Arcadesys/tak-box/docs/V22_SEAMLESS_CHECKPOINT.md

Superseded name: this seamless design is now **V23**. See [V23 checkpoint](V23_CHECKPOINT.md). The historical ZIP is preserved at `v22/release/archive/tak-v22-seamless-before-v23.zip`; V22 source and guide now refer to the original corner-hook baseline. The following records the earlier delivery.

# V22 seamless exterior revision

Outcome: rounded flush closed exterior, recessed centered outer-side hook including pivot/collar/catch, recessed offset board grips, and integrated rounded hinge-end shoulders. Preserve 32.6 mm thickness, full 180 mm field, exact original 42 flats and solid 8 mm Cat/Witch capstones, captive main hinges. User authorized this local revision; no printer job or merge.

Route: short design plan for centered closure/board motion and embedded hinge-end clearance, then bounded workhorse/medium implementation and focused checks in this context. Maintained role mapping read; no model switch or delegation claimed. Actual model/effort and usage counters unavailable.

Plan: recess closure into spare side margin ahead of the first stone column; remove projecting board tab, add broad rounded grips offset along the side. Move opposed hinges into end margins outside the field, retaining their 3 mm pins and 0.4 mm gaps, and replace rectangular roots with rounded shoulders. Verify cropped actual closure and hinge-end geometry before full exports/slicing. Then check exact loaded geometry and motion, meshes/readback, slices/layers, provenance and freshly extracted revised ZIP.

Baseline preserved: existing v22/release/tak-v22-print-kit.zip and its 02f8a09 source revision; new archive will be named tak-v22-seamless-print-kit.zip. V18–V21 and user-extracted folders remain untouched.

Current: implementation and digital checks complete. Closed envelope 101×200×32.6 mm (baseline 111.8×220.2×32.6); hook parks at 90° below the boards. Eight full parts across three plates: 41,899 s / 272.16 g. Optional hinge trial 1,556 s / 5.31 g; closure trial 3,175 s / 13.39 g. All required replacement parts are explicit in the guide; capstone CAD unchanged.

Evidence: 59 geometry, 37 field, eight hardware, 29 exterior/access/wall, 254 preliminary mechanism, 20 plate, three filament toolpath, 32 captive-hinge, 20 capstone, eight hinge-trial and 129 closure-trial checks pass. Three full slices and two trial slices match named exported meshes and placement. Selected layers, captive-gap plots and exported CAD previews reviewed. Baseline ZIP hash matches docs/V22_BASELINE_ARCHIVE.json. Fresh revised-ZIP audit passes: 122 payload hashes, Python syntax, 14 local links, all eight independently reconstructed parts with zero Boolean symmetric difference, and unchanged baseline ZIP hash. Receipt: docs/V22_SEAMLESS_PACKAGE_CHECK.json. Archive SHA-256: d48410b2b090c39770dcf3f2bf56b243482c84fbbc51b89927d7b21dd7d633a4. Defining source: 4859c9cdd515cd7f12324a99423b8795fa7984ac. V18 freeze and V19–V21 package verifiers pass; no prior-version tracked files changed.

Delivery: v22/release/tak-v22-seamless-print-kit.zip; guide v22/START-HERE.md; actual-geometry views v22/previews/02-closed.png, 04-hook-closed.png, 05-hook-open.png and 12-rounded-hinge-end.png. Committed and pushed on codex/v22-print-in-place. Draft PR #27 is updated as “V22: recessed center hook, rounded hinge ends and flush board grips” (https://github.com/Arcadesys/tak-box/pull/27); not merged. Geometry/source commit 4859c9c and packaged artifact commit 19b8773. No physical acceptance observed. Next small physical trial is the supplied 53-minute recessed closure coupon, followed by the 26-minute hinge coupon; the full build is also supplied. No printer job, merge, paid generation or new agent.
