Arcadesys/tak-box/docs/V23_BOARD_INLAYS_CHECKPOINT.md

# V23 board inlays checkpoint

Outcome: a separate replacement for V23 sliding-board plate 02 with flush black/white grid and retained celestial artwork, assigned to two separate silk accent slots. User selected V23 on October 6, 2026 after resolving the older checkout's V18 instructions.

Scope: `v23/board-inlays/`, its links in the V23 guide and project brief, this checkpoint and generated-file review attributes. Retain full 180 mm 5×5 field, 36 mm pitch, existing slide/catch/grip interfaces, all base/hook/capstone geometry and original kits. Exact piece package: V23 original Cat/Witch 20×20×8 mm flats and supplied solid flat Cat/Witch capstones. Weighted and curled sets remain unqualified.

Route: one bounded workhorse/medium pass in the existing execution context. Role mapping read; no model switch or delegation claimed. Actual model/effort and usage counters were not exposed. Source baseline 071469c on `codex/v23-seamless`; focused branch `codex/v23-board-inlays` in a managed isolated worktree. Original primary-checkout modification to a V16 3MF is untouched.

Current: separate black/white and four-colour board projects and small trial projects built. V17's 0.8 mm recessed grid is filled to the V23 face. V16 celestial CAD is reused in its original cell positions, translated to Z15.3. Inlays are 0.6 mm deep. The trial measures 90.2×36.8×1.8 mm and includes two full cells plus the seam half-cell. Gold and purple are example preview colours. Slots 3 and 4 follow the original V16 orange/purple motif groups. Silk uses two clearly labelled generic PLA placeholders; select both actual spool profiles and reslice before printing.

Evidence: 275 fresh CAD/mesh/STEP/field/piece/motion/3MF checks pass in `v23/board-inlays/reports/geometry.json`. All four CC2 local dry slices pass named mesh, colour-slot and placement readback in `reports/slicing.json`. Eight actual Gcode colour-layer checks pass in `reports/colour-layers.json`, with white/accent deposition at board locations on the six expected 0.10 mm inlay layers. Actual exported STEP previews and the last sliced inlay layer were inspected. `reports/package-audit.json` records the release ZIP's payload count, SHA-256, CRC, syntax and four-project audit; its root contains dependency sources and the option guide.

Commands: `python v23/board-inlays/source/build.py`, `render.py`, `slice.py`, `inspect_layers.py`, `package.py`, all via `/Users/arcades/Documents/GitHub/tak-box/.venv/bin/python`. Dependency versions, platform, source hashes, profile hashes and exact slicer commands are recorded in the option reports and `source/requirements.txt`. Renderer uses VTK. Installed ElegooSlicer CLI uses the retained CC2 0.4 mm printer profile, 0.10 mm layers after a 0.20 mm first layer, supports and a prime tower.

Corrections during verification: the first full-board readback detected a 0.001012 mm Z shift from using OCC's tolerance-expanded bounding box. Plate placement now uses actual tessellation minima; the repeated readback passes with float32-level error. The initial toolpath parser missed extrusion values written with a leading decimal point (for example `E.04`); numeric parsing was corrected and all expected coloured deposition layers now pass. No geometry or slicer assignment defect was inferred from that parser failure. Generated logs retain the final successful run; these earlier checker failures are recorded here.

Limitations: motion is sampled, not a continuous swept-volume proof. The extracted ZIP passed isolated dependency import and CAD smoke checks. Physical colour purity, adhesion, silk bonding, surface feel, rail friction and loaded retention remain unchecked. The trial does not test rails or catches; dry-fit one full replacement board before printing its mate. No printer job, paid generation, merge or physical acceptance is claimed.

Next: review the replacement option, print the small colour/finish trial with selected material profiles, then test one full board. The existing full-case plates 01 and 03 remain the source for bases and hardware.

Delivery: the option is reviewed in [PR #29](https://github.com/Arcadesys/tak-box/pull/29), stacked on the retained V23 branch. The initial one-accent delivery was committed at 2e4a839; the user explicitly requested two accent colours on October 6, 2026. The follow-up restores the separate original orange/purple artwork groups, uses four filament slots, and removes the combined-art exports and single accent placeholder. Geometry, colour-layer, slicing and archive receipts have been regenerated. Current ZIP checksum and payload count are in `v23/board-inlays/reports/package-audit.json`.
