Arcadesys/tak-box/docs/V26_CHECKPOINT.md

# V26 mechanism review checkpoint

## Contract and route

Outcome: a reviewable wider sliding-board clip and captive side-hook candidate, with print-ready small trials and current CAD/mesh/3MF/motion/slicer evidence. Scope: new v26 package, controlling guides and focused branch/PR; preserve V25/V24 kits and user-extracted folders. Completion evidence is digital geometry, readbacks, actual CAD previews and dry slices. Physical strength is not inferred.

Route: bounded workhorse / medium in the existing execution context; maintained role mapping read. No model switch claimed; no agents. Named design uncertainty: captive-hook print support and collision-free motion. Resolved with targeted geometry checks before the integrated verification pass.

## Current state

Parent: c101d7d6585c363e23cf140f9059f38a96a8d6c8 on codex/v25-fixed-piece-guides (draft PR #35). V26 branch: codex/v26-captive-hook-catch. Thin-clip report confirmed by user as the small sliding-board clip. User explicitly asks for a PIP hook. Original 1.2 mm arm becomes 2.4 mm, gradual 3.2 mm root and 1.2 mm blend; same 54 mm plan span and assumed 2.8 mm flex travel. No stress, force or fatigue rating claimed.

The hook keeps its closure lever/tooth, enlarges its bearing to 11.6 mm outside diameter and prints parked on an integral foot. Fixed 4 mm axle, 2 mm outer cheek, 0.4 mm radial/face clearances. Existing filament passage is filled, avoiding an isolated internal void. A 7 mm rotating relief clears the foot; the 3.4 mm fixed lower frame bridge sits outside that sweep. Hook moves 0.4 mm inward; board notch extends from X5.7 to X6.2 outside the full field. Original keeper remains.

Rejected first hook fit had 0.454 mm3 overlap at 30 degrees and 0.908 mm3 at 90 degrees. The original export failed the single-component mesh check because the unfilled old pivot bore became an enclosed void (negative 14.763 mm3 inner shell). Neither rejected export is delivered as a print project. Failure records are retained. Final solid topology is checked before slicing.

Fixed guides, main PIP geometry, full field, exact original flat/capstone package and outside dimensions are retained. Both integrated bodies/boards require replacement; hook prints with the left body, no inserted axle or collar. Small trials isolate the hook bearing and complete clip; hook trial has a thickened fixture floor outside the moving envelope. Whole-case loaded strength and rounded-cover underside integration remain pending.

## Evidence and next step

Build: source/build.py; trials: source/trial.py; dry slice/readback: source/slice.py; actual CAD views: source/render.py. Python 3.12 / CadQuery 2.7 / ElegooSlicer 2.4.2 on the recorded host. Reports retain exact commands, profiles, hashes and failures. No printer dispatch or physical acceptance.

Next physical gate: cool and gently free the captive hook, pull along its axle both ways, inspect axle/cheeks after 20/100 cycles; insert/release the full-length clip by hand and inspect its root/effort after 20/100 cycles. Reject fused motion, cracks or excessive release effort. Complete-case print and loaded transport follow only after mechanism trial observations.

The parked lever has underside clearance outside the piece wells. A final audit rejected the original 0.173 mm lever-to-well-corner gap; the revised underside opening clears that region. The 3.4 mm stone floors and fixed guides remain intact.

Final digital evidence: 908 integrated solid, loaded-piece, slide/fold, capture, mesh and 3MF checks; 96 mechanism-trial checks; 51 exported material/clearance/keeper audits. The locked hook obstructs early opening at 179/178/177 degrees; that is nominal geometric retention, not a force rating. Own-body clearance is 0.4 mm through checked 0–90 degree hook travel. Eleven actual dry-sliced hook radial/face-gap and support-centerline checks pass, minimum sampled conservative 0.50 mm bead-edge gap 0.32 mm. Both trial projects preserve named watertight meshes within 0.002 mm surface / 0.05 mm3 volume tolerance. Four walls, 0.20 mm layers, build-plate-only supports, no brim, CC2 PLA; inherited bed metadata warning retained. Hook trial: 1,493 s / 4.93 g; clip trial: 2,537 s / 9.51 g. Seven actual CAD/path images reviewed with large captions and a clear longitudinal bearing section. Review still awaits physical prints; full sliced V26 kit and rounded-cover underside remain open.

Package evidence: all six preceding V25 ZIPs remain byte-identical. An isolated extraction of the V26 review rebuilt both small trials without the checkout; all four rebuilt STL surfaces and volumes match within the recorded tolerances. This does not claim an isolated full-CAD or slicer rebuild. Captions are composed in a separate PIL-only process to avoid dropped leading glyphs after repeated VTK renders. The V26 review is stacked on open draft PR #35; no merge or printer dispatch.

## Combined trial plate

User asks for both trials on one plate. Route: bounded workhorse / medium in the existing context, no model switch or agents. Scope: placement and grouping only; unchanged hook/clip geometry and individual projects. New source/combine.py imports the four actual exported STEP parts, moves both clip parts 32 mm in X, leaves the captive hook/mount unchanged and exports one assembly of four named meshes. Hook-to-clip spacing is 17 mm; all parts fit the CC2 bed. Nineteen placement, topology and 3MF checks pass. New combined slice receives the existing mesh/profile readback and eleven radial/face/support checks; physical acceptance remains unchecked. No complete-case geometry recheck is needed for unchanged parts.

Combined slice passed: 3,925 s / 13.92 g PLA; four named watertight mesh readbacks, preserved one-assembly placement and eleven hook bearing/support checks. Individual projects remain byte-identical to a1a9b2709323d74d3e68bea22fd73d9dbbc3133d. Combined CAD placement preview reviewed; package repacked. Physical strength and release remain pending.

## Board-release ergonomics assessment

User reports that pressing the sliding-board tab while pulling the board was very awkward. A thicker clip does not resolve that simultaneous action. Proposed next direction: remove the individual flex catches and restore solid board margins; let the opened case hook release both boards for withdrawal. User choice between this approach and a separate latch that stays released is pending. No geometry changed in this assessment, and the combined plate still contains the stronger flexible-clip candidate.

Route: bounded workhorse inspection in the existing context; no model switch or delegation. Source revision: eb1a114f773069a6a662d7f2cea9456f901bac51. Environment: existing CadQuery 2.7 / Python 3.12 CAD runtime. Command: import v26/source/build.py; for each side use board(side, c.BOARD_RELEASE), apply c.slide at 0, 1, 2, 3, 4, 5, 6, 8 mm, fold the right board 180 degrees, and measure ov against hook(0) and hook(90). The assumed released clip isolates the hook obstruction from the individual clip.

Results: both seated boards have zero hook overlap; at 1 mm withdrawal the closed hook overlaps left board by 6.416685 mm3 and folded right board by 5.085218 mm3. Closed-hook overlap remains positive at all checked 2–8 mm positions. The parked 90-degree hook has zero overlap with both boards at each checked position. This supports a candidate shared retention mechanism; it does not establish retention force, comfort, or unlatched board security. Full removal, loaded motion, restored-margin clearance, mesh/readback and physical handling must be checked after any geometry change. Existing sliced trials and ZIP remain unchanged.

## Full plate build authorized

User approves shared hook retention and explicitly asks to build the plates without waiting for the small trials. Scope: remove board flex tabs, restore bevelled solid margins, retain PIP hinges/fixed guides/captive side hook/full field/original inlays and build the complete sliced CC2 kit. No printer dispatch. Preserve the previous mechanism-review ZIP and all V25 assets. Route: workhorse / medium in the existing execution context; no model switch or agents. Completion evidence: integrated solids and loaded motion, shared hook obstruction, vertical rails and inward stops, exported meshes and native 3MF placement/material readbacks, actual dry-sliced hinge/hook gaps, exported-CAD previews and package readback. Strength and handling remain physical observations, now deferred at the user's instruction.

The first full build passed the slide/loaded-fold checks but failed the added 1 mm inward-stop check: removing the flexible catch also removes its inward seating stop. Preserved failure log: v26/reports/build-full-initial-failure.log. The old case-only stop catches later (positive at 12 mm); it is insufficient for independently seated closed covers. Narrow repair: a rigid 4 x 6.1 x 4.7 mm shoulder outside the field, X52.6..56.6/Y2.7..8.8/Z11.8..16.5 (mirrored right), meets the front rail's X57 start. It has 0.3 mm clearance to the front wall and shares the original flat underside. Focused left trial: zero seated/outward overlap at 0, 0.5, 1, 2, 4, 8, 16, 32, 54, 80, 106 mm; positive inward overlap 0.072 mm3 at 0.5 mm and 0.432 mm3 at 1 mm. This is a fixed seating shoulder, not a pressable catch; the case bodies and inlays remain unchanged. Full affected checks rerun after this repair.

Final full-plate digital evidence: 916 integrated CAD checks, 62 full board/capstone export and raw plate checks, 51 exported material/closure audits, all 15 named sliced meshes read back within 0.002 mm surface / 0.05 mm3 volume tolerance (maximum observed surface error 0.00001714 mm), and 25 main-hinge/hook bearing checks. Minimum sampled conservative 0.50 mm bead-edge gap is 0.3191 mm; no sampled support centerlines enter the bearing cavities. All three slices are inside the CC2 build volume. Three actual colour-deposition checks verify white and both accents on six 4.2..4.7 mm layers, excluding the prime tower. Current estimates: body/hook 34,079 s / 164.56 g, board pair 28,854 s / 121.19 g, optional capstones 990 s / 3.78 g; total 63,923 s / 289.53 g. Four walls throughout; 0.20 mm case/capstone and 0.10 mm boards; actual silk profiles remain placeholders. The inherited bed metadata warning is retained.

Rendered exported CAD and sampled actual paths were inspected. Initial case-plate render failed on the new captive-hook label; the colour mapping was repaired (full-render-initial-failure.log). Reusing a PIL font also dropped the leading Plate glyphs from the second plate caption; fresh font instances per image repaired this, and the legible board caption was reviewed. Capstone shading was darkened against the white background and labelled by position for accessible review. Current kit is V26-PRINT-KIT.zip / FULL-PRINT, with START-HERE instructions and reproducible bundled sources. Physical strength, comfort, wear, loaded dumping/transport and the V17-style underside remain unobserved. No printer dispatch.

Package completion: 141 ZIP entries audited by CRC, byte counts and SHA256. All six preceding V25 archives and the prior V26 mechanism-review ZIP remain byte-identical (seven preserved archives). In an isolated extraction, all ten named raw board meshes and both capstone meshes rebuilt with identical vertex arrays and triangle records. This rebuild uses bundled exported STEP geometry for boards and procedural capstone source; it does not independently repeat the full case CAD or slicer run. Reports/full-reproduction.json names the exact final ZIP hash. The authoritative worktree remains the V25-managed checkout on codex/v26-captive-hook-catch, stacked draft PR #36; the user's untracked v25/PIP-FIXED-STORAGE/v25 extraction is preserved.

## Main hinge mismatch reported by user

The user supplied a main-hinge close-up and states that it is not the captive hinge discussed. Current sources confirm the main joints are inherited opposing single-ended peg/socket stations (case.py pip_pin/pip_socket and PIP_STATIONS), while only the side hook has an axle fixed between cheeks. The earlier B filament study instead places a central moving bearing between two fixed supports (STRENGTH-TRIAL and REINFORCED-B-TRIAL FIXED/MOVING; production FIXED-STORAGE has two such stations). The switch to PIP restored the older V16 mechanism instead of carrying that support arrangement forward. Digital checks covered the delivered geometry, not fidelity to that intended hinge design. Prior full ZIP is preserved and the local guide is marked under correction.

Outcome/scope: identify and correct only the main hinge mechanism while preserving fixed guides, tab-free covers, hook retention, original pieces and field. Route: mechanism judgment in the existing context, then bounded workhorse CAD/slicing; no model switch or agents. Pending user clarification: printed axle permanently fixed between two supports on one half, with the other half's central bearing around it. No main-hinge geometry changed yet. Next: confirmed hinge arrangement, actual exported hinge detail before regenerating full case/cover motion, mesh and 3MF/slicer evidence. Current case plate and ZIP must not be described as the corrected captive design.

## Double-supported main hinge confirmed

User confirms the intended main hinge: two fixed supports holding a printed axle, with the opposite half's moving barrel trapped between them. Outcome: replace only main hinge stations and regenerate current V26 case plate/kit, retaining tab-free covers/fixed guides/side hook/full field. Scope: two 9 mm outer barrels, each 3.2 mm moving bearing between 2.5 mm fixed cheeks; integral 4 mm axle, 0.4 mm radial and face gaps, full-height 8 mm roots, original common axis X98/Z17.5 and 102.5 x 200 x 35 mm envelope. Role: bounded workhorse execution in this context after clarified mechanism judgment; no model switch or agents. Evidence required: both supports/axle as one fixed solid, closed moving bore and bidirectional capture at each station, integrated loaded slide/fold, exported mesh/3MF and actual revised bearing paths, then revised full kit. Superseded opposed-pivot ZIP and case plate are preserved under v26/archive/previous-main-hinge (ZIP db35b5db3caee5e3d9949e3dc533835be2de00983649a9685ad243a3e22b97fa). Physical strength remains untested.

### Corrected captive main hinge evidence

`build.py` with the retained CAD Python 3.12.13 / CadQuery 2.7.0 environment passes 943 checks (`reports/build-double-supported.log`, `geometry.json`). Both axles and four supports belong to one fixed body; each central moving barrel has a closed bore, axial capture in both directions, radial capture and full-height roots. Loaded fold 0–180 degrees every 2 degrees and board slide 0–106 mm every 2 mm pass. Exported review audit passes 51 checks. Full CAD renders include enlarged main-hinge and section views; final captions use the system Arial font to avoid missing initial glyphs observed with the Matplotlib font.

ElegooSlicer 2.4.2 dry-sliced the revised raw case assembly. The first support-face verifier incorrectly selected tiny infill/perimeter gaps inside the barrel; the corrected verifier probes the two nominal CAD face interfaces directly, rejects extrusion covering either gap midpoint, and measures nearest bead edges. Final `slice_full.py --case-only --verify-only` validates the existing new slice without repeating it: 37 main/hook path checks pass, minimum main support-face gap 0.3202565 mm with assumed 0.50 mm bead width, and no support centerlines in bearing/face cavities. Three case meshes and the 12 unchanged board/capstone meshes pass readback. Both other raw/sliced plates and profiles match the earlier SHA256 receipts. Revised case 34200 s / 163.81 g; kit total 64044 s / 288.78 g. No printer dispatch or physical acceptance.

Packaging passes: 145 ZIP entries, 144 audited payloads, 8 preserved archives. Isolated board/capstone rebuilding reproduces all 12 named meshes with identical vertices and triangles; full case CAD and slicing are covered by the current local build/readback, not independently rerun in extraction. Corrected ZIP SHA256: 57fdf9cab1ff7c38fd1a899682711cd065d6e87db9d090b236bdf5537b6bec55. Source compilation and git diff whitespace checks pass. Next: push the focused PR and review the actual print for freedom, cracking, looseness, loaded retention and handling. Old printed components/ZIPs remain preserved.

### Modest outside corner rounds — October 8

User asks for a little rounding while this work continues. Scope: increase the two outside case corners per half from 3 mm to 4 mm radius and add 2 mm rounds to the boards’ two outside corners, away from the common hinge axis. Preserve the 180 mm field, inlays, guide geometry, latch and full-height hinge supports. Proposed 4 mm case cuts remove about 24 mm3 per corner and retain one valid solid; rerun integrated clearances, exports, board plates and slices because board geometry now changes. The earlier unchanged-board slice receipts apply only to the pre-rounding snapshot. Role remains bounded workhorse in the same context.

Rounded build passes 947 integrated CAD checks, 51 exported audits and 62 regenerated board/capstone plate checks. All three full projects are sliced again and pass 15 named mesh readbacks plus 37 main-hinge/hook path checks. Estimates: case 34152 s / 163.71 g; boards 28819 s / 121.17 g; capstones 990 s / 3.78 g; total 63961 s / 288.66 g (17h 46m). Actual exported corner preview shows the case and seated board together. No geometry changes to guide layout, original inlays or the confirmed captive axle/support arrangement. Current geometry build log: build-double-supported-rounded.log. Physical tests remain open.

Final rounded kit audit: 148 ZIP entries / 147 checked payloads, 8 preserved archives, and all 12 isolated board/capstone meshes reproduce identical vertices/triangles. ZIP SHA256: fdd45edecb9544de774ffb7beedfaa130afc947a700d40090deb65c717c5aaad. Current source compilation and whitespace checks pass. Ready for focused PR update; actual hinge strength, wear, handling and loaded retention remain unchecked.
