Arcadesys/tak-box/v18-case/ACCEPTANCE.md

# V18 full-build physical acceptance

User reports the clasp trial has been printed. The user also confirms their earlier hinge test used 1.75 mm PLA filament and reports it held in place. Its component revision, loads and cycle count are unknown. The revised side-hook / 2.0 mm-bore complete case has no observed physical acceptance yet.

Record component revision/project hashes, filament, spool preset, temperatures, support settings, photos and measured failures. Keep every unobserved item unchecked.

- [ ] Both housings and all spring sections print cleanly; supports remove without damage.
- [ ] All four leaves rotate freely on the shared axis; filament pins stay retained and caps clear the field.
- [ ] Filament passes through every 2.0 mm printed bore without forcing; bonded end caps hold while leaves rotate freely.
- [ ] Both board snaps engage comfortably, locate a flat 5×5 field and release without tools.
- [ ] Both drawer buttons latch positively and release comfortably.
- [ ] Drawer stops retain the drawers at full access and deliberately release for maintenance.
- [ ] All 42 original flats fit, stay enclosed while folding and can be grasped individually.
- [ ] Both original capstones can be retrieved comfortably, including using the floor finger ports.
- [ ] Hatch is captured, latches closed and does not release during carrying.
- [ ] Hook seats over the headed pin and completes ten gentle release cycles without damage.
- [ ] Hook pivot friction holds its position in every carrying orientation and remains comfortable to operate.
- [ ] Hook does not rotate open during shake, inversion or ordinary contact; repeat after wear cycles.
- [ ] Pins stay fixed at their designated stationary mounts; all intended moving joints remain free of adhesive.
- [ ] Loaded opening and repacking never expose an unsupported piece.
- [ ] Loaded shake/invert/carry tests retain all flats and capstones without objectionable rattle.
- [ ] Loaded field stays aligned without excessive rocking or permanent pin bending.
- [ ] Longer repeated-operation test shows no cracks, whitening, permanent set or sticking.
- [ ] Record actual full hardware envelope, finger effort and play.

Stop for binding, forced assembly, cracks, whitening, stuck buttons, unexpected release or lost hardware. Report the component and direction of motion. Digital clearance is not physical success.
