Arcadesys/tak-box/full-size-pagoda-v1/CHECKPOINT.md

# Home-board cassette comfort checkpoint

Outcome: easier flat access and recessed grips for a loaded two-handed lift.
Route: one bounded workhorse pass; medium effort requested by maintained role
mapping. Desktop model/effort was not switched or independently verified.
Scope: cassette geometry, exported tray files, previews, checks and documentation.
Baseline: 88bc668 (merged PR #19); branch codex/cassette-comfort.

Current state: dividers lowered to 20 mm (8 mm exposed flat edge); 20 mm row
notches; 0.5 mm contact chamfers. Two 50 x 10 mm side recesses have 45-degree
roofs, retaining a nominal 6 mm rim before chamfer and 4 mm seat at the
deepest roof. Layout 5+5+6+5,
capstone seats, outside size and stack registration remain compatible digitally.

Evidence: full geometry/mesh/3MF build passes (13 meshes, 9 plates), including
all 21 exact Cat/Fox pieces, grip void/ledge witnesses and old/new stack orders.
Tray slice passes without supports (181.97 g, 12325 s); eight unchanged plates
reuse exact input-hash-matched slice evidence. Eight actual-mesh previews;
partial cassette, side grip and full Cat/Fox access views inspected.

Resolved build failure: a combined contact chamfer produced invalid geometry.
Cleaned geometry and separately validated edge groups produce a valid solid.
No model geometry was repaired after export. Unchanged meshes are byte-identical.

Blockers/limits: physical grasp, grip-rail flex, printed release and transport
retention untested. Next: one cassette loaded handling trial before printing
its mate; compare stacking to the previous cassette if available. No printer
job or paid generation initiated. Review: https://github.com/Arcadesys/tak-box/pull/20 (draft).
