Arcadesys/tak-box/home-board-compact-v1/CHECKPOINT.md

# Compact home-board checkpoint

Outcome: smaller footprint and height, preserving the current playing space.
Scope: additive home-board-compact-v1 package, project brief and README links.
Route: one bounded workhorse pass; medium effort requested by maintained mapping.
Desktop model/effort was not switched or independently verified. No delegation.
Baseline: 77ba393, cassette-comfort PR #20. Branch: codex/compact-home-board.

State: 240 x 232 x 43 mm including felt allowance. Two 112.2 x 174 x 30 mm
cassettes share one level; front/rear tabs extend total length to 186 mm.
Field 210 x 210 mm, 42 mm pitch; existing full-size stones/capstones/backing.
Capstone chamber and 5+5+6+5 layout retained. Four board-support pads and deeper
board grip openings keep the removal paths and end finger corridors clear.

Evidence: 8 valid watertight mesh parts, 5 named millimetre 3MF readbacks; all
exact 21-flat Cat/Fox sets and actual capstone bounds fit. Support contact,
lateral allowance, independent vertical removal and geometric finger-proxy
insertion/lifting pass. Three changed plates freshly sliced without supports;
two shared board plates reuse exact input hashes. Six actual-mesh previews.

Resolved failures: 0.5 mm divider chamfer invalid in the narrower cassette;
0.4 mm independently valid, with original 0.5 mm capstone/tab bevels retained.
Support-view render initially reused the exploded list; grouping corrected.

Limits: geometric finger proxies do not prove human comfort, and connectivity
does not establish tab strength. Physical fit, board deflection and transport
retention remain untested. No latch, printer job or paid generation added.
Next: two 19 g total grip coupons, then one loaded cassette before its mate,
followed by printed platform/board support and repacking trials.
Review: [draft PR #21](https://github.com/Arcadesys/tak-box/pull/21), stacked on
PR #20 while that base is open. Final source/profile/input hashes and 3MF
bounds/volume readbacks pass; shared board files are byte-identical.
