Arcadesys/tak-box/full-size-pagoda-v1/MESHY_REFERENCE.md

# Ornament reference for the next treatment pass

Use `previews/04-packed.png` as the primary shape reference. Use
`previews/01-play.png` to understand full-size pieces and unobstructed play.
`previews/02-storage.png` explains the mechanism; it is not the silhouette to
generate. Keep the precise source CAD as the dimensional master: a generated
mesh is decorative concept material and cannot replace the board seat/trays.

Suggested prompt:

> Ornate rectangular board-game storage plinth matching the reference. Preserve
> its broad flat square playing surface, low stepped base and front finger
> opening. Sculpt exceptional deep relief ONLY into the outer side apron and
> base: large curled cat guardians, witch-hat and crescent medallions, thick
> flowing energy vines, stars and galactic orbital arcs. Pagoda-inspired eave
> edges below the playing surface. No building, tower or roof on the board.
> Keep the top clear and level. Broad sturdy relief, monochrome concept mesh.

The 248 × 240 × 72 mm shell, board seat, internal cassette frame/supports and
removal volume are reserved geometry. Two open cassettes must fit inside;
preserve their straight-up removal paths and stacked pin/socket registration.
Review each proposed treatment against those constraints before CAD integration.
No generation, paid refinement or remeshing was run for this foundation pass.
