Arcadesys/tak-box/v16-field-book/ACCEPTANCE.md

# v16 field book — physical acceptance

**NOT TESTED.**

## Print record
- Date / printer / nozzle / filament:
- Files and settings:

## Hinge
- [ ] The print-in-place hinge frees without cracked pins.
- [ ] Folds closed with the lips meeting; opens flat and stops just past flat.

## Far-edge buckle
- [ ] The tab clicks into the slot when the book is closed.
- [ ] The closed book can't be pulled open without squeezing the side panel.
- [ ] Squeezing the panel near the far corner releases it one-handed, with no tool.
- [ ] Bag contents pressed against the panel don't open the book.
- [ ] The closed book survives shaking and a drop onto a padded floor without opening.
- [ ] 50 open/close cycles: the panel doesn't crack or whiten; the tab doesn't shear.

## Trays
- [ ] Each tray snaps in when pushed home.
- [ ] A locked tray can't be pulled out by its finger notch.
- [ ] A fingertip on the button releases it.
- [ ] Bag contents pressed against the side don't release it.
- [ ] 11 two-high stacks and the capstone fit and can be picked out.
- [ ] 50 tray cycles: no cracking or whitening of the tray arm.

## Tray inserts
- [ ] Each insert drops into its printed tray without forcing and sits flat.
- [ ] All 20 flats drop into the four lanes, slide together, and lift out with a pinch; the 21st goes in its pocket.
- [ ] The pawn sits in its saddle and can't slide out past the stop; the pressed latch arm still clears the left wall.
- [ ] Shake the closed book: nothing rattles loose or tips over.
- [ ] The tray latch still snaps and releases with the insert in.

## Lift-out play tray
- [ ] With the tray slid out, two fingers in the back-wall slot lift the whole insert, flats included, without spilling.
- [ ] Set down beside the board, the flats can be picked from the lanes with the insert flat on the table.
- [ ] The insert drops back into the tray and the tray still snaps home.
- [ ] The finger slot printed cleanly, and the pan is rigid when lifted by it (no flexing at the pocket or saddle).

## Board glue-up
- [ ] Each plate sits flat on its base dry, with no rocking.
- [ ] Each plate drops onto its two pegs without forcing and can't slide or twist.
- [ ] After gluing, the closed lips meet flush along all three edges, and the tab still clicks.
- [ ] No glue in the tray channel: both trays slide in and click.

## Board and case
- [ ] The inlaid white grid reads clearly on black; stones slide over the lines and inlays without catching.
- [ ] Stars, galaxies, planets, moons, sparkles and comets print crisp with no colour bleed.
- [ ] The open board is flat across the seam (straightedge).
- [ ] The case has no sharp edges or snag points; carry it in a bag for a week.
