Arcadesys/tak-box/pieces/fox-cat-capstones-v4/CHECKPOINT.md

# Cat collar correction v4 checkpoint
Outcome: continuous Cat neck/shoulder replacing the broad outlined strip; Fox v3 unchanged.
Scope: Cat neck/shoulder and narrow jaw junction cleanup, v4 exports/previews/reports, combined 3MF. No paid generation, box edits, regular-stone changes, publishing or printer job.
Route: one bounded coordinator context; no agents. Prior mild fairing failed visual acceptance. Broader local reshape fills enclosing shoulder grooves, with protected facial regions and an exact planar subdivision before deformation.
Current: finalized local digital review package. Broad strip removed on both sides; final bounded cleanup reduces under-chin facets. Upper head/ears, far cheek, muzzle, base/tail protected and checked after STL serialization. Current before/after and all views inspected against the original reference.
Evidence: final Cat mesh/base/stability/v16 tray/insert/latch/closed-box/withdrawal/lift/all-roll checks pass; final Cat dry slice passes; combined 3MF readback matches both STLs; Fox hash matches v3 and passed evidence reused.
Limits: creator acceptance and physical fit/tactile/grasp/release/retention/durability untested. No new credits; 80 historical approved Meshy credits consumed.
PR packaging outcome: focused reviewable package with full offline rebuild, final models and provenance; no historical rejected package or redundant ZIP is tracked.
PR route: one bounded coordinator pass; preserve unrelated untracked revisions. Branch codex/reference-fox-cat-capstones starts from current origin/main (86cc444).
PR evidence: self-contained source rebuild reproduced both final STLs byte-for-byte; rebuilt labeled 3MF readback passed; rebuilt Cat front/three-quarter and Fox three-quarter renders inspected. Existing geometry/v16/slicing checks remain applicable because model bytes are unchanged. Protected-feature check passes without an external v3 directory dependency.
Next: commit/push and open the authorized PR; physical pair test remains pending.
