Arcadesys/tak-box/pieces/fox-knurled-v1/CHECKPOINT.md

# Fox textured flats checkpoint

- Outcome: 21 printable fox flats that fit the current v16 tray insert in CAD.
- Scope: new flats package with source, STL/STEP, sample and set plates, preview and geometry/slicer evidence. Capstones are separate work.
- Route: one bounded coordinator execution pass; localized additive CAD work using the existing CadQuery runtime and export/slicer conventions. No delegation.
- PR route: one bounded coordinator packaging pass from current `origin/main`; preserve the board-plate edit, verify existing artifact hashes and ZIP readback, commit only the fox package and supporting documentation. User intent: a collection of custom gift sets, each with its own source and fit evidence.
- Dimensions: 19.5 × 19.5 × 8 mm, matching the insert's printed-flat envelope. Subtractive diamond knurl on four sides; recessed upper-face fox; smooth underside and contact rims.
- Existing unrelated change: `v16-field-book/plates/plate01-hinged-bases-black.3mf` is modified and must be preserved.
- Evidence passed: exact 19.5 × 19.5 × 8 mm envelope; closed, consistently oriented single mesh; zero stack overlap; four standing-wall orientations; all 21 actual solids placed in tray lanes/pocket with zero insert, tray or board-plate overlap; 1/21-object plate readback.
- Slicer passed: sample/set 1/21 objects, all on bed, no supports; sample 720 s / 3.93 g, set 9424 s / 71.9 g. Reports retain current geometry/source/G-code/project hashes.
- Preview passed: inspected the exported print mesh rendering; large labelled views show the fox, four-side texture, stack and standing wall. Source renderer now uses the verified STL to avoid expensive repeated CAD tessellation.
- Current state: source, STL/STEP, geometry and sliced 3MFs, preview and reports complete. Next step for the user is the sample print; physical gates remain open.
- Physical gates: sample grip, fox readability, edge comfort, stacking, standing-wall stability and actual tray fit.
