Arcadesys/tak-box/v25/PIP-FIXED-STORAGE/README.md

# V25 PIP fixed storage

Start with [the print and test guide](START-HERE.md). Captive PIP hinges, fixed open wells and no removable trays. Digital geometry is a prototype; physical durability remains unverified.
