Arcadesys/tak-box/v25/PIP-SQUARE-POCKETS/README.md

# V25 square holders and captive hinge

Start with [the print and test guide](START-HERE.md). Fixed individual square holders and a stationary / moving / stationary hinge with an integral central post. Physical release and strength remain unverified.
