Arcadesys/tak-box/v18-case/release/archive/README.md

# Earlier v18 build — 3 mm axles

Preserved before the user-selected 1.75 mm PLA hinge adaptation. This kit requires 3 mm rods and has 3.4 mm main/hatch bores; it is not the current filament-pin build. Source revision: `08c663b`.

SHA-256: `74a81b8cd7991f81686161288503cac2b44d07e4f63806169a2b790c4d45320e`.
