Arcadesys/tak-box/v22/release/archive/README.md

# Historical seamless delivery

`tak-v22-seamless-before-v23.zip` preserves the accepted seamless-exterior delivery originally labelled V22. The user subsequently named it **V23**. Its unchanged geometry is now supplied in [the V23 kit](../../../v23/START-HERE.md).

The original V22 corner-hook design remains at [V22 START-HERE](../../START-HERE.md) and `../tak-v22-print-kit.zip`. Do not use the archived seamless label as the current version name.
