Arcadesys/tak-box/v24/REFERENCE/models/README.md

# Mechanical reference exports

These retained monolithic board and assembly files document V24 mechanics before the four-colour surface split. Use [the actual material components](../board-inlays/README.md) and [default four-colour board project](../../FULL-PRINT/02-FULL-SIZE-FOUR-COLOUR-inlaid-boards-CC2-PLA.3mf) for the current board print. The housing, tray, hook, collar, capstone and loaded-tray exports remain current.
