Arcadesys/tak-box/v26/archive/previous-main-hinge/README.md

# Superseded main hinge

This snapshot uses two opposed single-ended peg/socket main hinges. The user confirmed that the intended main hinge has a printed axle fixed between two supports, trapping a central moving barrel. Preserve this archive as history; use the corrected current V26 kit.

ZIP SHA256: db35b5db3caee5e3d9949e3dc533835be2de00983649a9685ad243a3e22b97fa
