Arcadesys/tak-box/docs/V22_CHECKPOINT.md

# V22 checkpoint — October 5, 2026

Outcome: complete first-print kit with sliding boards, print-in-place main folding hinges and one-piece flat Cat/Witch capstones beneath the boards. The user explicitly selected V22 and accepted flat capstones. Keep the 32.6 mm thin box; remove the rear compartment and hatch. Preserve V18–V21, printed parts and the separate premium pagoda.

Route: short design pass for captive hinges and storage; bounded implementation and verification at workhorse/medium scope in one context. Role mapping read; no model switch or delegation claimed. Usage counters unavailable.

Current: eight printed parts on three CC2 PLA projects, 11 h 17 min / 268 g estimated. Closed envelope 111.8 × 220.2 × 32.6 mm. Two bases print together open flat as one assembly with opposed captive pivots. Only the side hook uses a filament pin (9.6 mm of 1.75 mm PLA). Boards, hook and collar match V21 in CAD; new bases and flat capstones required. Original 42 flat stones retained; weighted flats and old sculpted capstones are incompatible or unqualified as explained in START-HERE.

Evidence: 59 geometry checks, 37 field checks, six hardware checks, 20 plate checks, three filament toolpath checks, 32 captive-hinge checks, 20 flat-capstone checks and eight optional trial checks pass. Three actual slices match exported named meshes and placements. Selected toolpath layers and actual CAD previews reviewed. Source, profile, input/project/Gcode hashes verified. Source definition commit is recorded in v22/reports/provenance.json. Fresh archive extraction, hash/syntax/link checks and standalone CAD reconstruction are recorded in docs/V22_PACKAGE_CHECK.json; reproducible audit script is scripts/audit_v22_release.py. V18 freeze and V19–V21 package checks pass unchanged.

Delivery: v22/release/tak-v22-print-kit.zip, one v22 folder with three PRINT projects; guide v22/START-HERE.md. Draft PR #27 is stacked on codex/v21-sliding-boards. No preference remains pending. Physical hinge release, grip, slider effort, hook retention and loaded transport remain unchecked in ACCEPTANCE.md. No printer job started.

Next: print the full kit; the included 22-minute hinge trial is optional. Record actual observations before claiming physical acceptance.
