Arcadesys/tak-box/docs/V23_CHECKPOINT.md

# V23 identity correction

Outcome: consistently identify the accepted centered recessed-hook, recessed-grip and rounded-hinge-end design as V23. No geometry, dimensions, material settings, machine instructions or physical acceptance change.

Route: bounded workhorse/medium pass for path/provenance integration and deterministic relabel checks in one context. Mapping read; no model switch or delegation claimed. Model/effort runtime counters unavailable.

Baseline: seamless geometry source 4859c9c, packaged artifacts 19b8773, archived ZIP SHA-256 d48410b2b090c39770dcf3f2bf56b243482c84fbbc51b89927d7b21dd7d633a4. Preserved as v22/release/archive/tak-v22-seamless-before-v23.zip. Original V22 source/package restored from 02f8a09; its corner-hook envelope is 111.8×220.2×32.6 mm. V23 remains 101×200×32.6 mm. Earlier archives and user extractions remain intact.

Current: V23 files copied from the accepted archive; labels, generated preview titles, current profile identity and package paths now identify V23. Geometry and operational behavior are unchanged. 38 CAD exports are byte-identical; geometry/check source ASTs match after version-string normalization; all 10 3MFs retain exact named meshes/transforms and executable Gcode. Machine/filament profiles match exactly; process values match except name/setting ID. Original V22 ZIP and all 94 payload hashes match. External-state correction: PR #27 had already been merged elsewhere at 4a0e714 and its remote branch deleted. After discovering this during push verification, its historical V22 title/body were restored. The V23 identity work now uses focused branch codex/v23-seamless and a new draft review against codex/v21-sliding-boards, which contains the accepted seamless baseline.

Evidence complete: current provenance records identity source ab99d397d1dd4f19f4bc35a7f24de395630c2cf3 and accepted geometry source 4859c9c. Fresh ZIP audit verifies one v23 root, three PRINT projects, all 124 payload hashes and Python syntax, 16 local Markdown links, 38 byte-identical CAD exports and equivalent 10 3MFs. Original V22 package verifier passes, and V18–V21 have no tracked changes. No full geometry/motion/slicing run was repeated; prior results are explicitly reused through reports/identity.json and reports/validation-origin.json.

Delivery: v23/release/tak-v23-print-kit.zip (SHA-256 33510a63581b1a8b5f3c5afde34ed99acf6ecd5ccfb6bc49956e6d6e2b9e1221); guide v23/START-HERE.md; closed preview v23/previews/02-closed.png; trials v23/FIT-CHECK/captive-hinge-fit-check-CC2-PLA.3mf and v23/CLOSURE-FIT/recessed-closure-fit-check-CC2-PLA.3mf. Fresh audit: docs/V23_PACKAGE_CHECK.json. Current review is draft PR #28, “V23: name and package the accepted seamless case” (https://github.com/Arcadesys/tak-box/pull/28), on codex/v23-seamless. Identity source ab99d39 and packaged delivery d78ef56 are committed and pushed. Historical PR #27 records the previous merged seamless build.

Next boundary: physical first-print evaluation using the existing included trials/full kit. Physical acceptance remains unobserved. No printer job, merge, paid generation or subagent.
