Arcadesys/tak-box/docs/V24_CHECKPOINT.md

# V24 delivery organization

Outcome: one shallow FULL-PRINT directory with exactly four clearly named sliced projects, including the full-size FOUR-COLOUR board pair; one SMALL-TRIALS directory with three trials; the extracted kit presents the same layout. Scope is organization, filenames, guides and generator paths only. Print geometry/materials/settings/toolpaths stay unchanged.

Route: one bounded workhorse/medium pass in the existing execution context. Role mapping retained; actual chat model/effort not switched or claimed enforced. No subagents. Communication audience reference read; guide targets someone opening the kit in ElegooSlicer, with explicit filenames and numbered actions.

Baseline: accepted colour-inlay delivery 4008388; retained ZIP SHA-256 077830c82ea61dda62ebe23796b720b6e71a0959e7ece998eb7015794ad209b9 now under v24/REFERENCE/HISTORY/tak-v24-print-kit.zip. Earlier pre-inlay V24 ZIP remains under HISTORY/archive. Current PR #31 is open draft, originally “V24: integrate four-colour playing-surface inlays”; PR #30 is already merged. V23/V23 R2 and earlier packages remain unchanged.

Folder findings: primary /Users/arcades/Documents/GitHub/tak-box is still on codex/recover-tak-v18-recessed-clasp at 2589129 and has no V24 folder; its unrelated modified V16 plate is untouched. Authoritative V24 is /Users/arcades/.codex/worktrees/tak-v18-print-final/tak-box/v24. Old release/v24 extraction was monochrome; release/v24 2 had the accepted four-colour board. Both extractions are preserved byte-for-byte under REFERENCE/HISTORY. Geometry-only exports stay in REFERENCE/plates, clearly separated from recommended sliced projects.

Current: root START-HERE.md, FULL-PRINT, SMALL-TRIALS, PREVIEW.png, REFERENCE and V24-PRINT-KIT.zip. All seven recommended projects are byte-identical to their accepted counterparts, including embedded G-code. Both four-colour projects read back slots 1/2/3/4 and two full-board groups versus one trial group. 31 algorithm-source ASTs remain equivalent after repository-root path normalization; 169 accepted artifact/data files remain byte-identical. Generator imports/paths and all Python syntax checked. An initial AST comparison failed because the discovery interpreter lacked Python 3.12's empty type_params field; normalization corrected this version-only difference without changing CAD or rerunning it.

Preserved design: 102.5×200×35 mm, full 180 mm/36 mm field, 8 mm supports/4 mm pivots/9 mm barrels, two loaded lift-out trays, original flats and 8 mm flat Cat/Witch capstones. Slots 1 black, 2 white grid/stars, 3/4 independent silk accents. Gold/purple are examples; actual silk profiles and reslicing remain required. Board pair ~8 h 8 min; colour trial ~1 h 12 min with placeholders. Existing V24 builds only replace board plate 02. Physical fit, bonding and durability remain unobserved.

Reproducible publishing passed from a fresh extracted kit outside Git with HISTORY absent. Seven output projects remain byte-identical; syntax, imports, paths, links and the rebuilt ZIP tree pass. All 339 user-extraction files are preserved. Source organization revision 3073c9e. Final kit has 221 payloads plus manifest, four full projects, three trials, 50 valid links, no nested ZIPs, and one v24 root. SHA-256 af9186164853e676bd1dd4c6d695a5d8ab52a0ed877bb17e952a0b166e8619eb.

Delivery: v24/START-HERE.md; v24/FULL-PRINT/02-FULL-SIZE-FOUR-COLOUR-inlaid-boards-CC2-PLA.3mf; v24/SMALL-TRIALS/03-SMALL-FOUR-COLOUR-inlay-trial-CC2-PLA.3mf; v24/V24-PRINT-KIT.zip. Review: updated and attached open draft PR #31, “V24: four-colour boards and a clear full-print kit” (https://github.com/Arcadesys/tak-box/pull/31). Organization source 3073c9e and audited artifacts 7dd3085 committed and pushed. No remaining implementation blocker. Actual silk profiles/reslicing and physical acceptance remain user-side print steps. No printer job, merge, paid generation or primary-checkout reset.
