Arcadesys/tak-box/docs/V25_CHECKPOINT.md

# V25 filament-hinge checkpoint

Outcome: printable local coupons using ordinary 1.75 mm filament axles, curved underside board-edge clearance and preserved broad lip trials. Scope: separate V25 experiment and current guides; no V24 production geometry changes, full-case integration or printer job.

Route: bounded workhorse / medium pass in one execution context. Current role mapping read; chat model/effort switching unavailable and not claimed enforced. No delegation. The run-reviewable-edits skill bounds the source/export batch. Communication audience reference read for the print/test guide.

User decisions on October 7: filament worked well; printed pins broke or did not hold the assembly. Use filament in V25, and the rounded underside board treatment remembered as V17. Preserve the flat 180 mm / 36 mm playing field, accessible removable trays, broad lip direction and side-hook backup. V24 was printed and liked but felt loose; the thin retaining clip snapped in cleanup. Exact failure mechanism and component revision remain unknown.

Sources: V24 at 8085e9d79ffff3c69f07a1cca67595994237869e, retained case CAD under v24/REFERENCE/source; earlier circular relief in v17-four-leaf/source/folio.py and later 1.75 mm filament/bond-only-fixed-barrel interface in v21/source/case.py. The user's V17 physical reference is not asserted to equal the archived steel-axle study. Initial V25 printed-pin kit remains unchanged at /Users/arcades/Documents/Codex/2026-10-07/task/v25.

Current: isolated branch codex/v25-filament-hinge in managed v25-filament-hinge checkout. Six hinge halves with 1.95/2.10/2.25 mm bores; 5.4 mm filament coupon lengths; 0.5 mm blind stop and 2.2 mm fixed bonding length; two shared curved board-edge samples; six preserved lip/seat parts. 14 printed parts total. No printed pin or collar. Unbonded outward withdrawal is explicitly allowed by the geometry and requires a cured fixed-barrel bond. Curved board samples are seated references, not retained boards or drop-in replacements.

Geometry run: retained .slicer-work/cad-venv/bin/python v25/source/build.py; PASS 646 checks, including CAD/STEP/STL, folding samples, reference-board and curved-board clearance, local field equivalence, blind stop, unbonded withdrawal, lip/tray tests and plate placement. Logs v25/reports/build.log; source/dependency/platform in geometry.json.

Verified: fresh slice/readback passes for all 14 meshes, printer/process settings and embedded G-code; estimate 10470 seconds / 36.47 g. Seven exported-CAD views regenerated; rounded board, dimensioned hinge section and plate inspected. Fresh extraction rebuild passes 646 checks and all 14 mesh surface/size/volume comparisons at 0.002 mm tolerance. Lip/seat function ASTs match the initial coupon. V24/V23/V23 R2/V17/V21 tracked paths have no changes. Final ZIP audit passes: 97 entries, one v25 root, 14 printed parts, all payload hashes and Python syntax checked. ZIP SHA-256 7075ba1bbb3f7cbd5c867683f46d221b398a2e9b99c92eaa9ec10cae26318cd7. Kit v25/V25-COUPON-KIT.zip; guide v25/START-HERE.md; sliced plate v25/PRINT/01-V25-hinge-lip-coupons-CC2-PLA.3mf. Source/artifacts committed as 824da8c. An unrestricted whitespace check flagged CadQuery STEP exporter whitespace; generated-CAD attributes now follow the existing V24 convention. Focused Python/Markdown/JSON/CSV whitespace checks pass without changing any CAD bytes. Delivery: source/artifacts 824da8c and validation record a04492b pushed. Open draft review “V25: filament hinge coupons and continuous-axle motion study” at https://github.com/Arcadesys/tak-box/pull/33, based on codex/v24-board-inlays, attached to this chat. Updated CAD relief preview opened. No remaining coupon implementation blocker; physical tests and complete-case integration remain open. Physical assembly, adhesive retention, rocking, flex life and full loaded transport remain open. Fully concealed underside linkage is unresolved; curved relief retains the above-face axis.

## Continuous-axle assessment — October 7

The user asked about filament running all the way through the board for stability, then accepted a bounded motion study before changing the kit. Scope is geometric feasibility; physical stiffness and a complete redesigned case are excluded. Architecture route requested big_thinky / medium for the named conflict; no model-switch capability was available, actual model/effort not asserted. Deterministic probing and figures stayed in the existing context; no agents.

Source current V25 at 33862f3 plus retained actual V24 boards/housings. Command: retained CAD Python v25/motion-study/study.py. Result: 1,330 assessment checks validate the recorded conclusions. Current full-length single axle rises 1.875 mm over the face; flush/buried alternatives create actual folded-board overlap. A two-axis 9.5 mm spine spacing at Z13 has a collision-free sampled board-envelope path with 2.5 mm closed face gap, but unchanged V24 housings collide at 2° outward rotation (2.0367 mm³) and increasingly thereafter. Case/link/knuckle geometry, pieces, full loaded motion and physical stability are unverified. The alternate two-axis architecture is exploratory and unselected.

Delivered study files: v25/motion-study/README.md, study.py, REPORT.json, run.log and two inspected diagrams. Existing V25 PRINT/3MF and V25-COUPON-KIT.zip stay byte-identical; no new print release or printer job. Current study outcome: a continuous hidden axle requires housing/hinge redesign; retain the working end-hinge coupon kit pending that architecture decision. Assessment source/report/diagrams committed and pushed as b60177c. The attached open draft review is updated to “V25: filament hinge coupons and continuous-axle motion study”. Study implementation is complete; adopting a new two-axis case arrangement remains a future architecture decision.

## Controlling outcome: hinge strength and retention

The user clarified: “the outcome I want is a strong hinge that won't fall apart.” This makes rooted barrel strength, no axle escape and a snug freely rotating joint the primary acceptance criteria. A long axle or concealed spine is not itself acceptance. The current printed trial is the next evidence gate; no further architecture has been selected.

Acceptance sequence: (1) dry-fit and fully cure the fixed-barrel bond; reject fused/binding joints, cracks or filament damage; (2) compare H1/H2/H3 at initial assembly, 20 and 100 cycles, checking rocking/twisting, axial pull, filament migration and new root/barrel damage under the same recorded conditions; (3) recheck after resting overnight; (4) integrate only a successful variant, then check the full loaded case for opening/repacking and normal transport. Reject growing play, axle escape, cracks or fractures. Coupon success does not qualify a complete case. Loads/forces remain recorded observations rather than invented ratings. The current bond-dependent retention still needs physical proof.

Current print kit and geometry remain unchanged. No new test or physical acceptance is claimed. This decision record is committed to the existing V25 review; the next input is physical trial results.

## Supported hinge and heated-tool retention trial

User steering: “Keep trying” and “I have a heated tool for the filament ends. Let's use that.” Outcome: a reviewable small trial with two-sided bearing support and captive filament retention in both axial directions. Scope: separate `v25/STRENGTH-TRIAL`; existing print kits and V24 production files remain unchanged. Route: bounded workhorse / medium in the current context, no delegation or model switch claimed.

Selected geometry: two fixed 2.5 mm bearings surround a 3.2 mm moving bearing; 0.4 mm gaps, 9 mm outer barrels, 8 mm roots and local gussets. Ø1.75 filament reference has two Ø3.2 × 0.6 mm formed heads inside Ø3.5 recesses, with 0.1 mm axial allowance per head. Fixed bores Ø1.95; S1/S2/S3 moving bores Ø1.95/2.10/2.25. No glue or printed axle/cap is required for the geometric retention model. Physical head quality and strength remain unverified.

Failures resolved during development: raised identification text initially occupied actual tray space, so it moved to the front margin. The earlier case's opposite-bearing clearance left the new front fixed knuckle disconnected; restoring fixture floor stock before the new running cuts joins it to the coupon. Initial broad gussets were narrowed to begin X88.2 outside the reference tray floor X87.8. Solid/mesh and actual board/tray checks are required for the resulting geometry.

Current evidence: retained CAD Python `v25/STRENGTH-TRIAL/source/build.py` passes 1,167 checks and eight single-body mesh exports, including actual V24 board/tray clearance and sampled 0–180° motion. `slice.py` passes all eight mesh/profile/G-code readbacks; estimate 5,655 seconds / 17.75 g. Slicer retains the inherited `bed_temperature_too_high_than_filament` warning: the PLA profile uses 60°C textured-bed temperature and 45°C vitrification metadata; spool/profile qualification remains physical work. Five actual exported-CAD previews were inspected for geometry and readable labels. `package.py` passes 75-entry one-root CRC/hash/syntax/link/profile audit; ZIP SHA-256 86ece451aa864eb21081b00a71c4a63c0f50f366332ef8c02a6d3b3a40ef0207. Earlier V25 ZIP still hashes 7075ba1bbb3f7cbd5c867683f46d221b398a2e9b99c92eaa9ec10cae26318cd7. Fresh extraction `reproduce.py` passes the same 1,167 geometry checks and eight equivalent mesh comparisons at 0.002 mm surface/size tolerance; tested ZIP hash matches the delivered ZIP exactly. Source hashes are unchanged. All digital gates are complete. Next physical gate: S2 forming, 100 cycles, both-direction pull and overnight checks before whole-case integration. No physical acceptance or printer job.

## Thin-body failure and reinforced B trial

User report October 7: fit coupons fell apart at the thin sample body; B means the middle fit and is assumed best. Exact printed kit, material settings, fracture geometry and loads remain unknown. Preserve the observation as fixture failure; hinge/head strength remains unproven. Outcome: a sturdier four-part B fixture without changing its working bearing fit. Route: bounded workhorse / medium in one context; mapping read, chat model switch not available or claimed, no delegation. Scope: new `v25/REINFORCED-B-TRIAL` and decision/guide updates, preserving earlier kits and V24.

Change: 2.2 mm fixture floors become 6 mm by adding 3.8 mm below the case plane. Larger local running relief clears the deeper backing; continuous 4 mm wide fixture spines connect each half. B labels are engraved away from the checked spine. The first spine probe caught an engraved letter entering its test volume; the label moved clear. B is Ø2.10 moving bore around Ø1.75 filament; fixed bores Ø1.95, support arrangement and two formed-head geometry remain unchanged. Actual bearing material parity against preceding S2 source is checked. Nominal production case thickness is unchanged.

Verified B trial: 395 geometry/export/readback checks; six actual-CAD views inspected; all four sliced meshes, profiles and embedded G-code pass, estimate 3,097 seconds / 10.29 g. Fresh extraction passes 395 checks and all four equivalent meshes at 0.002 mm tolerance. Exact delivered ZIP SHA-256 8ced9ddb737f98ca3d1ae8244da7c5f2a6d9f21eb6f82ad7a1cdc5bcf0065918; 67-entry CRC/hash/syntax/link audit passes. Earlier two V25 ZIP hashes remain unchanged. Next physical gate: reinforced B body, hinge and heads checked separately at initial/20/100 cycles, both-direction pulls and overnight rest. No printer job or physical acceptance.

## User-selected fixed wells; removable trays removed

New user decision during B verification: “let's lose the removable piece tray. I can just dump them out at the table.” This supersedes removable-tray and organised-pocket priorities for V25. Keep original piece capacity, field, colours and external dimensions. Outcome: two full replacement body prototypes with plain integral wells, B front/rear joints and no removable tray or dividers. Scope: separate `v25/FIXED-STORAGE`, actual source/exports/previews/profiles and current decision guides; no V24 or earlier artifact changes. Same bounded workhorse / medium context, no agents.

Design: replace the 2.2 mm case plus 1.2 mm removable floor with 3.4 mm fixed floors, retaining the 102.5×200×35 mm envelope and Z3.4 piece seats. Two opposed-head Ø1.75 filament axles in B Ø2.10 moving bores; left supported fixed bearings Ø1.95. Exact current V24 four-colour covers copied as hashed STEP inputs; existing cover catch and side hook remain references/reuse candidates. Broad lip and selected rounded-cover changes still require whole-case integration. Packed capacity uses 42 original Cat/Witch 20×20×8 mm flats and two supplied 8 mm V23 flat capstones. Loose pieces may shift/rattle; random packing, dumping and closed transport remain physical gates.

Verified so far: `v25/FIXED-STORAGE/source/build.py` passes 385 checks: connected bodies, open wells/floor, 44 piece seating/roof/lift probes, released-cover sliding every 2 mm, body/cover folding every 2°, packed-reference folding every 10°, axle retention, dimensions and two-body STEP/STL/mesh/3MF placement/readback. Source revision, command/environment and input hashes in geometry report. Delivery evidence: all two-body mesh/profile/G-code readbacks pass, estimate 30,162 seconds / 153.30 g (about 8 h 23 m). Four actual-CAD full-game, fixed-well and closed views inspected; ten original V24 inlay STEP inputs are byte-identical. Fresh extraction passes 385 checks and two equivalent body meshes at 0.002 mm surface/size tolerance; tested ZIP matches the delivered archive exactly. One-root CRC/hash/syntax/link/profile audit passes for 110 entries, including the four-part B trial. Fixed-storage archive SHA-256 2e20be6253a648bc97d1ff586b569e7a9526fc28d59383c1fe6030f8e40c1dd0. Earlier archives remain byte-identical. Digital implementation is complete; update existing draft PR #33. No printer job, full physical fit or strength acceptance.

## Selected PIP main hinge with fixed wells — October 7

User selected PIP, recalling an earlier strong version and expecting fixed bodies to help. The exact physically successful version is unidentified. Removable trays were internal storage, not the hinge attachment; fixed floors may improve stiffness but strength remains unverified. B is a historical filament fit, not PIP validation. Outcome/scope: separate `v25/PIP-FIXED-STORAGE` prototype, full-length hinge trial, guides and existing PR #33; preserve all preceding kits. Route: bounded workhorse / medium in the existing context, mapping read, no model switch claimed, no agents.

Parent `671606d96ef515fa9543db7ec0616fe2c357fd86`, V24 reference `8085e9d79ffff3c69f07a1cca67595994237869e`. Restore V16-style opposed 4 mm captive pivots, 0.4 mm radial/face clearance and full-height V24 8 mm roots. Added 3.4 mm fixed-floor stock is relieved before union, preserving pivot geometry and swept clearance. Both bodies print together as one assembly. Same 44 original flats/capstones, full field, accent colours and 102.5×200×35 mm envelope. Current V24 cover/hook references remain; hook still uses its filament pivot. Broad lip, catch and rounded-cover complete integration remain open.

Commands: retained CAD Python `/Users/arcades/.codex/worktrees/tak-v18-print-final/tak-box/.slicer-work/cad-venv/bin/python`, then `v25/PIP-FIXED-STORAGE/source/{build,trial,render,slice,package,reproduce}.py`; also `slice.py --trial`. Runtime Python 3.12 / CadQuery 2.7 plus VTK/trimesh/numpy/scipy/matplotlib/PIL; installed ElegooSlicer 2.4.2. Reports retain exact commands, source/board/profile hashes and limitations. Used G-code helpers were narrowed and reverified against the same projects with `slice.py --verify-only` and `slice.py --trial --verify-only`.

Verified: 402 body and 105 trial geometry/export checks, four sliced mesh/profile readbacks, 14 sampled bearing checks per plate, seven inspected actual-CAD/toolpath views. Single connected meshes, assembly grouping, original-piece seating, sampled folding, root material, surface clearance and opposed axial capture pass. Trial keeps both pivots, 200 mm length, continuous 13.2 mm-wide probed spine and exact production 3.4 mm floor. Minimum sampled conservative bead gap 0.3194 mm; no support centerline enters either checked cavity. Full-body estimate 29,609 s / 153.39 g; trial 10,727 s / 46.79 g. Build-plate-only supports / 0.8 mm XY separation / no brim. Inherited bed-temperature warning remains (60°C textured bed / 45°C vitrification metadata); spool/profile changes require reslicing.

97-entry archive audit and fresh extraction/reconstruction of both assemblies and four equivalent meshes pass at 0.002 mm surface/size tolerance. Exact tested/delivered ZIP SHA-256 `6ab929a3ac146cfcc17d7eb8d5181fefd56c9f3c6590bc994f5ac5acf1bcc86d`. All four earlier ZIP hashes checked byte-identical. Digital gates complete. Delivery target: existing draft PR #33 on `codex/v25-filament-hinge`. Physical gate: release, play, both-direction axial pull, twisting, 20/100 cycles and overnight recheck on the strip, then whole-body cover/hook fitting and loaded repacking/transport. Continuous extrusion clearance, strength and durability are unproved. No printer job or physical acceptance.

## Fixed piece guides clarified — October 7

User clarified that removing the tray did not mean removing piece guides; fixed guides are required. Outcome/scope: separate `v25/PIP-FIXED-GUIDES`, latest guides/plates/previews and controlling docs, preserving every preceding package and the user's untracked extraction under `v25/PIP-FIXED-STORAGE/v25`. Route: bounded workhorse / medium in one context, mapping read, no model switch or agents. V26 was recommended but not selected; retain V25 names. PR #33 was observed merged, so delivery uses `codex/v25-fixed-piece-guides` and a new focused PR against its merged base `codex/v24-board-inlays` (`c9c7f30791bb904b47794f19848485a95659aef3`, tree equivalent to CAD parent `9eeef7bcd351c5c23f4851a763b39f779db867ea`).

Guides reproduce the earlier tray layout, with 21 flats and a capstone per half: flat rims translated (1,0,1.2), capstone rim (1,-0.5,1.2), then mirrored right. Each is fused into the 3.4 mm floor; guide tops Z6.9 mm leave 4.5 mm of each 8 mm piece exposed. Grasp openings remain. No tray floor or handle is added. Initial compound fusion left 22 valid but disconnected solids and was rejected; individual guide fusion produces one solid per body. Failure retained in build-initial-failure.log. Hashed original empty-well bodies in reference/plain-bodies prove that all new body material is limited to guides. PIP pivots/roots, cover interfaces, field, colours and outside dimensions are unchanged.

Commands: retained CAD Python under `/Users/arcades/.codex/worktrees/tak-v18-print-final/tak-box/.slicer-work/cad-venv/bin/python`, then `v25/PIP-FIXED-GUIDES/source/{build,trial,render,slice,package,reproduce}.py`, plus `slice.py --trial`. Runtime/commands/source/input/profile hashes are in reports. Passed 542 body checks, including all 44 nominal pieces seating, 1/4/8/12 mm straight removal, 3 mm covered XY restraint at 0.4 mm lift, rear fingertip access, baseline-material parity, sampled folding, connected solids and STEP/STL/3MF readback; 105 hinge-strip checks. Four sliced mesh/profile readbacks and 14 bearing G-code checks per plate pass. Minimum sampled conservative bead-edge gap 0.3194 mm; no support centerline in the checked cavities. Eight actual-CAD/toolpath previews inspected, including enlarged guide detail. Full plate 33,656 s / 163.69 g; strip 11,219 s / 47.87 g. Inherited bed-temperature warning remains; actual spool/profile changes require reslicing.

101-entry CRC/hash/syntax/link/source/profile archive audit passes. Exact delivered ZIP SHA-256 `a17e0f3c72a07d5eec62562ba31813165b0ae1383047639712febd2cc6c682e5` rebuilt from fresh extraction: 542 body checks, successful trial rebuilding, four equivalent meshes at 0.002 mm surface/size and 0.05 mm³ volume tolerance. Five preceding ZIPs checked byte-identical. Digital implementation complete. Next physical gates: nominal piece/capstone fit, grasping and dumping, PIP release/play/retention and 20/100-cycle/overnight checks, then loaded transport. Current V24 covers/hook remain physical reuse candidates; cover catch, broad lip and rounded-cover complete integration remain open. No physical acceptance or printer job.

## Square holders and three-knuckle captive post — October 7

User asked to restore the little square Tak piece holders, then selected fixed outer knuckle / moving centre knuckle / fixed outer knuckle joined by a central post. Outcome: fixed individual pockets and an integral captive post at both hinge ends. Scope: separate v25/PIP-SQUARE-POCKETS package and current guides; preserve all previous kits, field, pieces, colours and outside size. Route: bounded workhorse / medium in one context; mapping read, runtime model switching unavailable and not claimed enforced; no delegation. Parent 9eeef7b, branch codex/v25-square-pockets. Completion evidence: connected solids, actual-piece containment/removal, cover slides, folding/axial capture, exported mesh and 3MF readbacks, sampled sliced bearing gaps, actual-CAD previews and native slicer view. Physical strength and release remain open. Current: sources prepared; next: run geometry and slice checks.

Completed digital evidence: retained CAD Python ran `v25/PIP-SQUARE-POCKETS/source/{build,trial,render,slice,package,reproduce}.py`, plus `slice.py --trial`. Main assembly passes 461 checks, full-length hinge strip 106. Source/STEP/STL/3MF readbacks, actual pieces, square rims and full-height roots, cover slides, sampled folding and integral-post capture pass. Six actual-CAD views inspected, including central-post cutaway; native ElegooSlicer opens the replacement assembly and visibly shows the square holders (docs/V25_SQUARE_POCKETS_SLICER.png). Both sliced projects pass mesh/profile/G-code readbacks and 22 bearing checks each, including radial and axial gaps and cavity-support exclusion. Minimum sampled estimated bead gap 0.3180 mm. Slice body: 33,732 s / 162.91 g; strip: 11,351 s / 47.12 g.

Initial sliced-report serialization failed on a NumPy boolean in the added axial checks. Converted it to a native boolean and reverified the same actual sliced projects; both pass. A redundant exact floating-point dimension comparison was corrected to the existing 0.002 mm CAD tolerance; dimensions pass. No geometry change was needed. The 99-entry ZIP audit and fresh extraction rebuild pass, including all four equivalent meshes at 0.002 mm tolerance. Exact tested ZIP SHA-256 ff331497d53a71533d8aa040141b1a5a25319e1f89462f029e69aedf399bc476. All five earlier V25 archives are byte-identical to parent 9eeef7b.

Source/outputs are isolated in codex/v25-square-pockets. Current state: implementation, local digital checks and native slicer review complete. Source/artifacts committed as 4265a35 and pushed; draft review https://github.com/Arcadesys/tak-box/pull/34. Next: physical hinge-strip test. Physical acceptance remains false, no printer job. V24 cover/hook fitting, broad lip/catch/rounded-cover integration, loaded transport and durability remain open.
