Arcadesys/tak-box/v17-compact-folio/ACCEPTANCE.md

# v17 physical acceptance — unchecked

Record printer, nozzle, filament, exact source hashes, profile and hardware.
Digital verification is not physical acceptance.

- [ ] Nut coupon: insert by hand, nut cannot spin, screw passes freely.
- [ ] M3×10 coupon clamps without splitting or visibly bowing the plates.
- [ ] Channel coupon accepts two actual flats; leading flat is easy to pinch.
- [ ] Clamp the coupon roof and block its cut end: inversion and shaking
      cannot move a flat through the scallop or over the side walls.
- [ ] New board hinge frees cleanly and folds flat without force or binding.
- [ ] Roof seats with all 42 flats and both original pawns, without pressure.
- [ ] Four M3×16 screws engage and clamp the roof and both folded leaves.
- [ ] Full case inverted/shaken over a soft tray: no spill or screw loosening.
- [ ] Opening board, removing roof, playing and repacking is comfortable.
- [ ] Grip from scallops works without a friction jam; note remaining rattle.
- [ ] Repeated opening/closing causes no cracks, nut spinning or loose hinge.
- [ ] Board stiffness feels better than v16; loaded stacks remain easy to grasp.

Do not carry the case loaded until full-case closure and shake checks pass.
