Arcadesys/tak-box/pieces/weighted-flat-capstones-v1/CHECKPOINT.md

# Weighted V26 piece sample checkpoint

Outcome: complete digital sample plate, with eight parts for two regular flats and two flat capstones. Cat uses slot 3, Witch slot 4, with Elegoo silk PLA profiles. Both capstones retain 8 mm height and match 0.988819 mL usable fill / 1.094064 mL closed void. The broadened Witch hat has a 1.538 mm roof. Two snap hooks capture each floor behind lips; epoxy seals the perimeter and flex slots.

Scope: new piece package and sample plate plus project brief. Regulars remain 20 × 20 × 8 mm; capstones remain within 26 × 20 × 8 mm. The user reports their V26 case already printed. Existing case geometry, plates, archives and unrelated primary-checkout changes are preserved.

Evidence: reports/verification.json points to valid solid/STEP/mesh checks, 115 V26 storage/slide/fold checks, eight-object saved 3MF readback, profile and source hashes, commands/dependency versions, rendered exports and native visible-load evidence. Slice estimate 2h 7m 34s / 26.87 g. The inherited bed/vitrification metadata warning remains. A native Slice request timed out; the CLI slice and saved G-code are verified. No printer dispatch.

Route: one workhorse context, medium effort requested for localized CAD and verification. Role mapping inspected; model switching is unavailable in this existing desktop chat, so route enforcement is not claimed. No agents delegated.

Source base: V26 7444f978933505b6808003d226c90ff9d503ebc9. The original snap generator is vendored verbatim from 863055fd146396925e2d05461b3e4696bf0c9ac4. The build's revision field identifies its ancestor; file hashes identify the actual new working sources.

Saved copy: /Users/arcades/Documents/GitHub/tak-box/sample-plates/2026-10-08-flat-cat-witch/Tak-SAMPLE-WEIGHTED-Cat-Witch-slots-3-4.3mf. Native app observation confirmed the eight-part project, CC2 0.4 mm nozzle, slots 3/4 and 0.2 mm layers before its later slice request timed out. The package rebuild used identical geometry and material/process values.

Next physical gate: print this sample, check the actual case pockets, fill without grains on the seats, snap both hooks, cure the epoxy, then check handling and leakage. Physical fit, snap retention, assembly force, wear and sand sealing are unverified. No full piece-set release is claimed.

Review: draft PR https://github.com/Arcadesys/tak-box/pull/37 targets codex/v25-fixed-piece-guides, which now contains merged V26 PR #36. GitHub reports mergeable. Geometry/source delivery commit: 896fb7178f9a7f50d823cef2815803874b2a0fdb. The diff contains only this new package and the project brief.
