Arcadesys/tak-box/archive/v13-book/ACCEPTANCE.md

# v13 book — physical acceptance

**NOT TESTED.**

## Print record
- Date / printer / nozzle / filament:
- Files and settings:

## Hinge
- [ ] Print-in-place hinge frees without cracked pins.
- [ ] Book folds closed with faces flush; opens flat and stops just past flat.
- [ ] Hinge barrels do not catch stones in the border.

## Trays
- [ ] Each tray snaps in when pushed home; the button clicks into its window.
- [ ] A locked tray cannot be pulled out by the finger notch.
- [ ] Pressing the button with a fingertip releases it; no tool needed.
- [ ] A bag's contents pressed against the side do not release it.
- [ ] 11 two-high stacks and the capstone fit; stacks can be picked out.
- [ ] Closed book held upside down and shaken: neither tray slides out.
- [ ] 50 tray cycles: arm does not crack, whiten or lose its snap.

## Clasp
- [ ] M3 screw bites the pilot; clasp pivots without wobble.
- [ ] Clasp hooks the stud and holds the book closed when carried.
- [ ] Clasp rests flat when open.

## Board
- [ ] Plates glue flat; the open board is flat across the seam (straightedge).
- [ ] Stones sit stably on the seam cells.
- [ ] Raised grid reads clearly in black on white; stones slide across lines without catching.
- [ ] Closed, the two raised grids meet without marking each other.
