Arcadesys/tak-box/center-closure-coupon/closed-fit-comparison.png

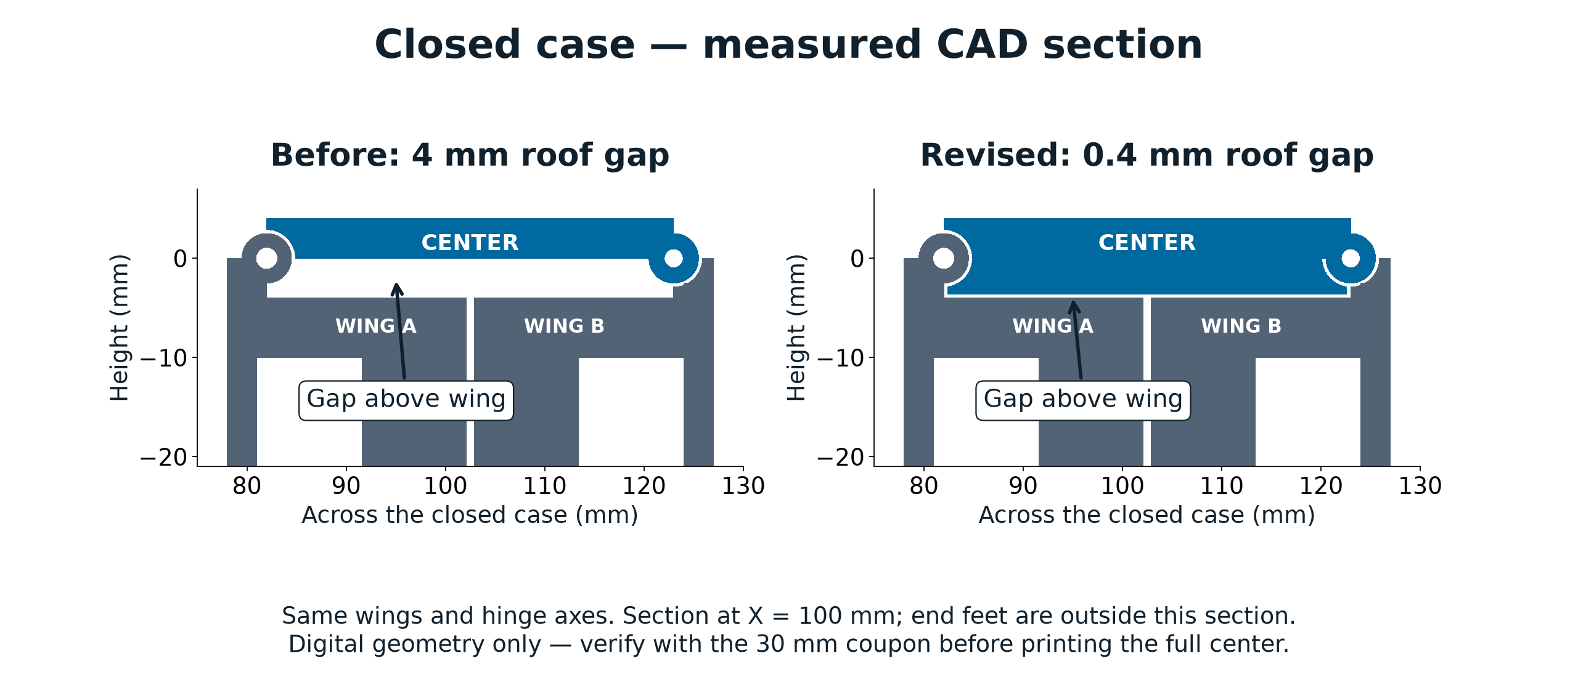
center-closure-coupon/closed-fit-comparison.png
