Arcadesys/tak-box/docs/V25_SQUARE_POCKETS_SLICER.png

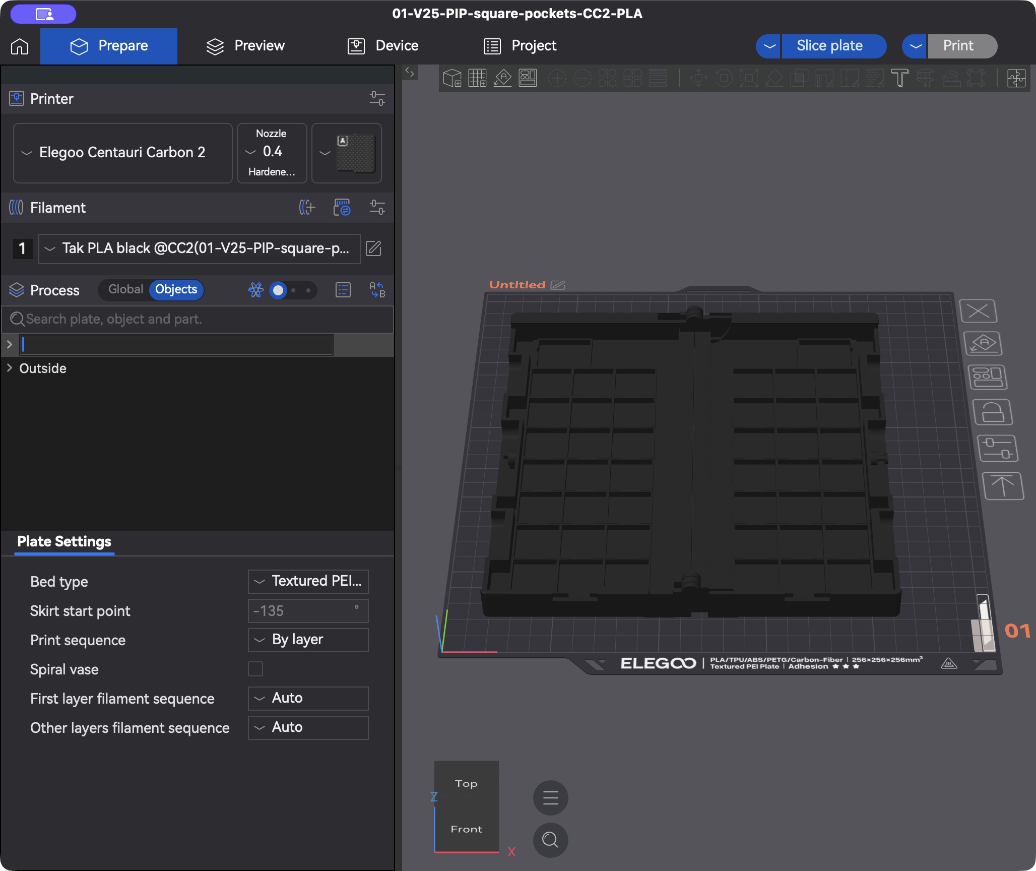
docs/V25_SQUARE_POCKETS_SLICER.png
