Arcadesys/tak-box/full-size-pagoda-v1/previews/04-packed.png

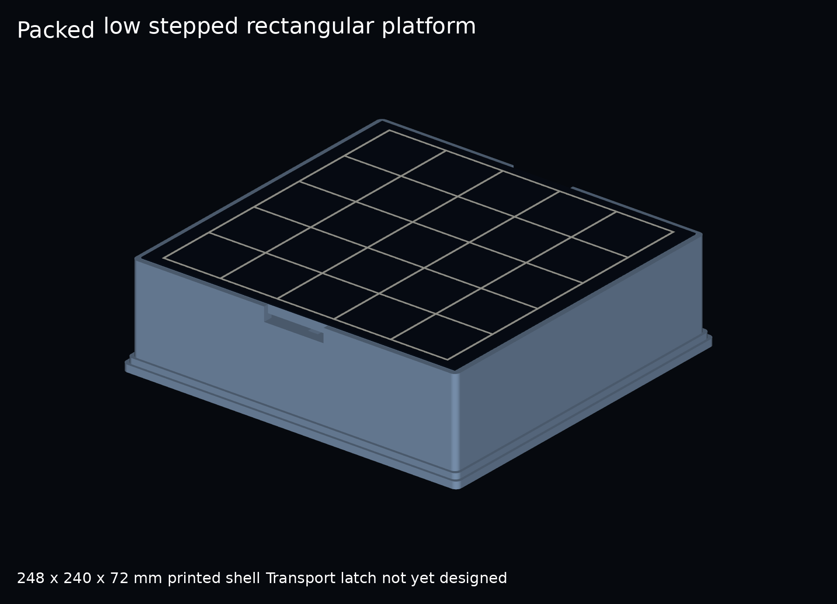
full-size-pagoda-v1/previews/04-packed.png
