Arcadesys/tak-box/home-board-compact-v1/previews/02-packed.png

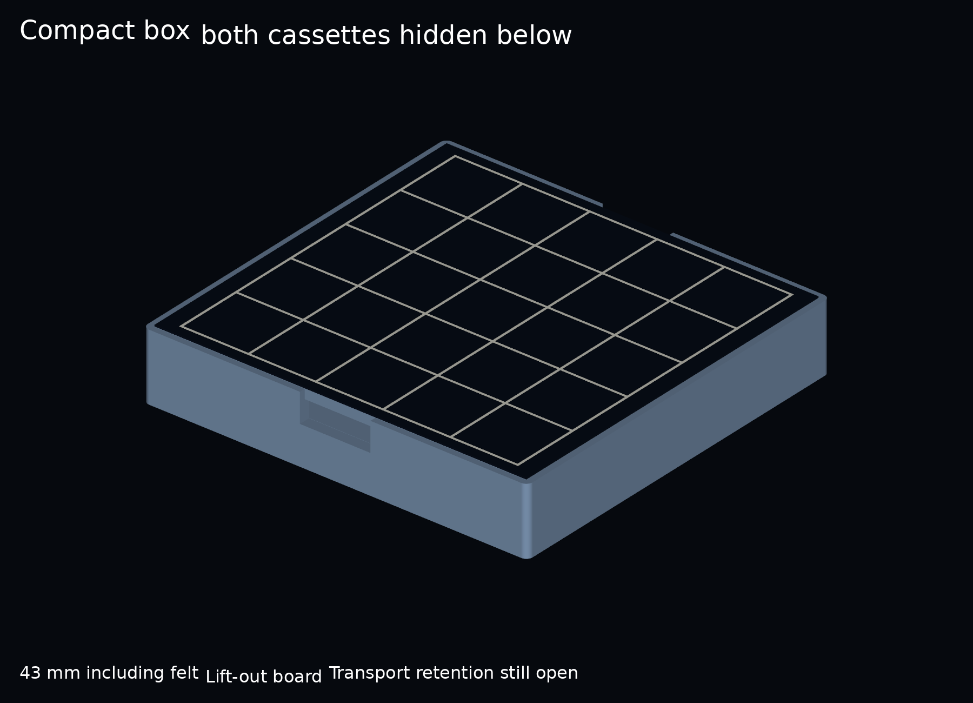
home-board-compact-v1/previews/02-packed.png
