Arcadesys/tak-box/pieces/fox-cat-capstones-v4/previews/cat-back.png

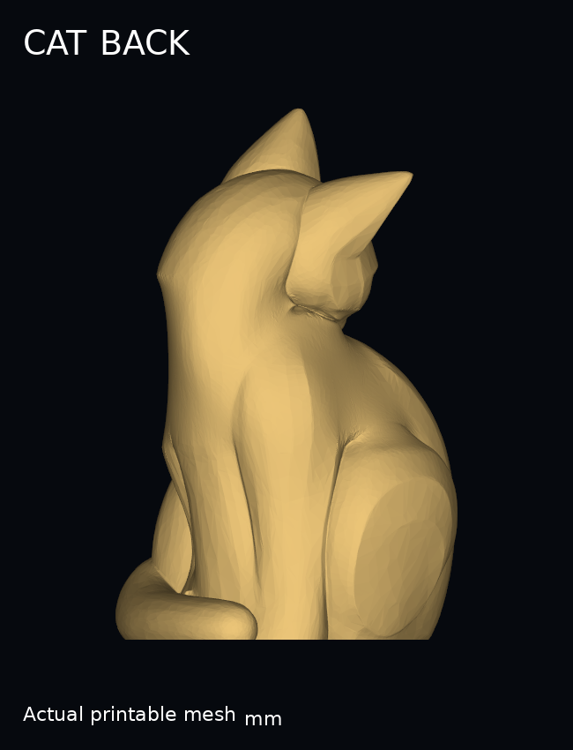
pieces/fox-cat-capstones-v4/previews/cat-back.png
