Arcadesys/tak-box/pieces/fox-cat-capstones-v4/previews/cat-front-before-after.png

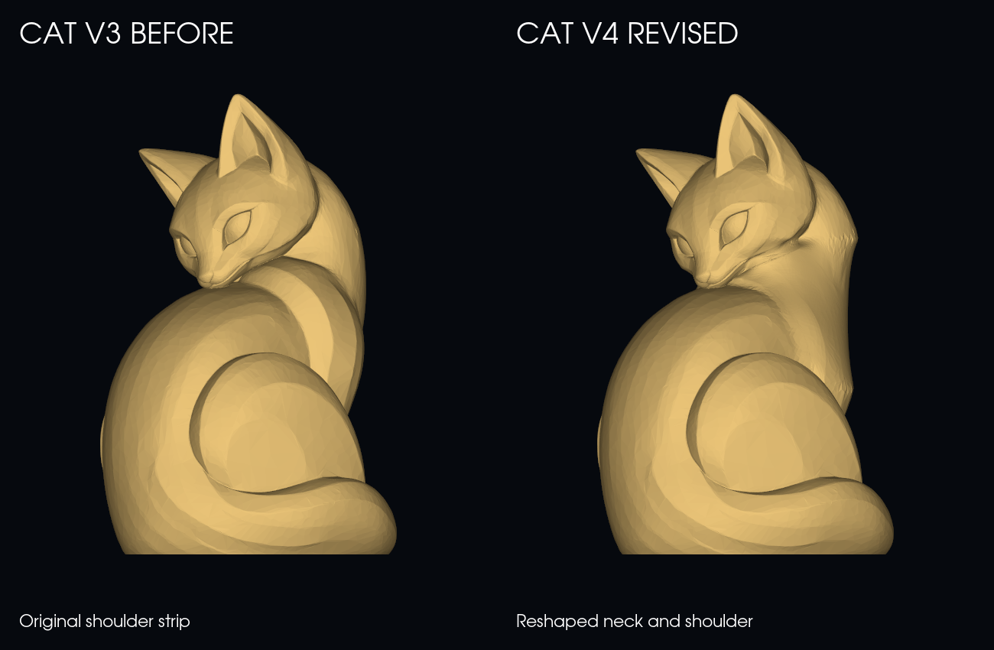
pieces/fox-cat-capstones-v4/previews/cat-front-before-after.png
