Arcadesys/tak-box/pieces/fox-cat-capstones-v4/previews/cat-front-side-back.png

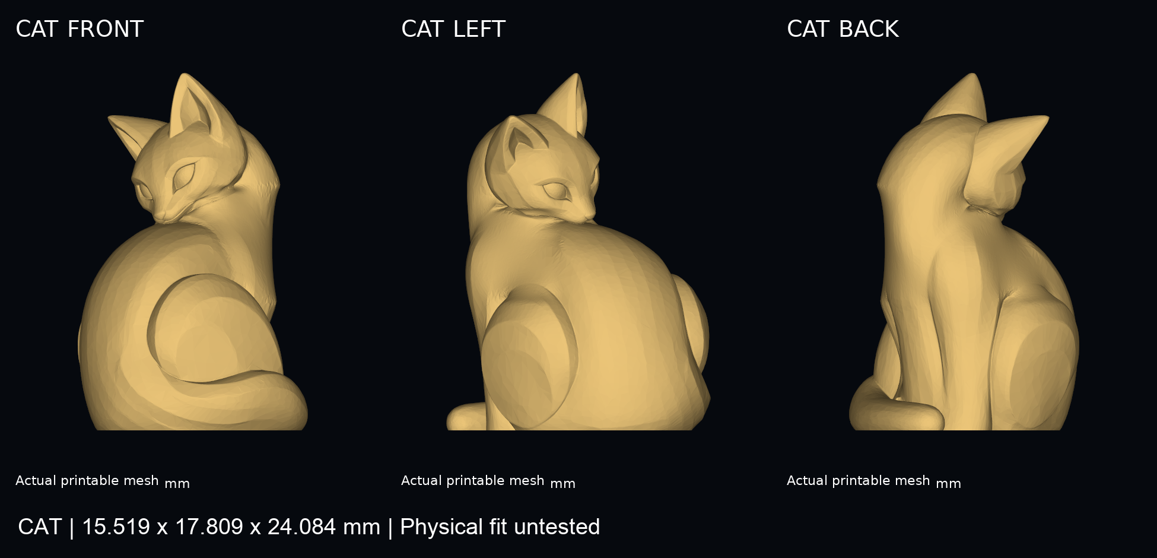
pieces/fox-cat-capstones-v4/previews/cat-front-side-back.png
