Arcadesys/tak-box/pieces/fox-cat-capstones-v4/previews/cat-front.png

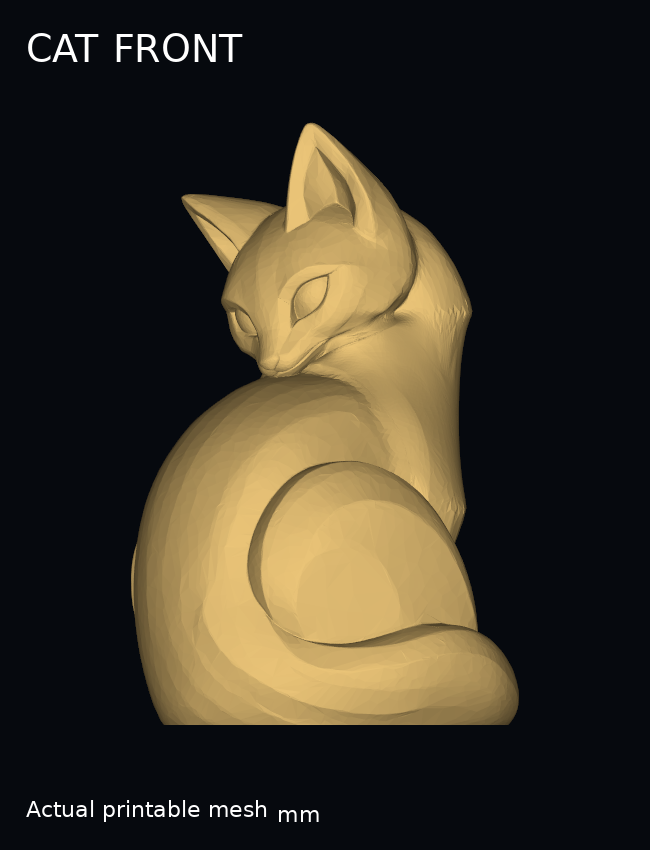
pieces/fox-cat-capstones-v4/previews/cat-front.png
