Arcadesys/tak-box/pieces/fox-cat-capstones-v4/previews/cat-left.png

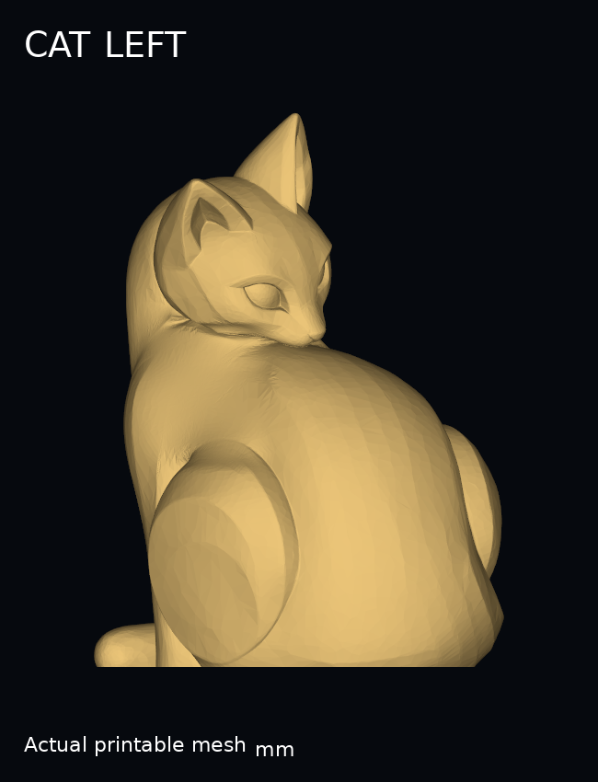
pieces/fox-cat-capstones-v4/previews/cat-left.png
