Arcadesys/tak-box/pieces/fox-cat-capstones-v4/previews/cat-right.png

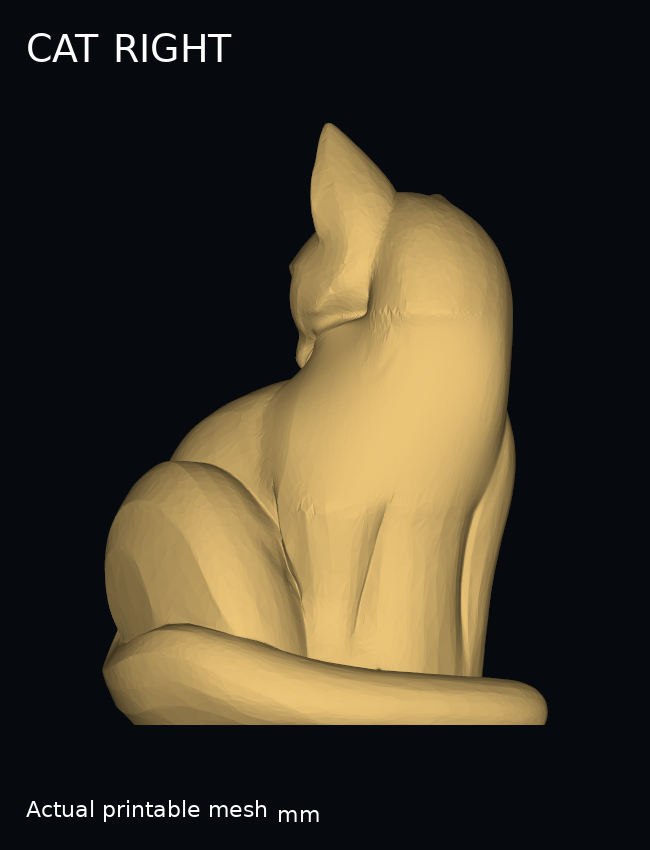
pieces/fox-cat-capstones-v4/previews/cat-right.png
