Arcadesys/tak-box/pieces/fox-cat-capstones-v4/previews/cat-three-quarter-before-after.png

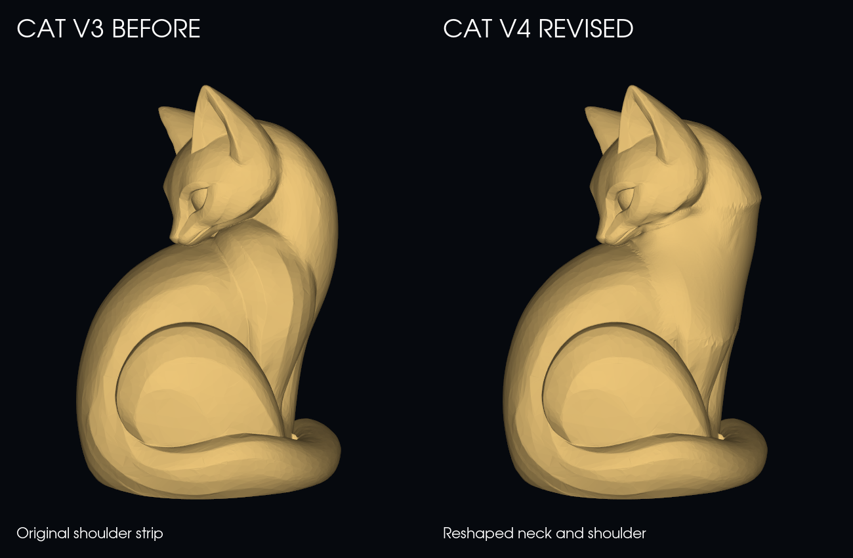
pieces/fox-cat-capstones-v4/previews/cat-three-quarter-before-after.png
