Arcadesys/tak-box/pieces/fox-cat-capstones-v4/previews/cat-v16-storage.png

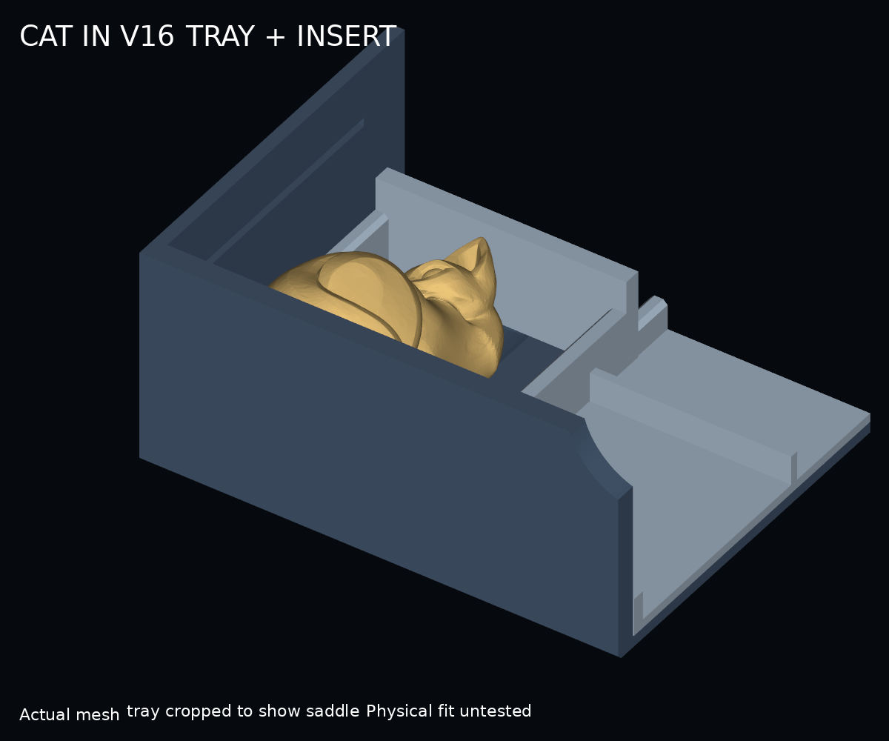
pieces/fox-cat-capstones-v4/previews/cat-v16-storage.png
