Arcadesys/tak-box/pieces/fox-cat-capstones-v4/previews/fox-back.png

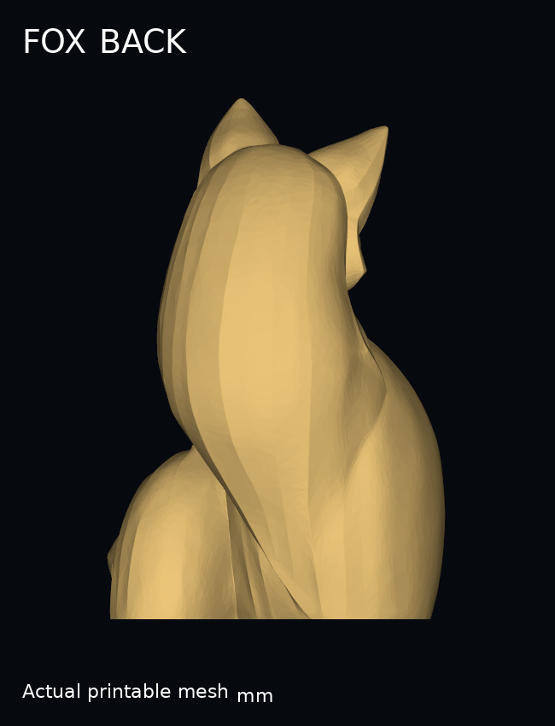
pieces/fox-cat-capstones-v4/previews/fox-back.png
