Arcadesys/tak-box/pieces/fox-cat-capstones-v4/previews/fox-front.png

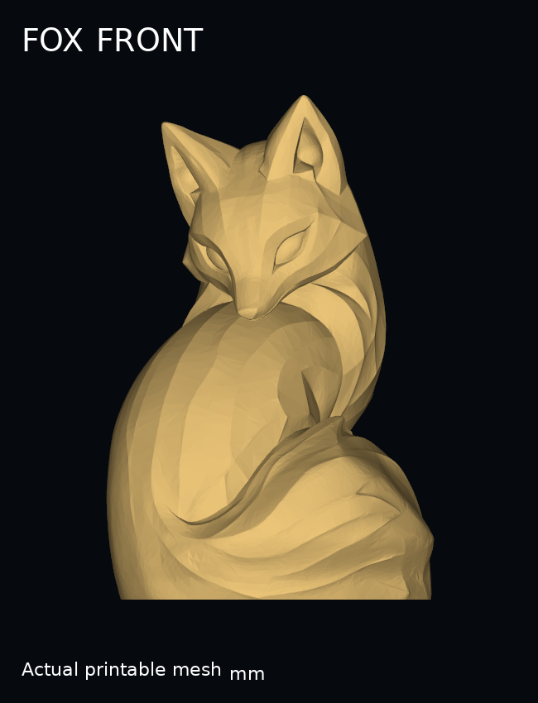
pieces/fox-cat-capstones-v4/previews/fox-front.png
