Arcadesys/tak-box/pieces/fox-cat-capstones-v4/previews/fox-left.png

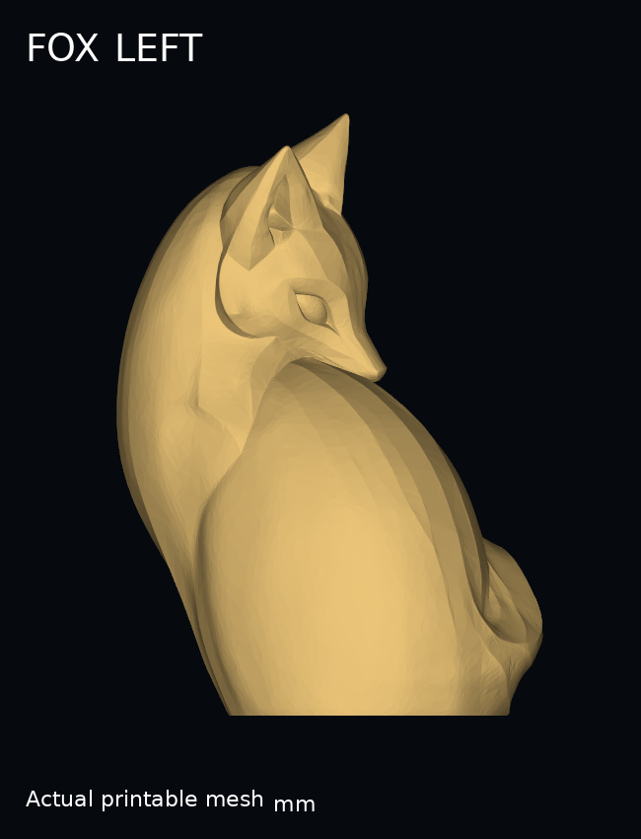
pieces/fox-cat-capstones-v4/previews/fox-left.png
