Arcadesys/tak-box/pieces/fox-cat-capstones-v4/previews/fox-right.png

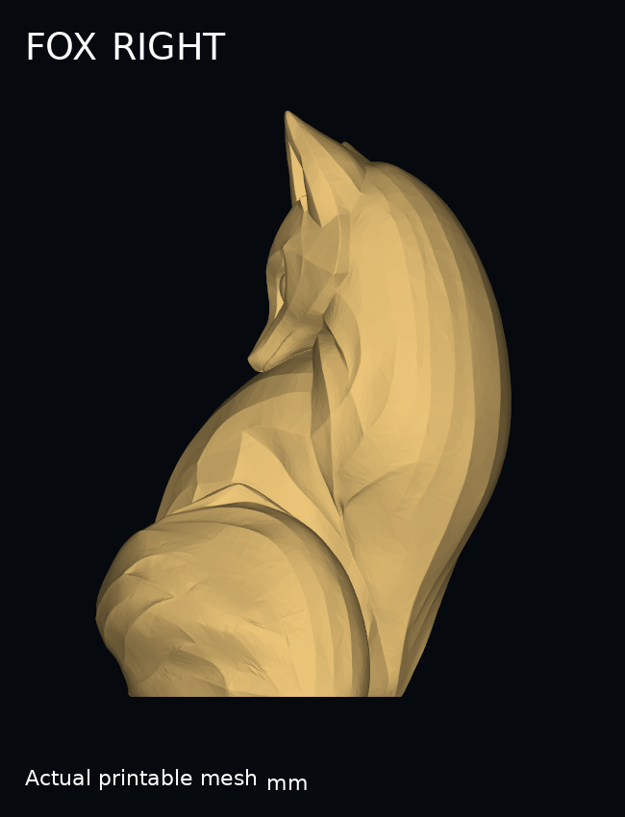
pieces/fox-cat-capstones-v4/previews/fox-right.png
