Arcadesys/tak-box/pieces/fox-cat-capstones-v4/previews/fox-three-quarter.png

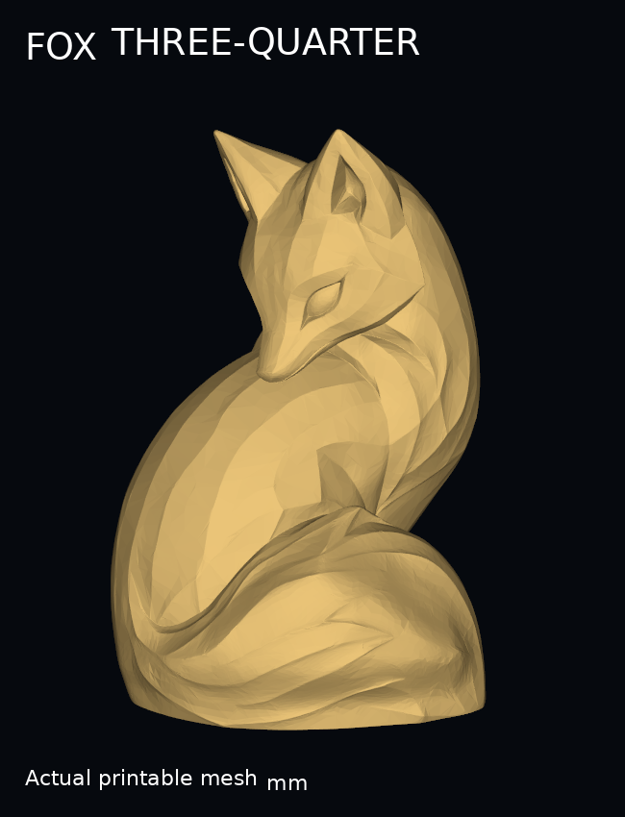
pieces/fox-cat-capstones-v4/previews/fox-three-quarter.png
