Arcadesys/tak-box/pieces/fox-cat-capstones-v4/references/cat-hero.png

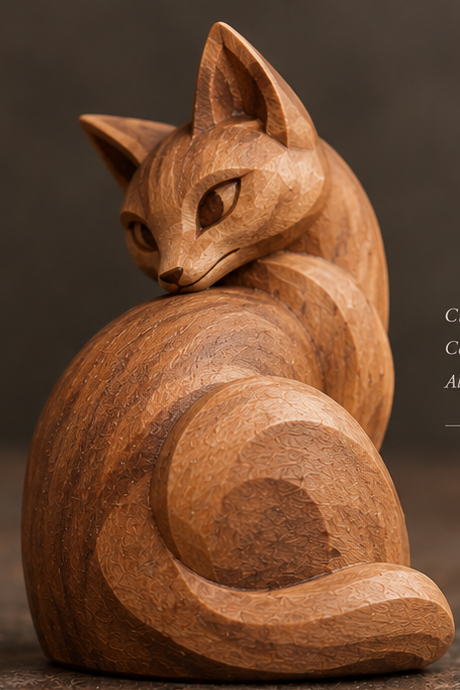
pieces/fox-cat-capstones-v4/references/cat-hero.png
