Arcadesys/tak-box/pieces/fox-cat-capstones-v4/references/fox-hero.png

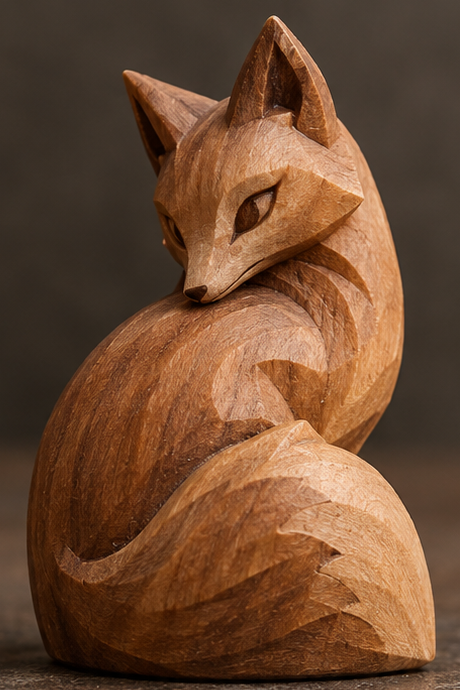
pieces/fox-cat-capstones-v4/references/fox-hero.png
