Arcadesys/tak-box/pieces/team-pieces-preview.png

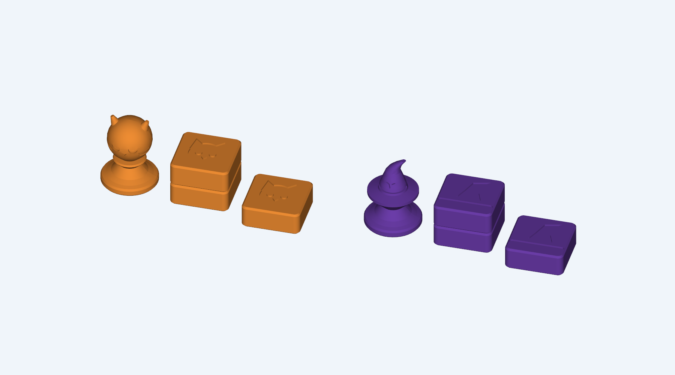
pieces/team-pieces-preview.png
