Arcadesys/tak-box/pieces/team-pieces-top.png

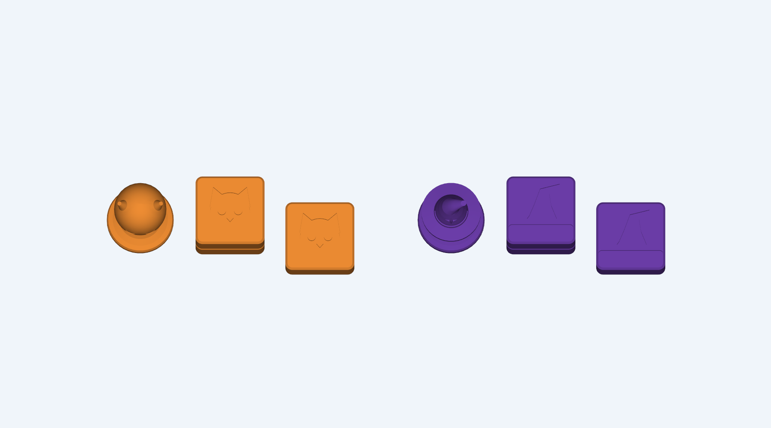
pieces/team-pieces-top.png
