Arcadesys/tak-box/v16-field-book/previews/04-half-open.png

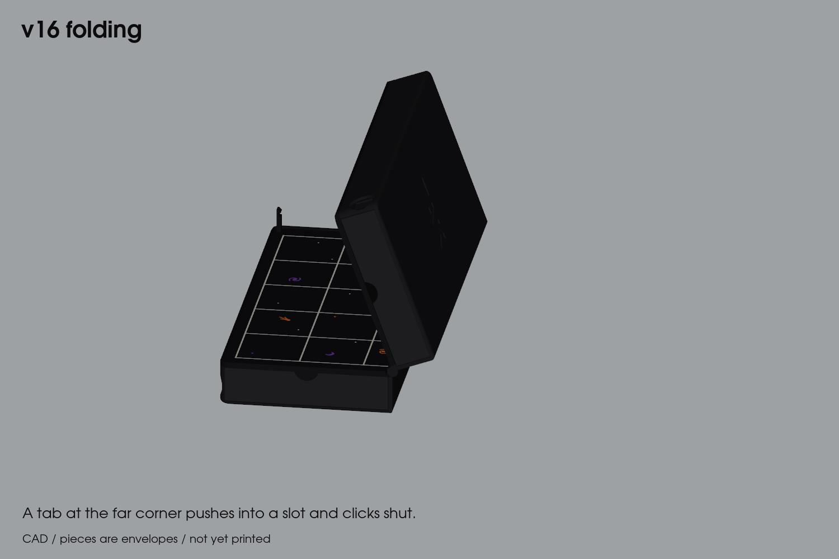
v16-field-book/previews/04-half-open.png
