Arcadesys/tak-box/v16-field-book/previews/08-tray-insert.png

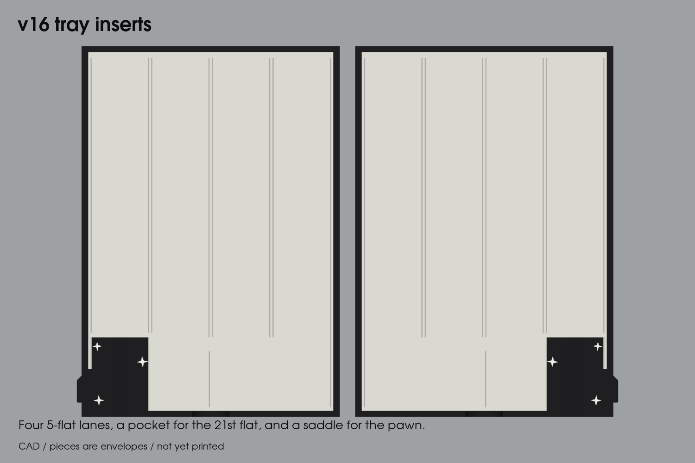
v16-field-book/previews/08-tray-insert.png
