Arcadesys/tak-box/v17-four-leaf/previews/01-open.png

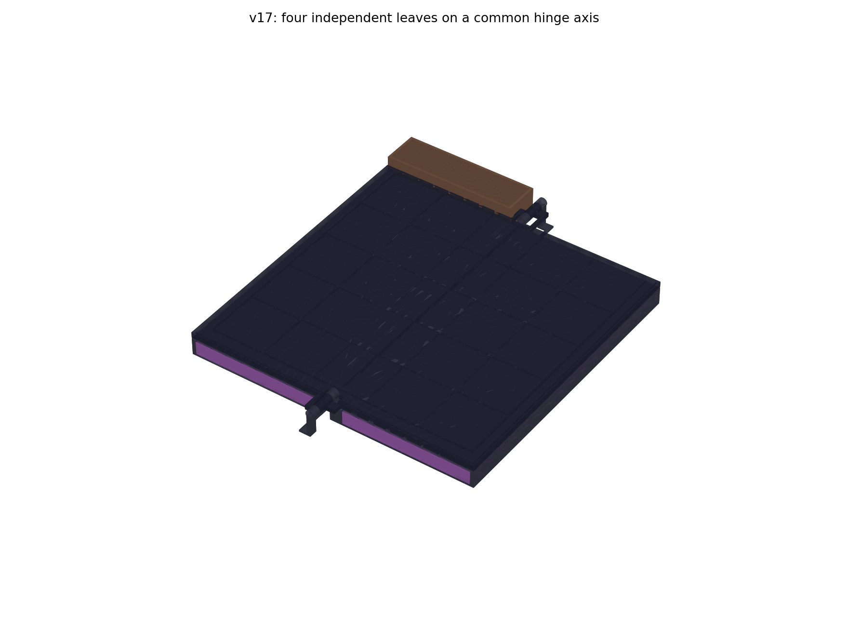
v17-four-leaf/previews/01-open.png
