Arcadesys/tak-box/v17-four-leaf/previews/02-closed.png

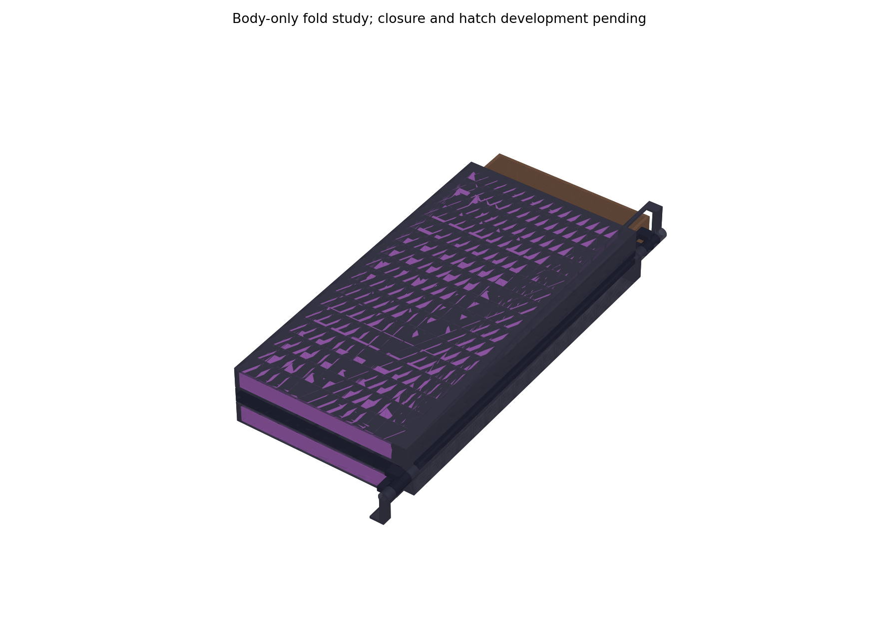
v17-four-leaf/previews/02-closed.png
