Arcadesys/tak-box/v17-four-leaf/previews/03-drawer-access.png

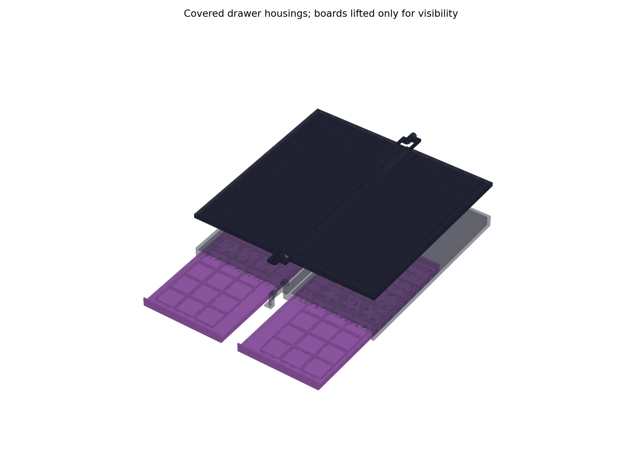
v17-four-leaf/previews/03-drawer-access.png
