Arcadesys/tak-box/v17-four-leaf/previews/04-closure-trial.png

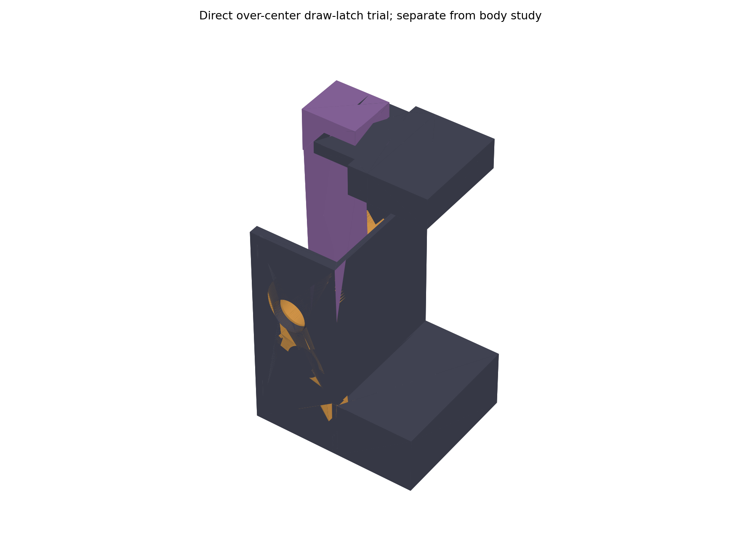
v17-four-leaf/previews/04-closure-trial.png
