Arcadesys/tak-box/v18-case/previews/01-left-housing-hook-pivot-and-cap-compartment-layers.png

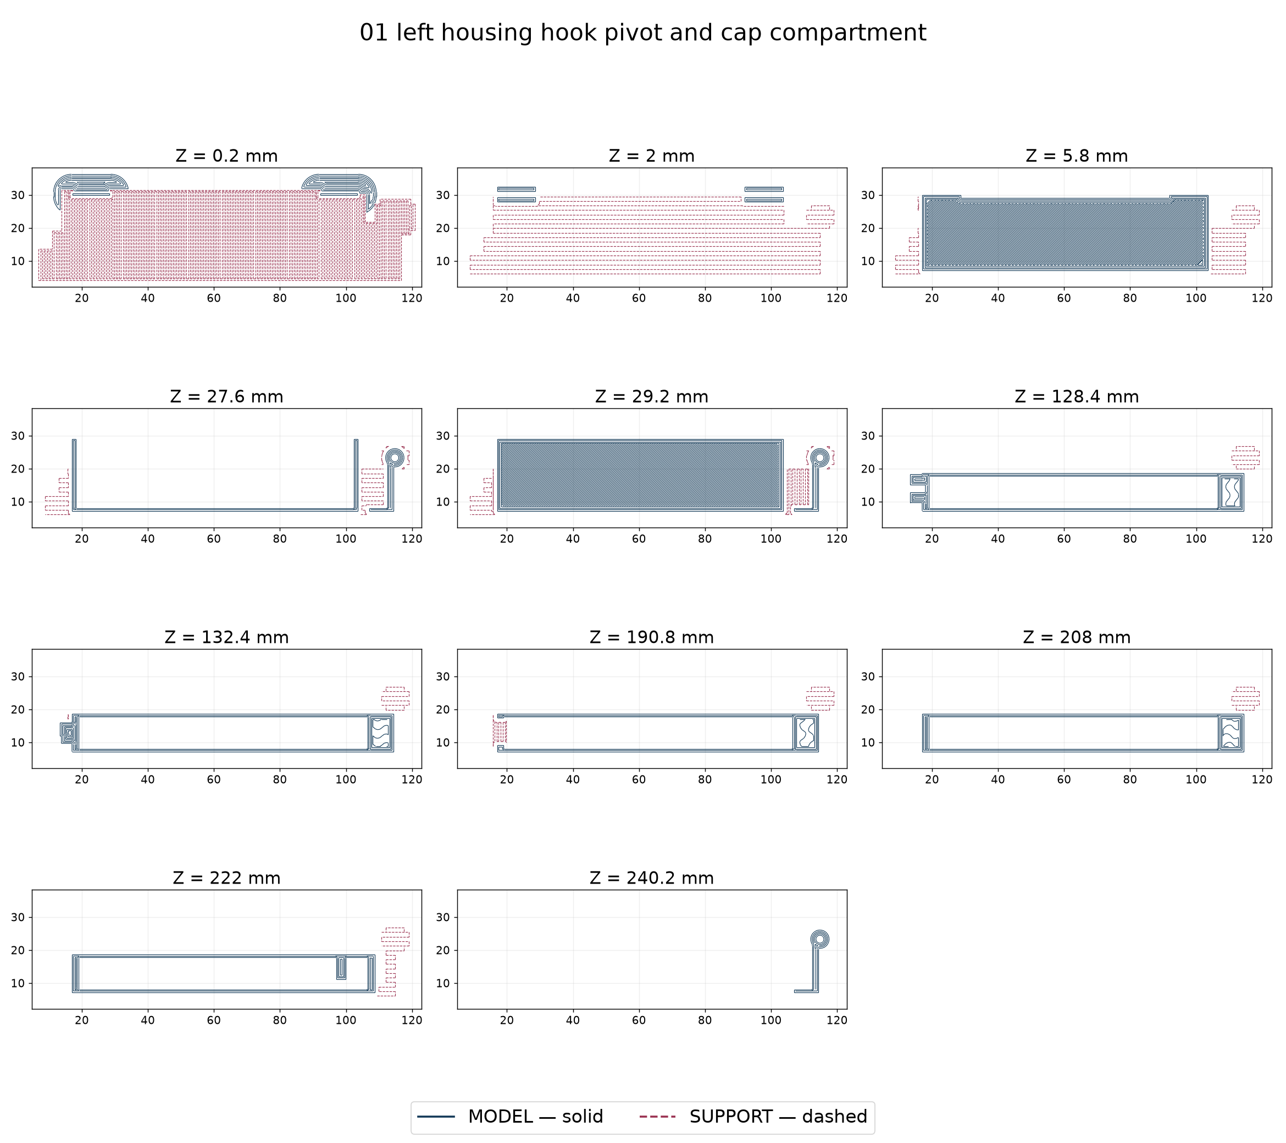
v18-case/previews/01-left-housing-hook-pivot-and-cap-compartment-layers.png
