Arcadesys/tak-box/v18-case/previews/02-right-housing-and-hook-pin-layers.png

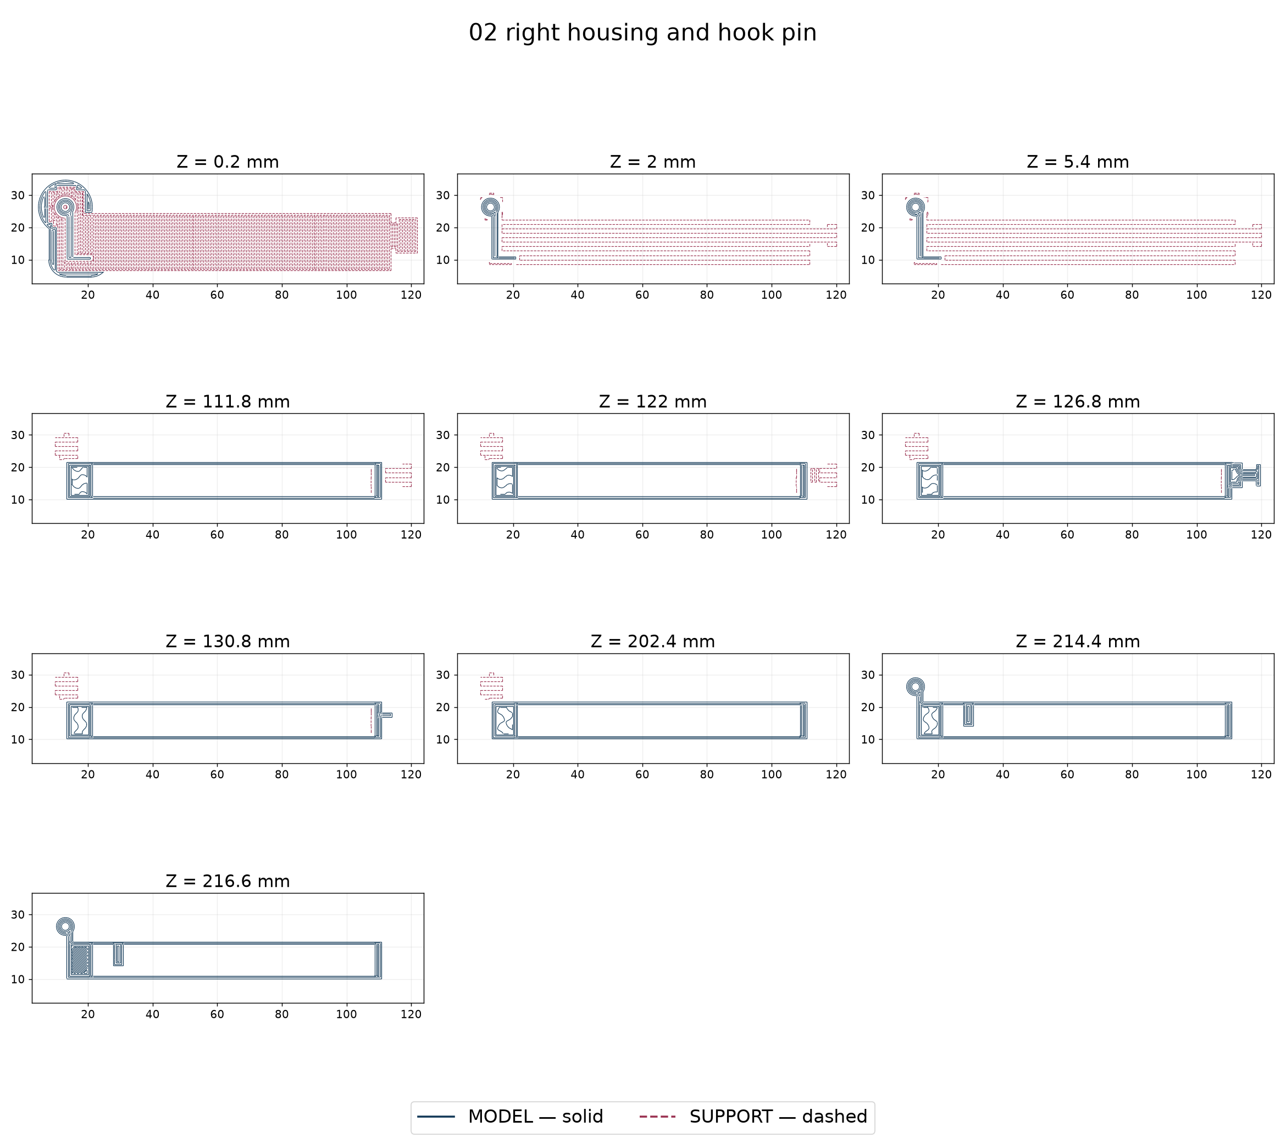
v18-case/previews/02-right-housing-and-hook-pin-layers.png
