Arcadesys/tak-box/v18-case/previews/03-access.png

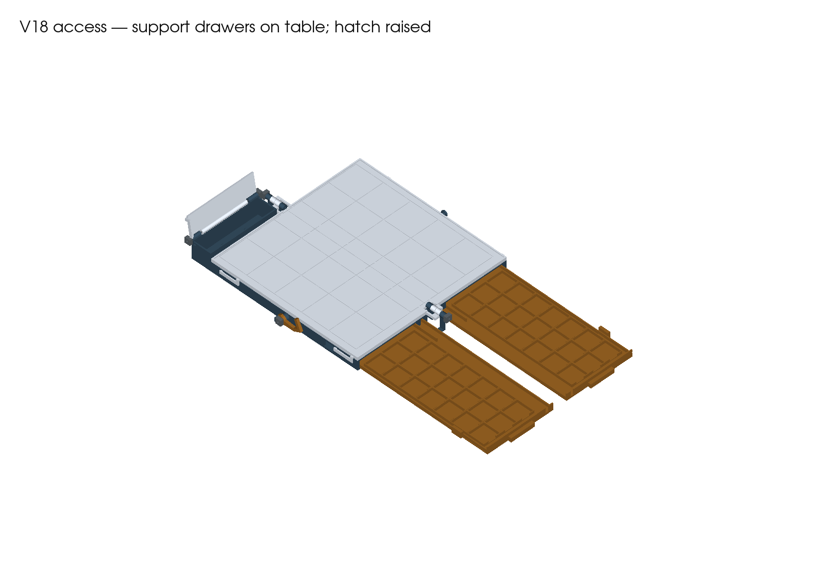
v18-case/previews/03-access.png
