Arcadesys/tak-box/v18-case/previews/03-board-leaves-layers.png

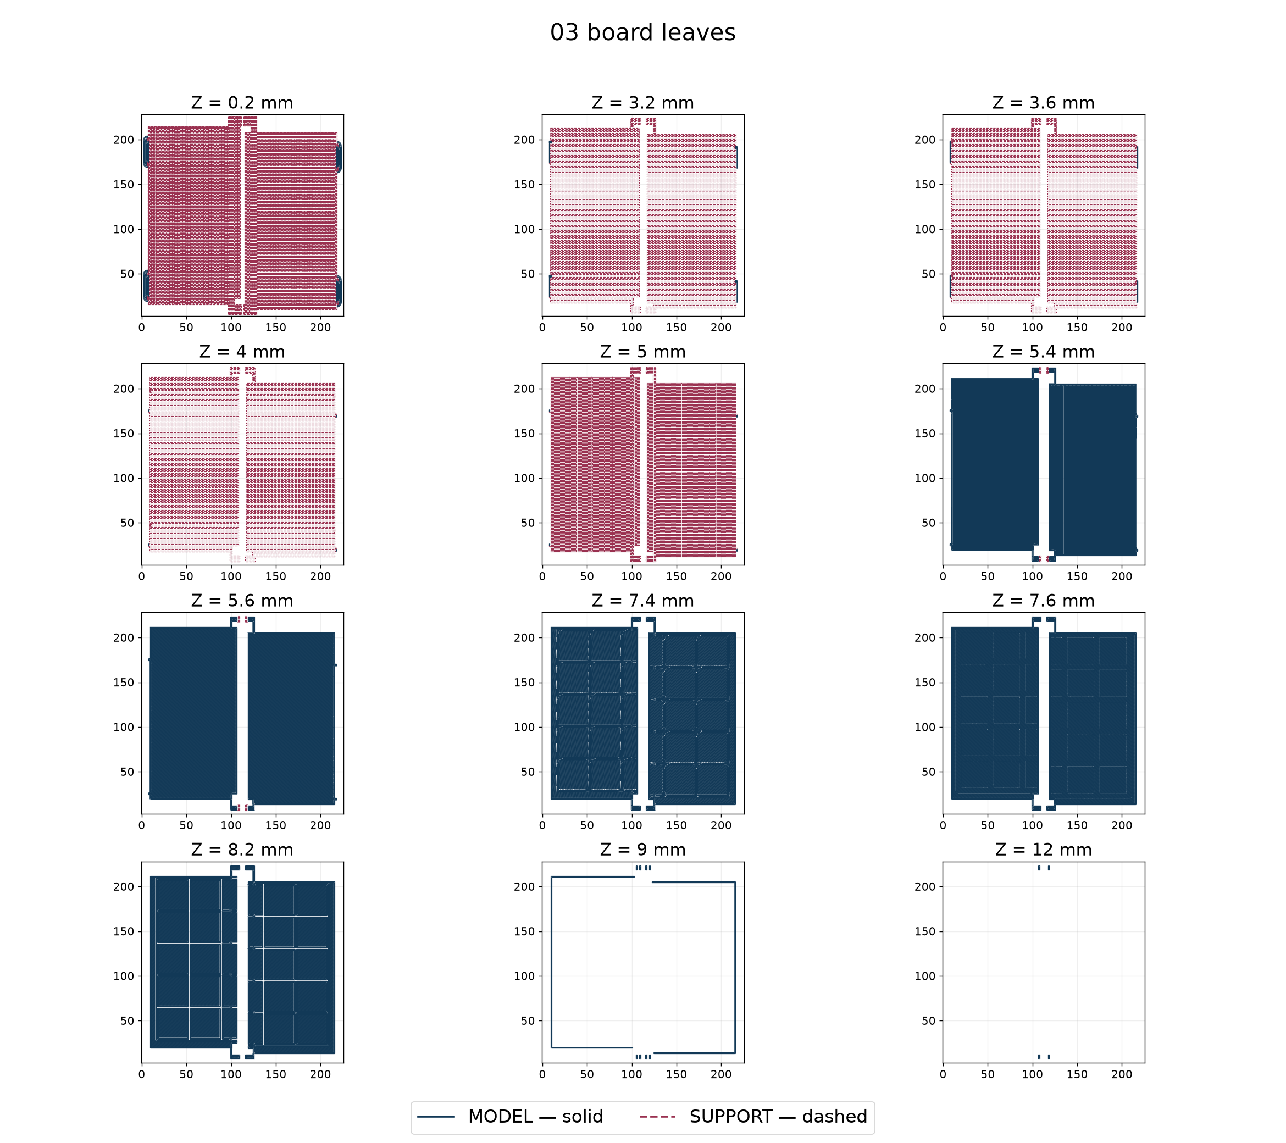
v18-case/previews/03-board-leaves-layers.png
