Arcadesys/tak-box/v18-case/previews/04-piece-drawers-layers.png

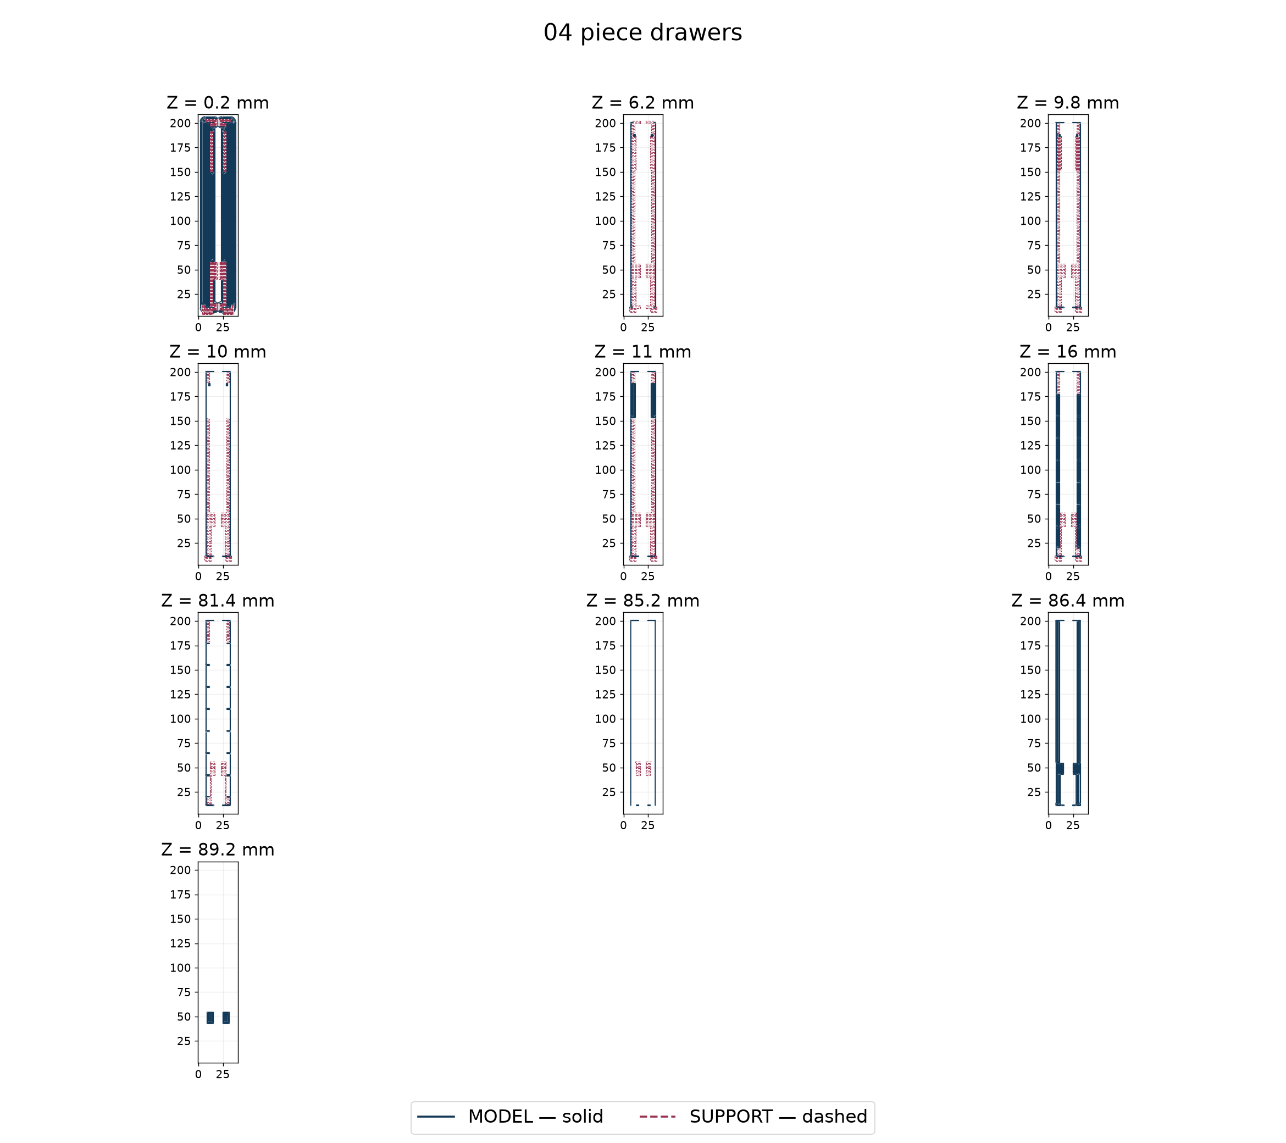
v18-case/previews/04-piece-drawers-layers.png
