Arcadesys/tak-box/v18-case/previews/05-hatch-hook-and-five-axle-caps-layers.png

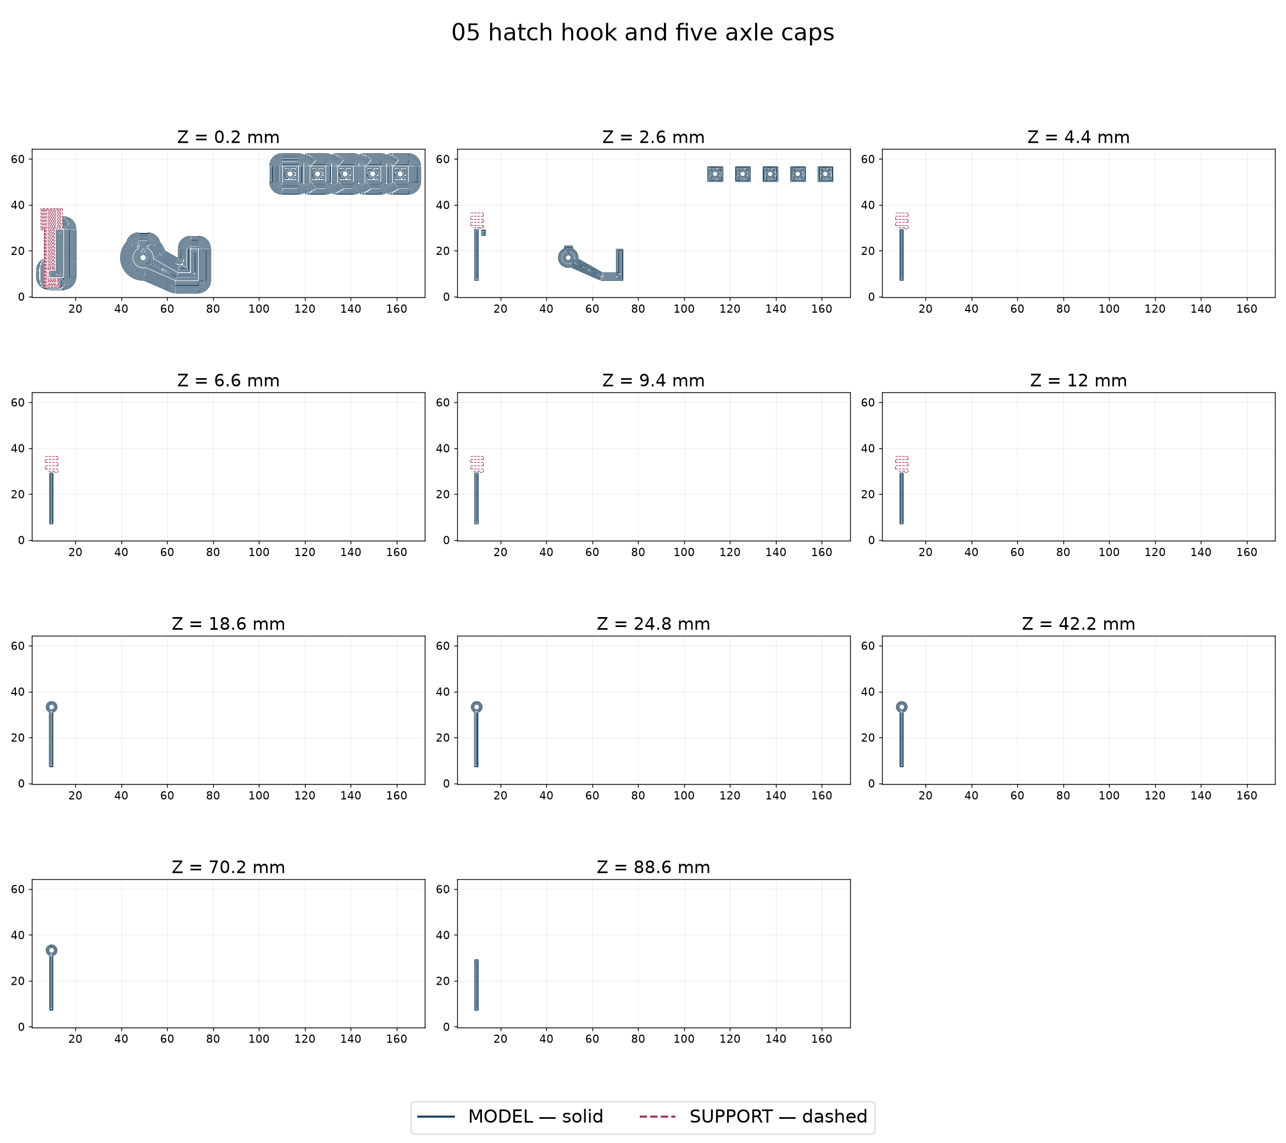
v18-case/previews/05-hatch-hook-and-five-axle-caps-layers.png
