Arcadesys/tak-box/v18-case/previews/06-pin-passages-1.png

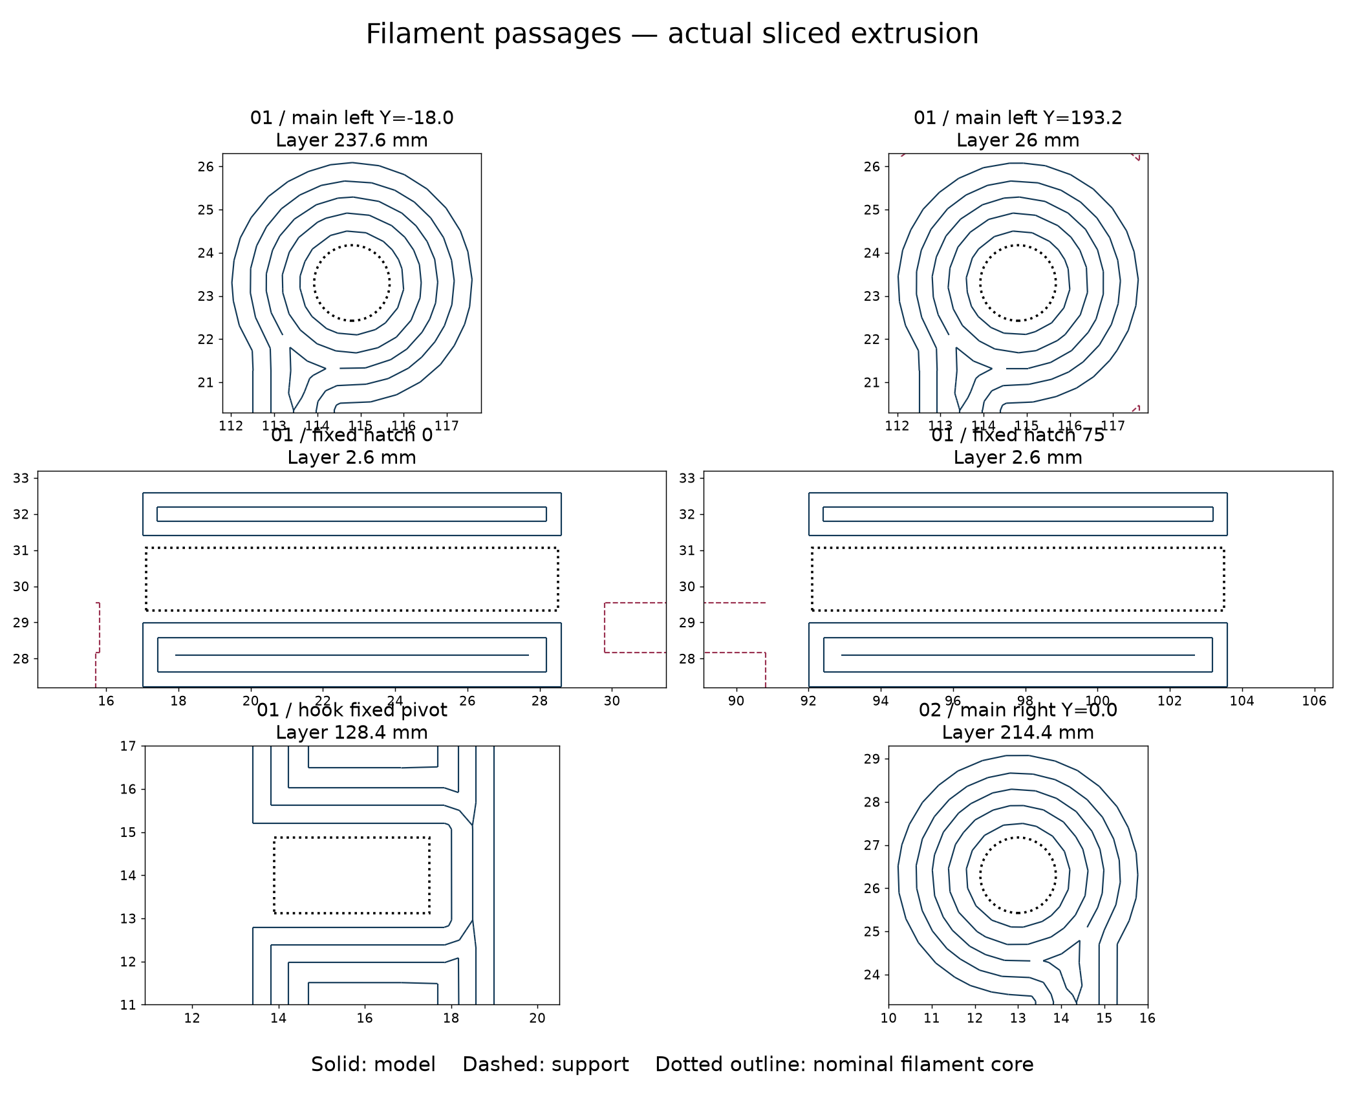
v18-case/previews/06-pin-passages-1.png
