Arcadesys/tak-box/v18-case/previews/06-pin-passages-2.png

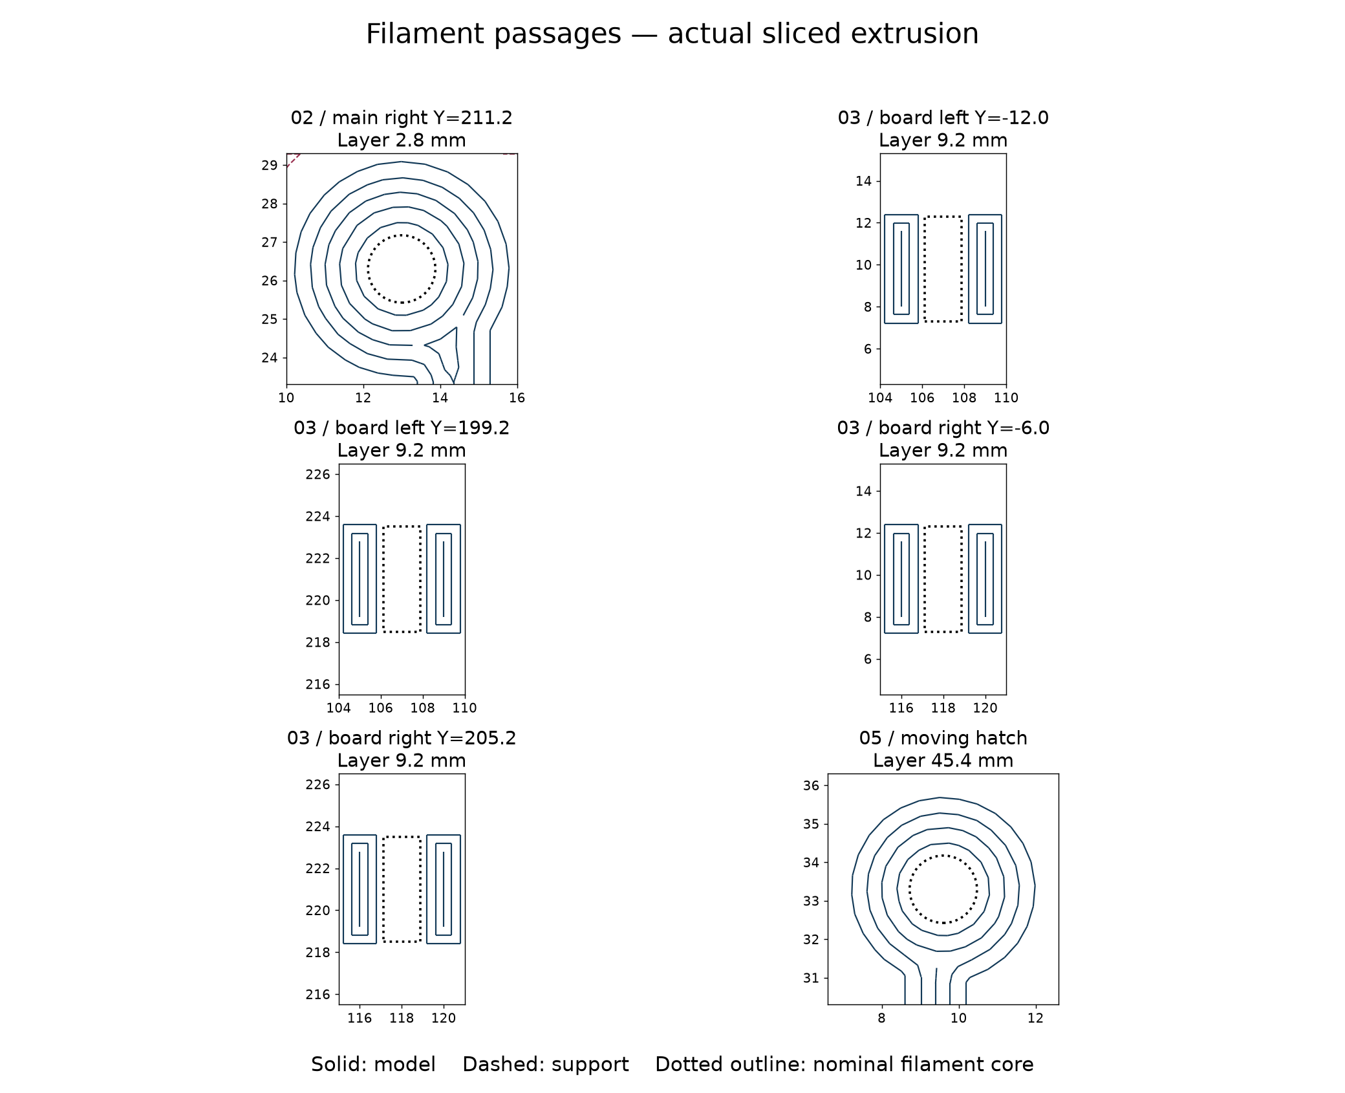
v18-case/previews/06-pin-passages-2.png
