Arcadesys/tak-box/v18-recessed-clasp/renders/1-cutaway.png

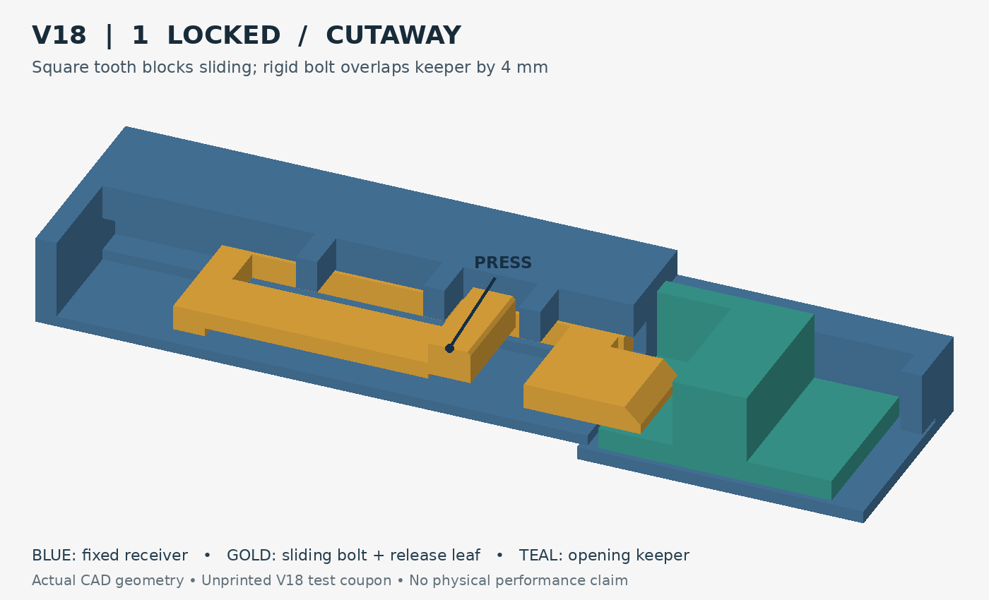
v18-recessed-clasp/renders/1-cutaway.png
