Arcadesys/tak-box/v18-recessed-clasp/renders/2-cutaway.png

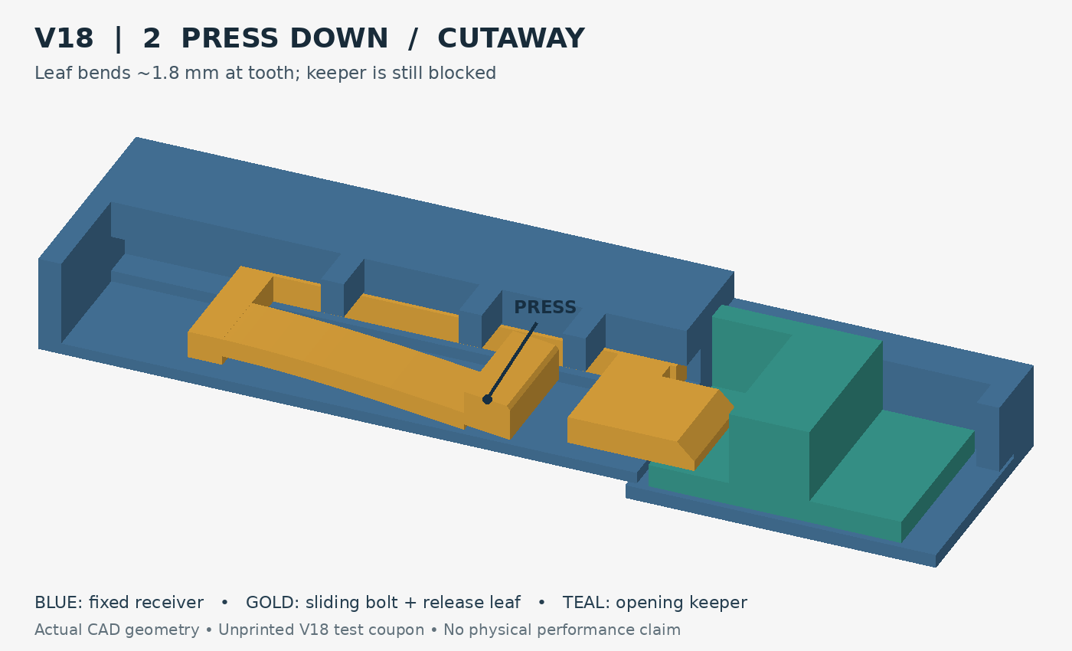
v18-recessed-clasp/renders/2-cutaway.png
