Arcadesys/tak-box/v18-recessed-clasp/renders/3-cutaway.png

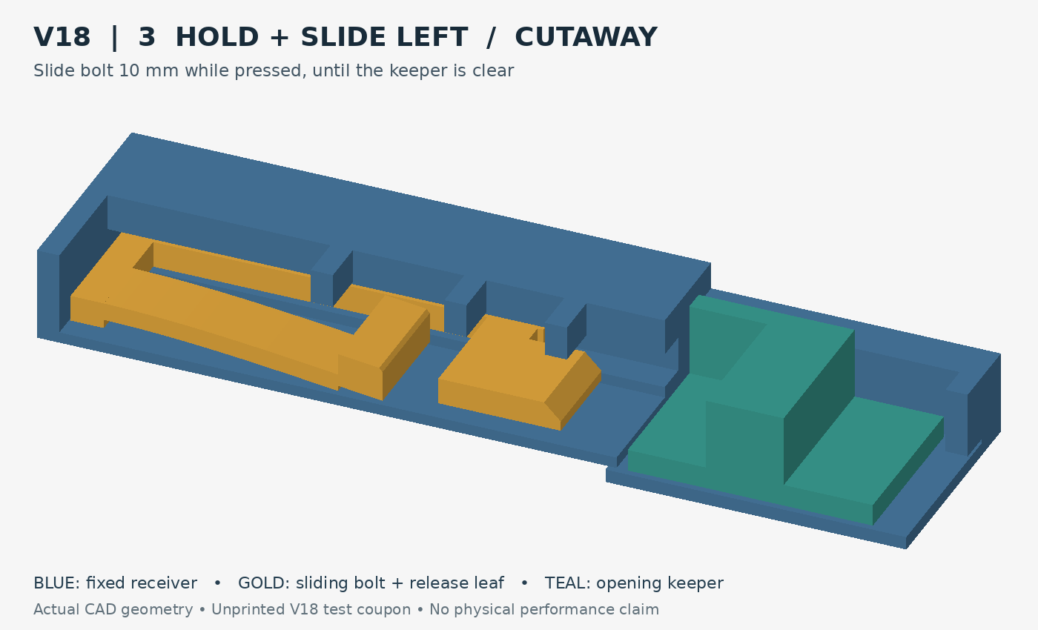
v18-recessed-clasp/renders/3-cutaway.png
