Arcadesys/tak-box/v18-recessed-clasp/renders/4-cutaway.png

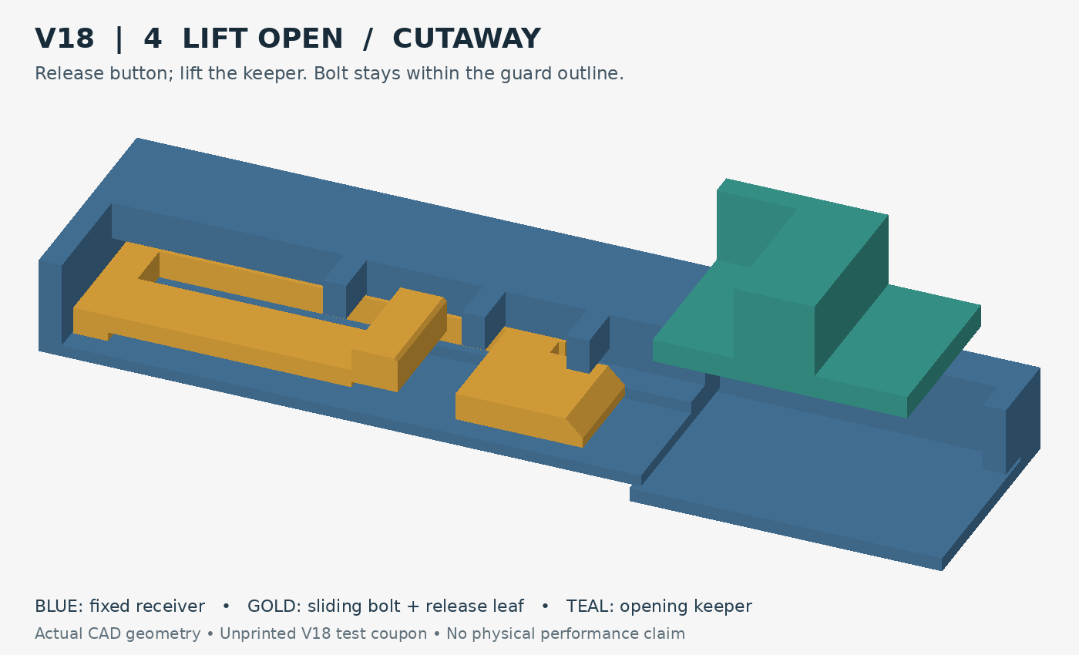
v18-recessed-clasp/renders/4-cutaway.png
