Arcadesys/tak-box/v18-recessed-clasp/renders/V18-release-sequence.png

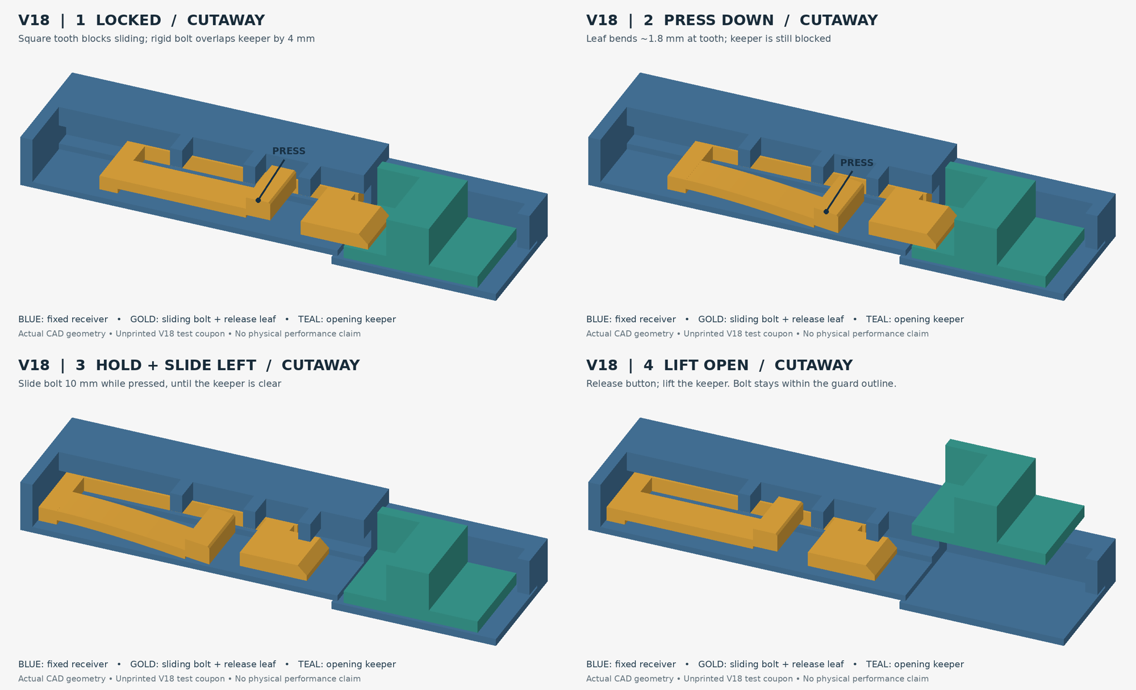
v18-recessed-clasp/renders/V18-release-sequence.png
