Arcadesys/tak-box/v18-recessed-clasp/slicing/layer-inspection.png

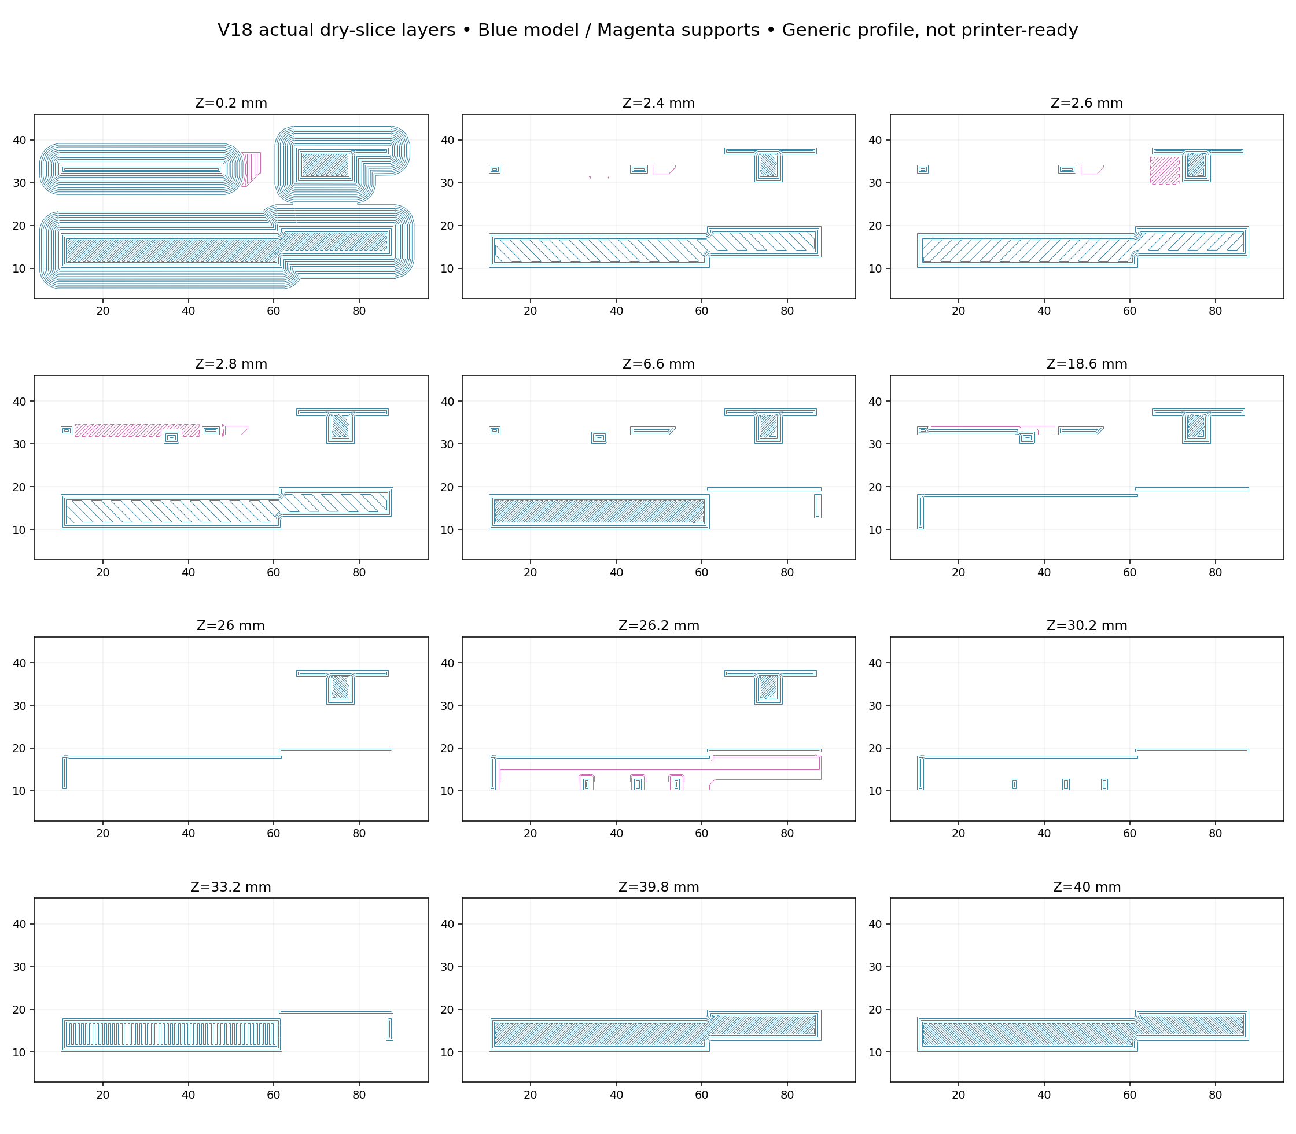
v18-recessed-clasp/slicing/layer-inspection.png
