Arcadesys/tak-box/v23-r2/FIT-CHECK/layers.png

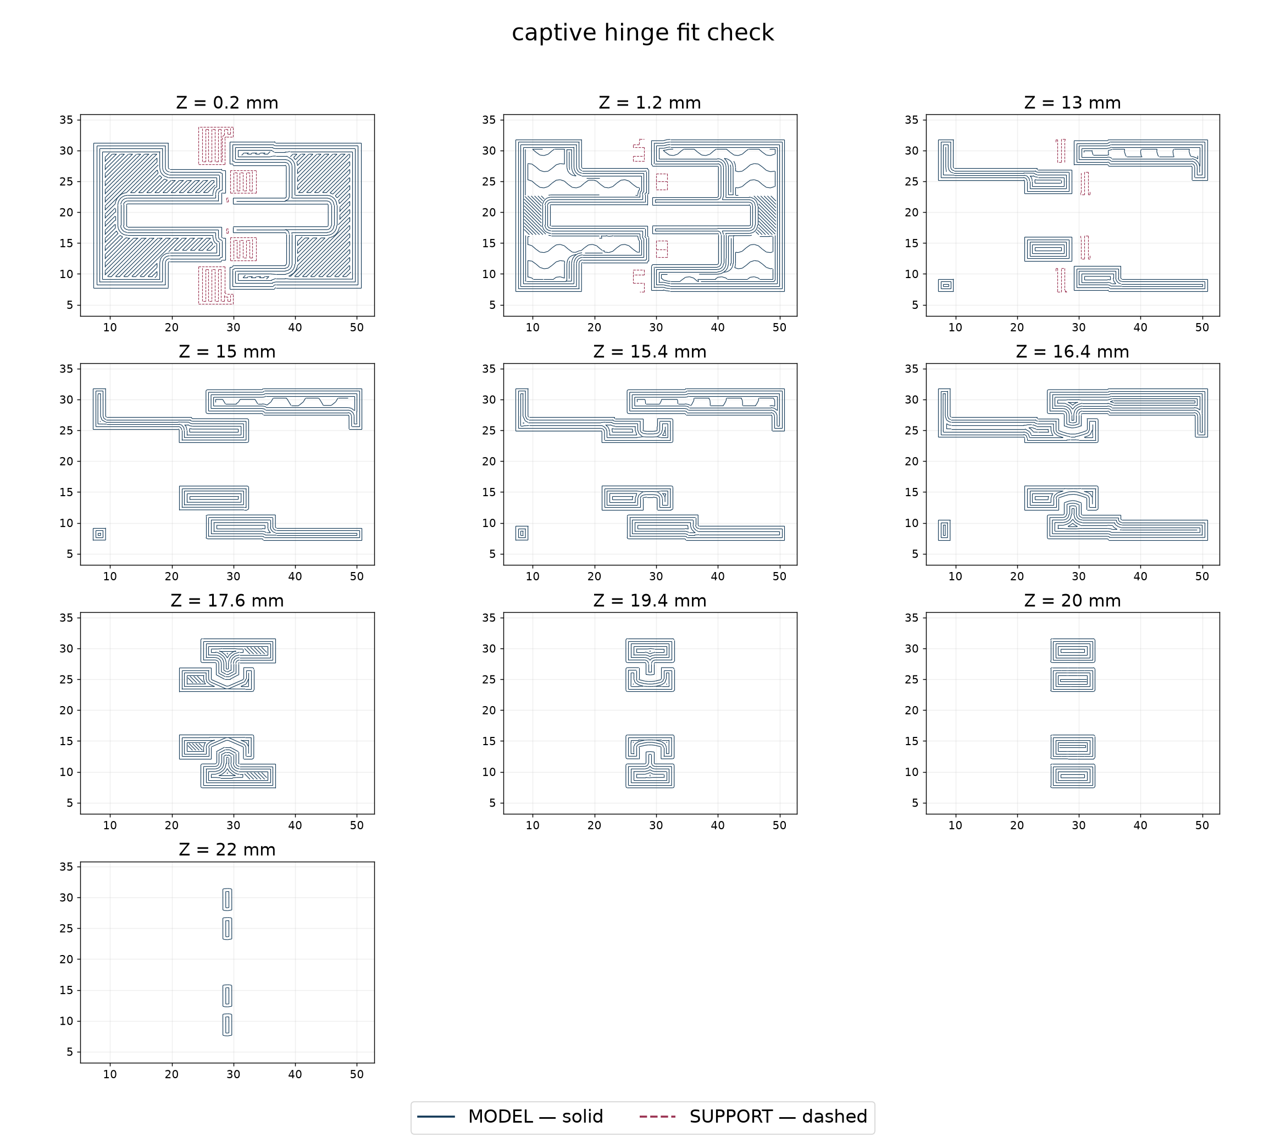
v23-r2/FIT-CHECK/layers.png
