Arcadesys/tak-box/v23-r2/previews/01-open.png

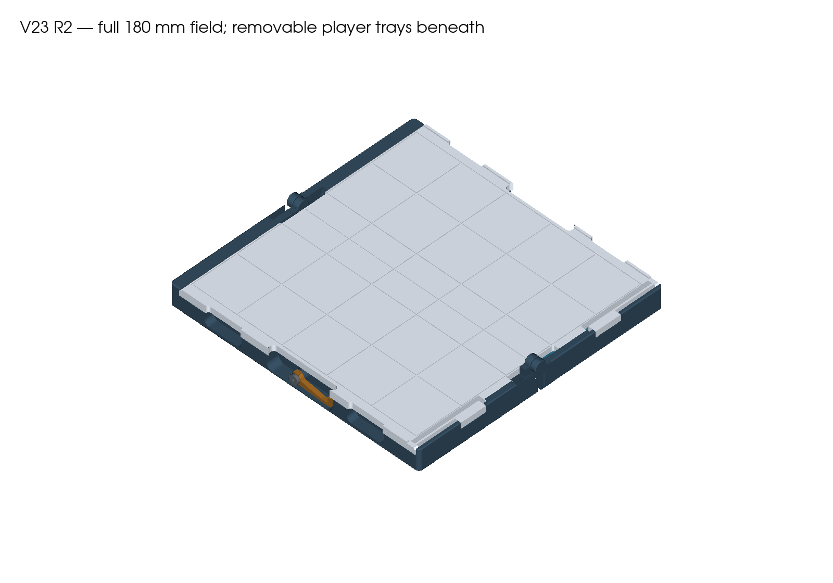
v23-r2/previews/01-open.png
