Arcadesys/tak-box/v23-r2/previews/02-sliding-board-tops-layers.png

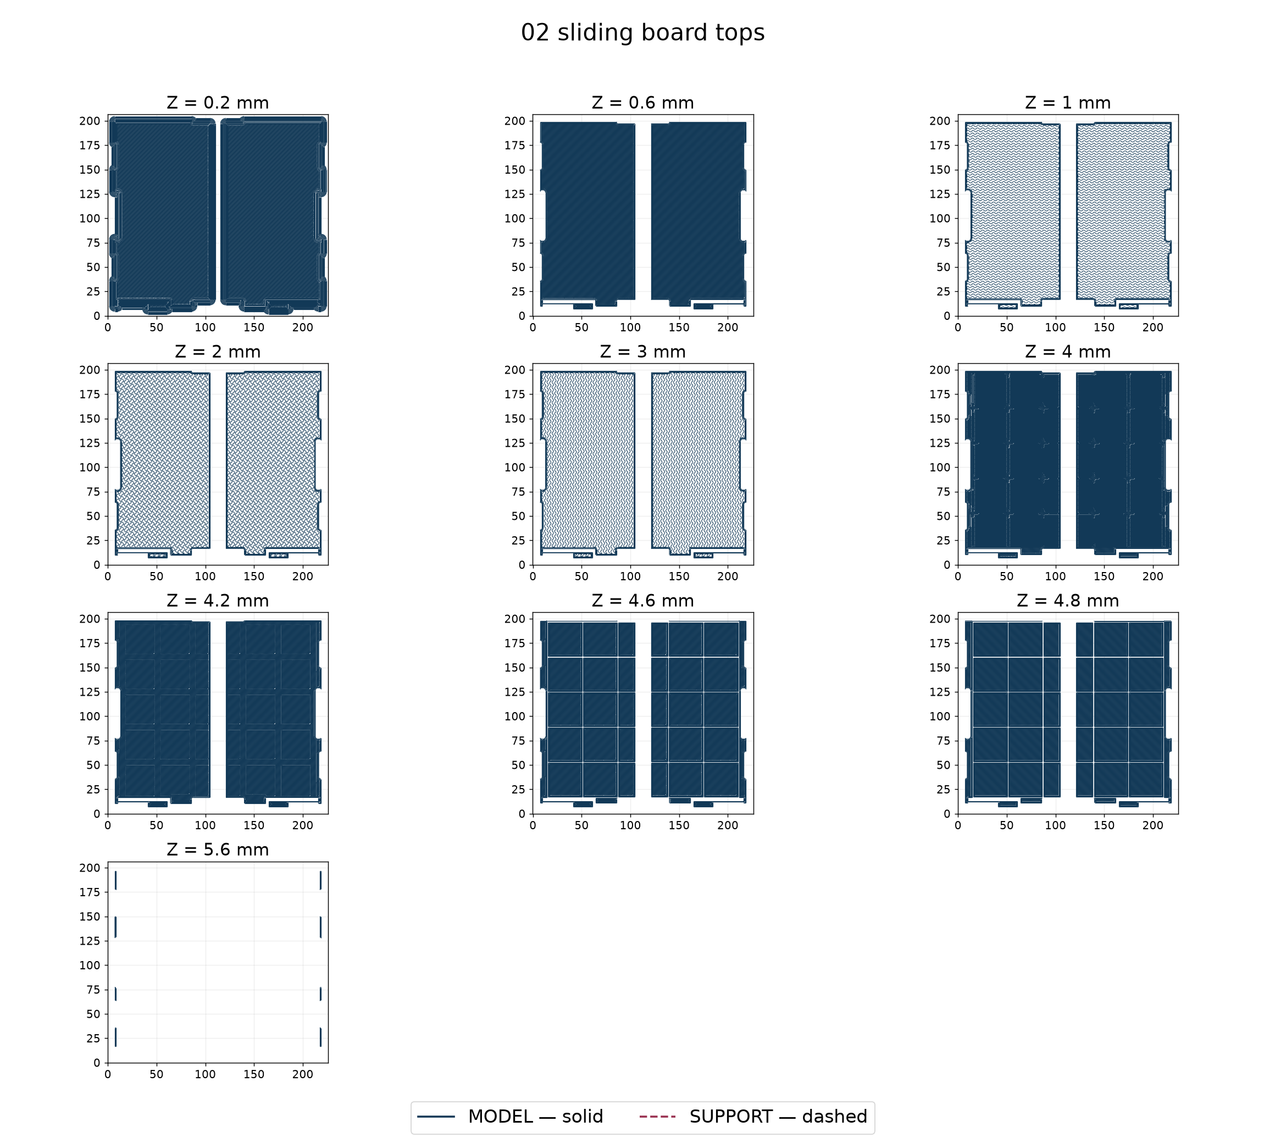
v23-r2/previews/02-sliding-board-tops-layers.png
