Arcadesys/tak-box/v23-r2/previews/03-removable-player-trays-layers.png

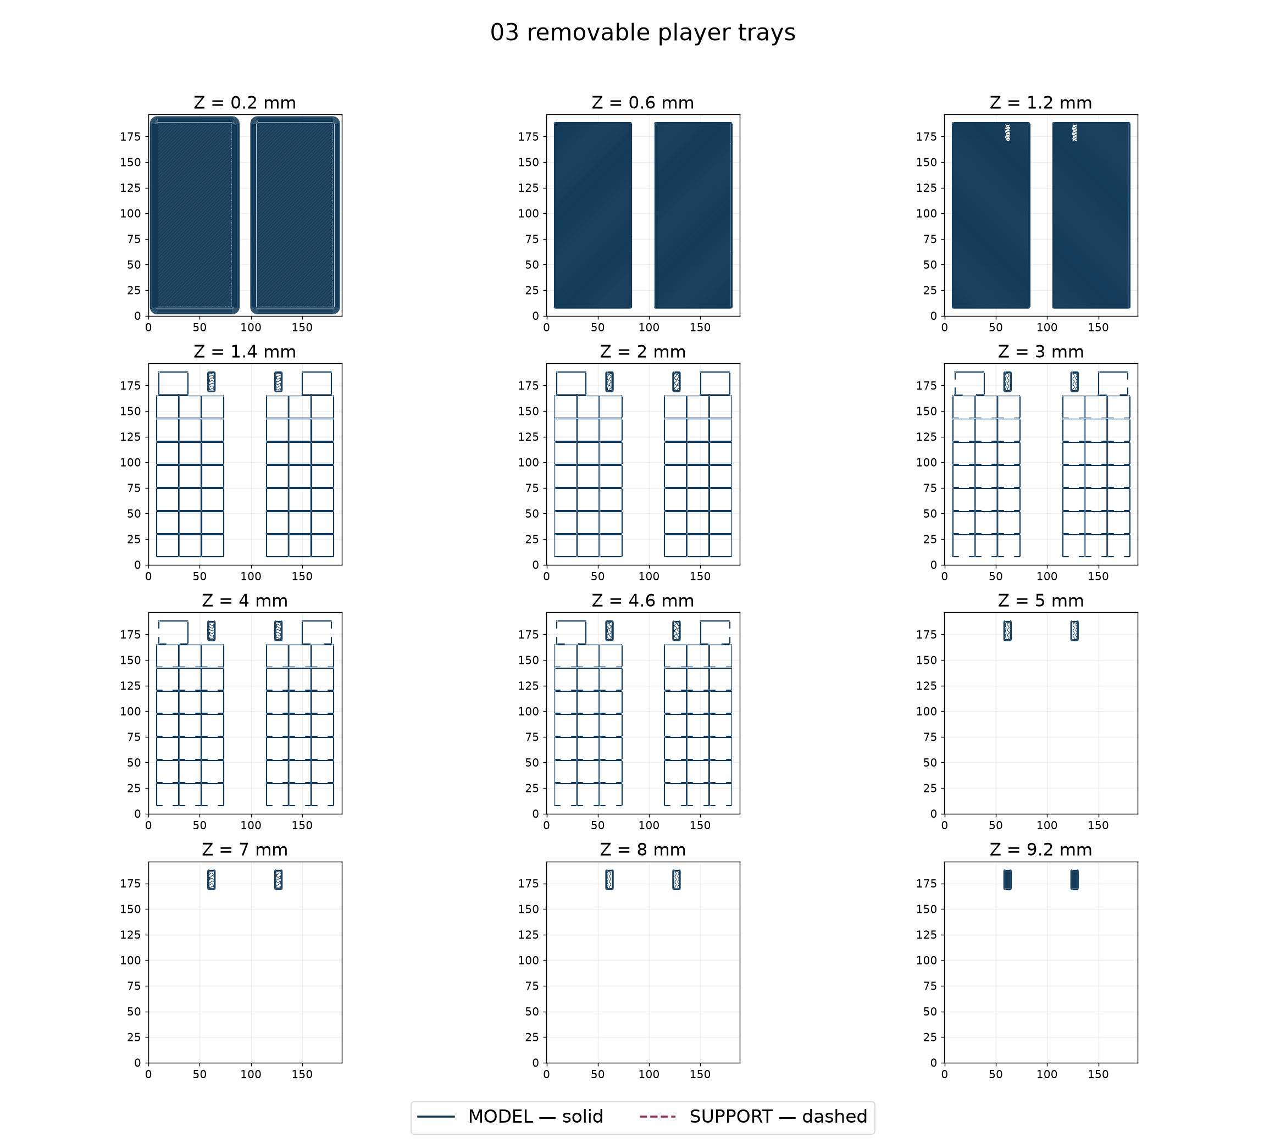
v23-r2/previews/03-removable-player-trays-layers.png
