Arcadesys/tak-box/v23-r2/previews/04-flat-capstones-hook-and-collar-layers.png

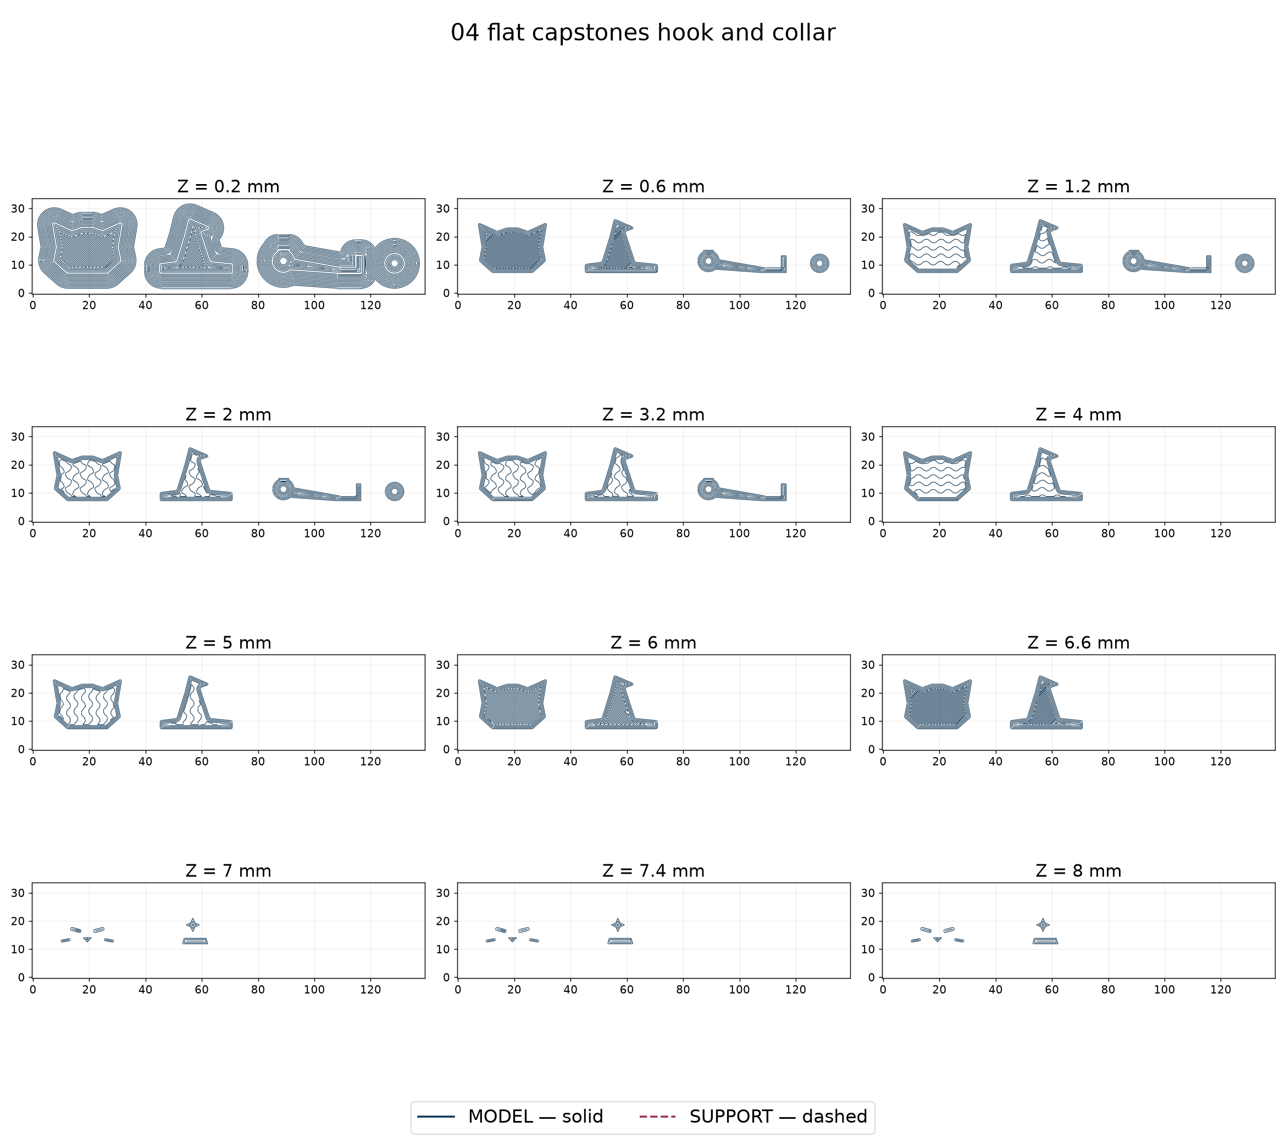
v23-r2/previews/04-flat-capstones-hook-and-collar-layers.png
