Arcadesys/tak-box/v23-r2/previews/04-loaded-storage.png

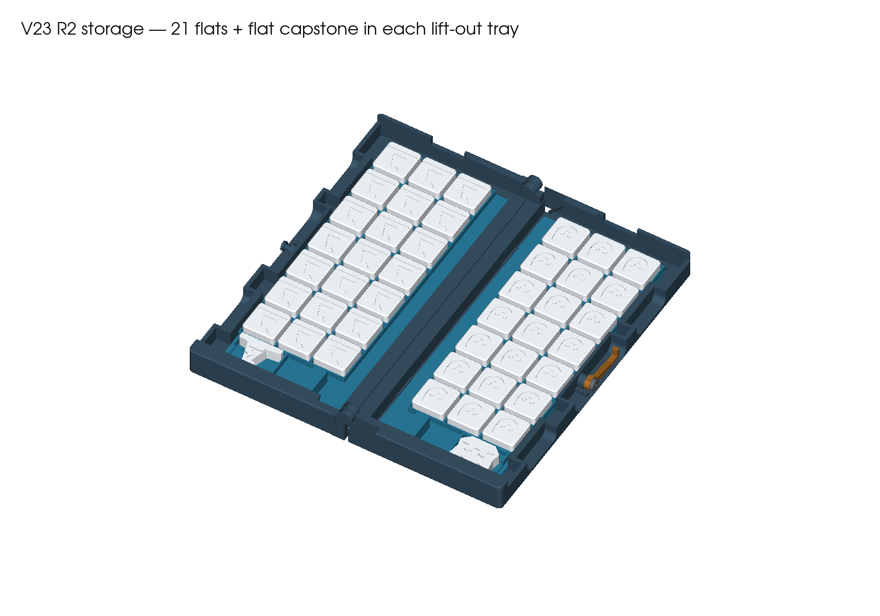
v23-r2/previews/04-loaded-storage.png
