Arcadesys/tak-box/v23-r2/previews/05-hinge-detail.png

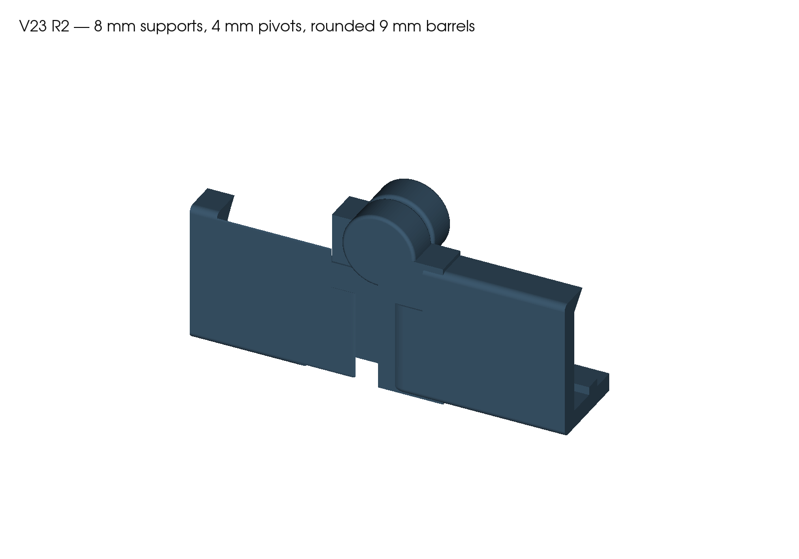
v23-r2/previews/05-hinge-detail.png
