Arcadesys/tak-box/v23-r2/previews/06-pin-passages-1.png

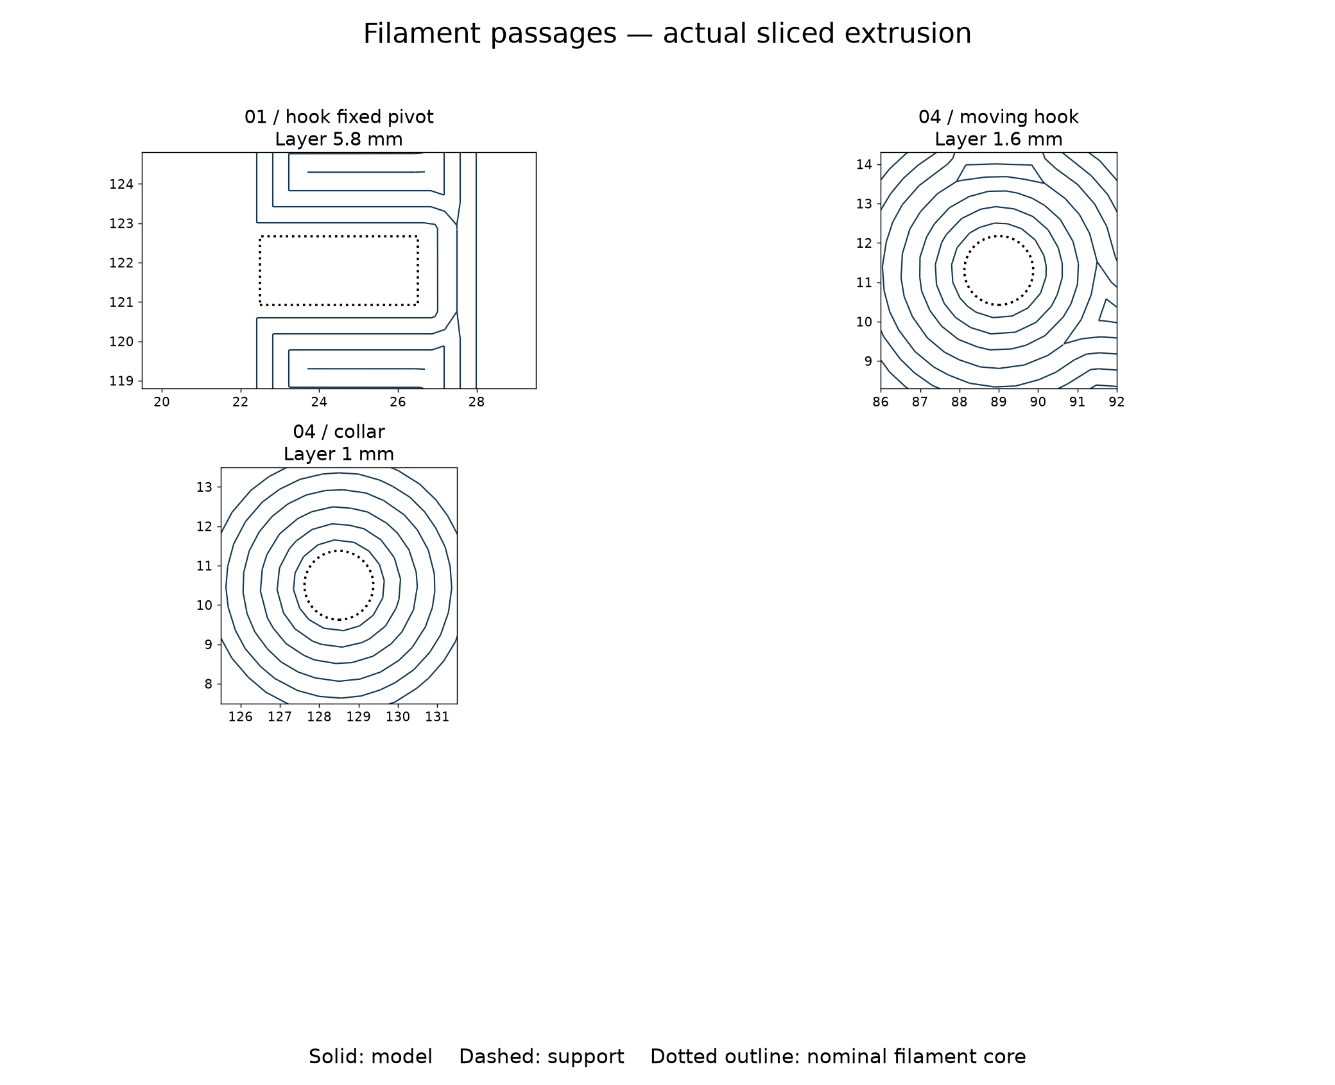
v23-r2/previews/06-pin-passages-1.png
