Arcadesys/tak-box/v23-r2/previews/07-captive-hinge-gaps.png

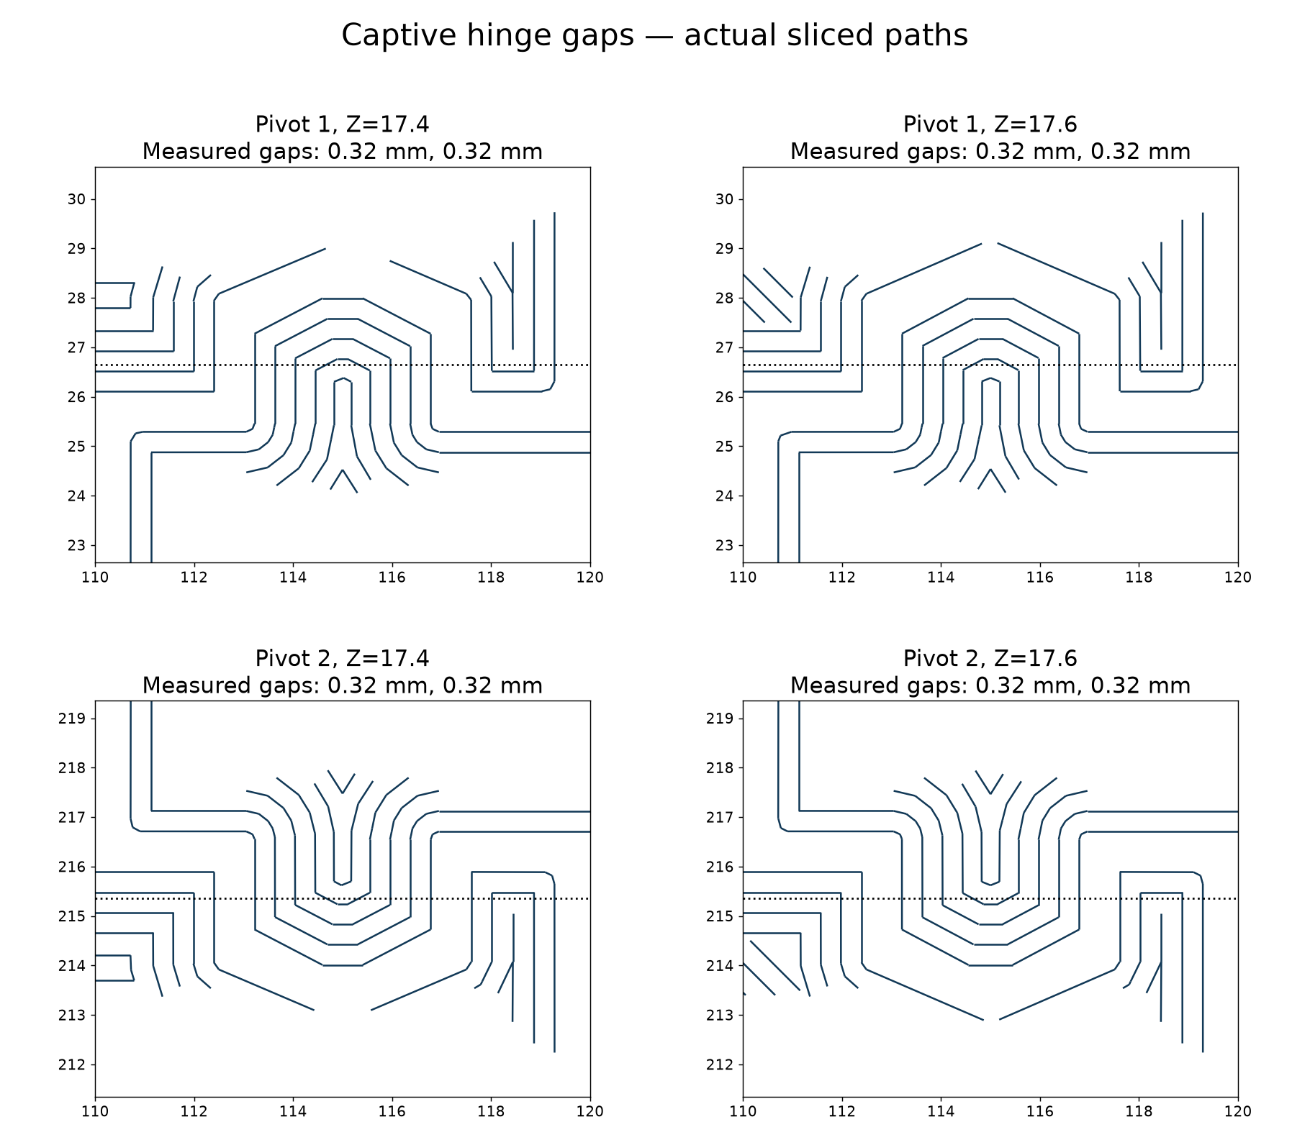
v23-r2/previews/07-captive-hinge-gaps.png
