Arcadesys/tak-box/v23-r2/TRAY-FIT/layers.png

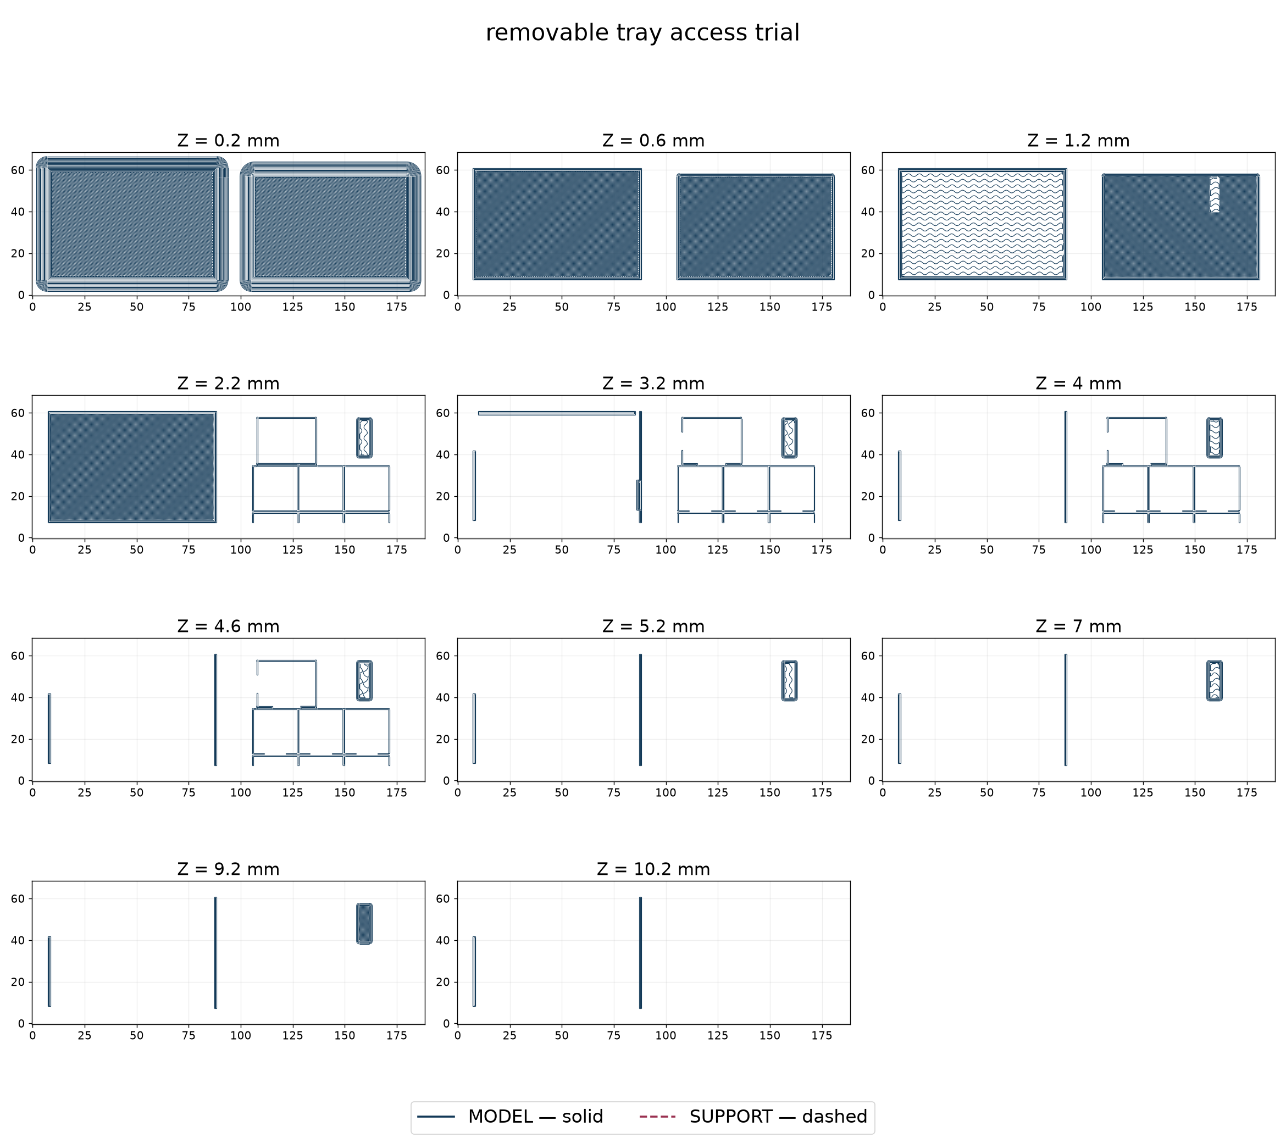
v23-r2/TRAY-FIT/layers.png
