Arcadesys/tak-box/v26/previews/01-game-open.png

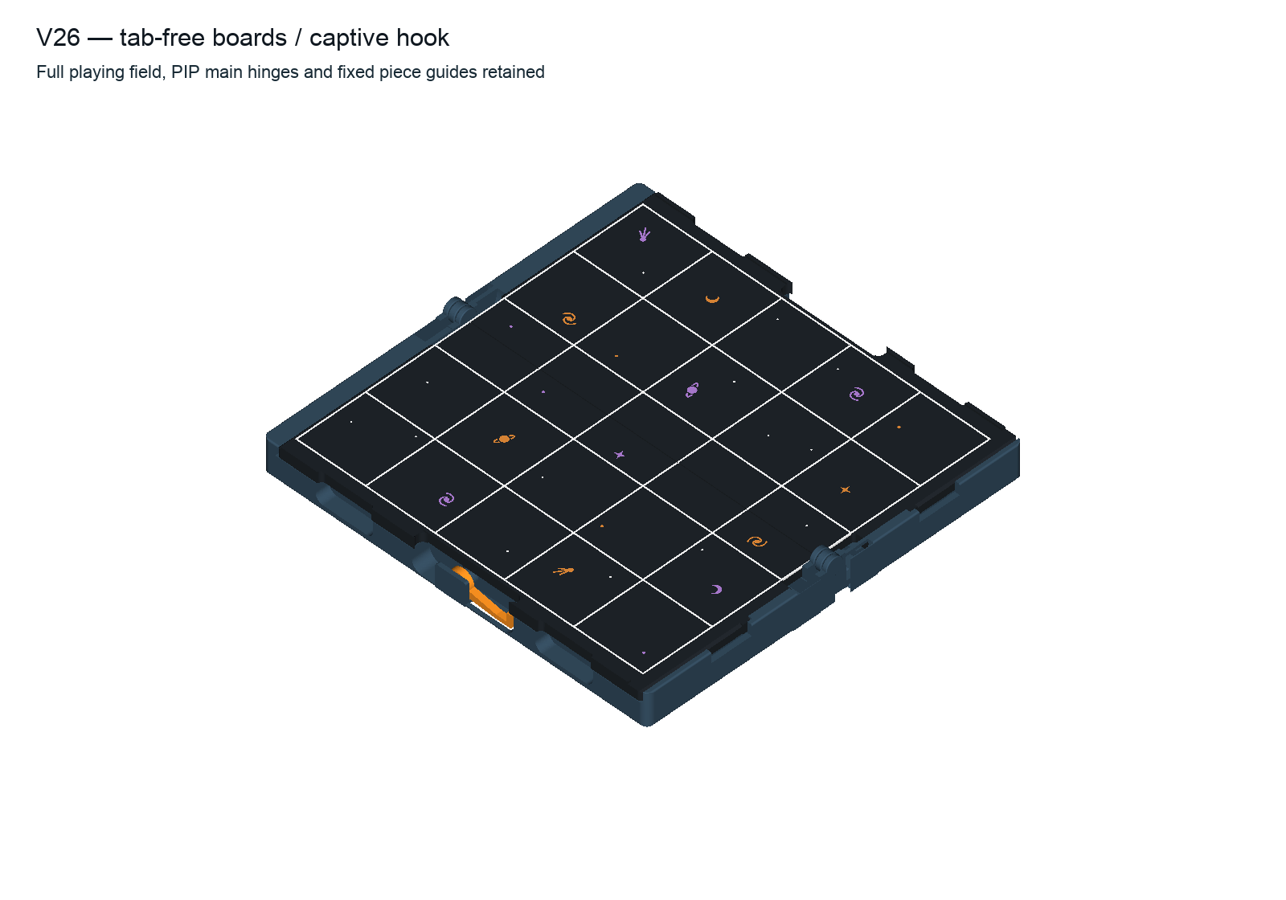
v26/previews/01-game-open.png
