Arcadesys/tak-box/v26/previews/02-board-clip.png

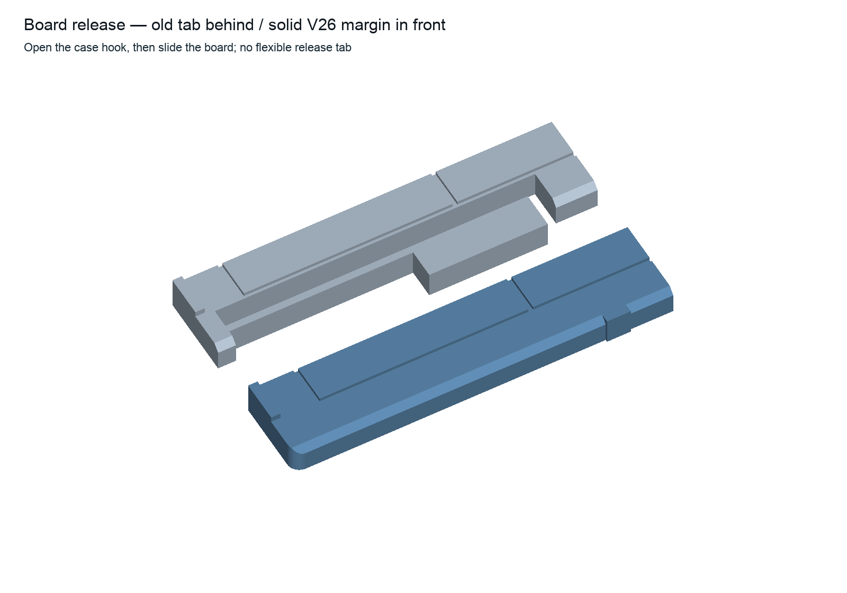
v26/previews/02-board-clip.png
