Arcadesys/tak-box/v26/previews/03-captive-hook.png

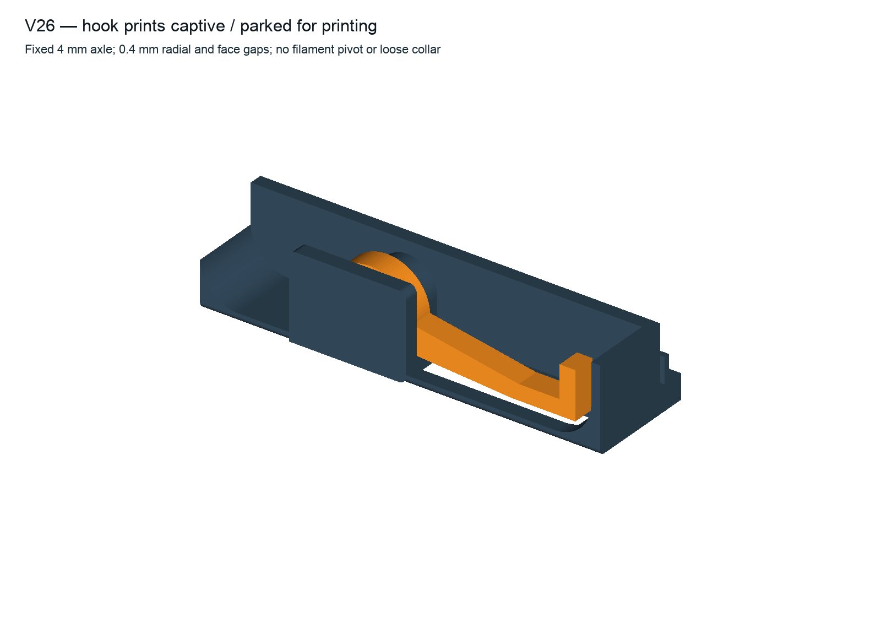
v26/previews/03-captive-hook.png
