Arcadesys/tak-box/v26/previews/04-hook-section.png

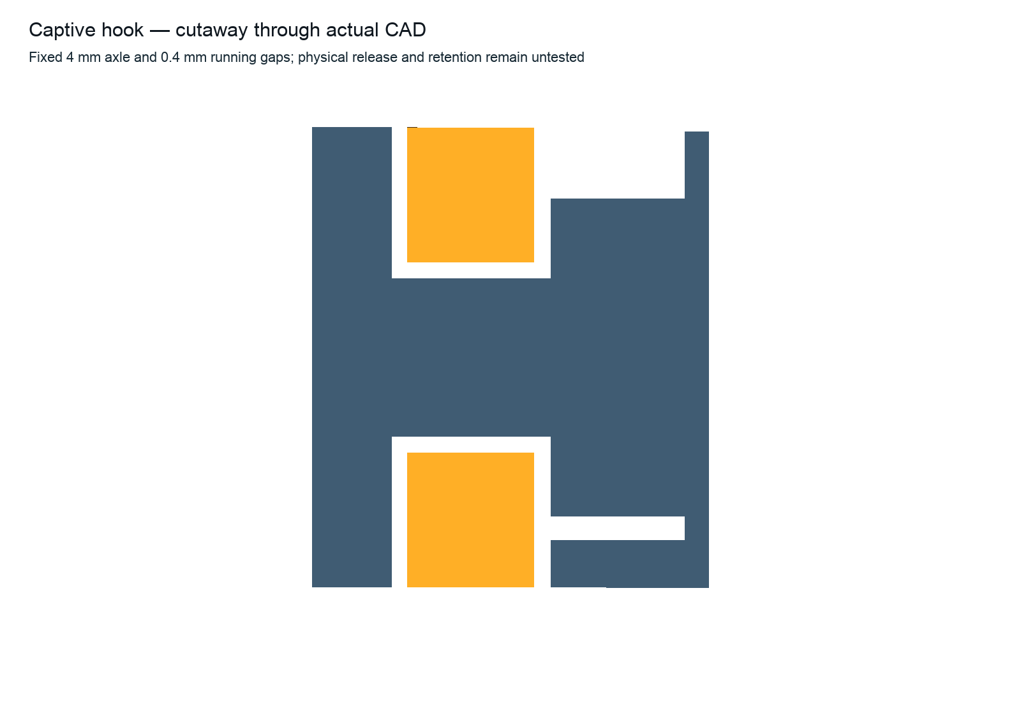
v26/previews/04-hook-section.png
