Arcadesys/tak-box/v26/previews/05-closed.png

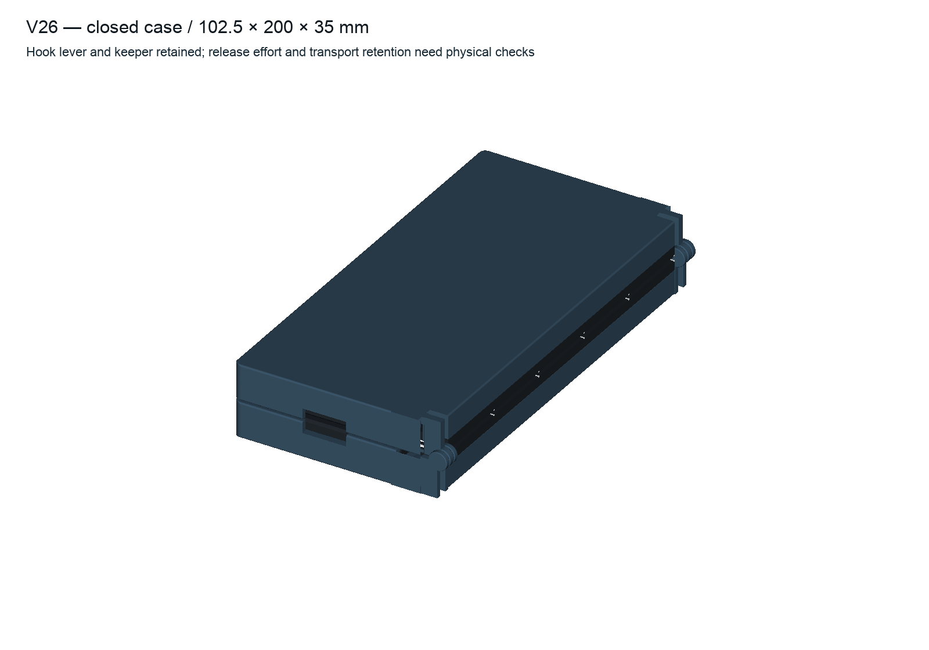
v26/previews/05-closed.png
