Arcadesys/tak-box/v26/previews/07-hook-sliced-gaps.png

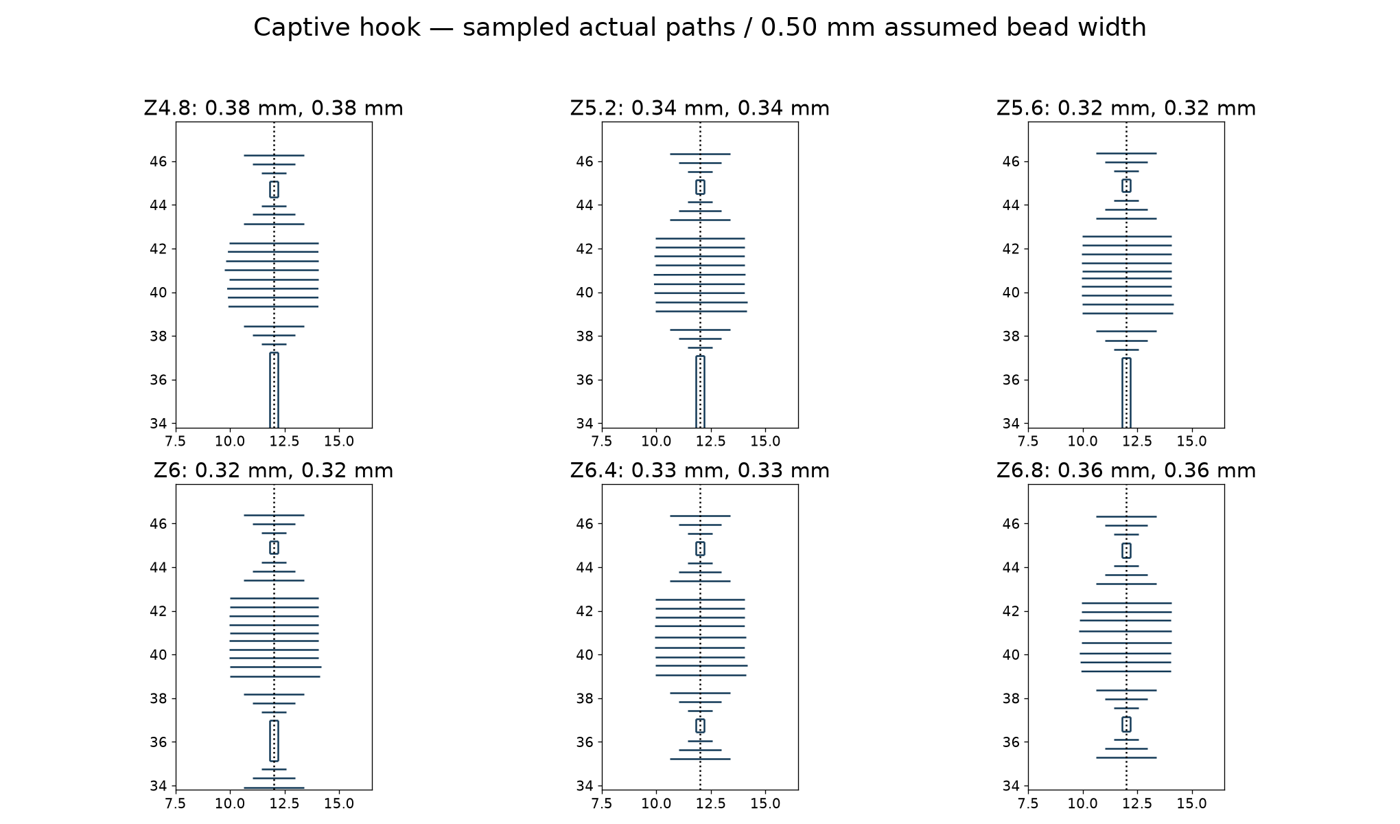
v26/previews/07-hook-sliced-gaps.png
