Arcadesys/tak-box/v26/previews/08-combined-trials.png

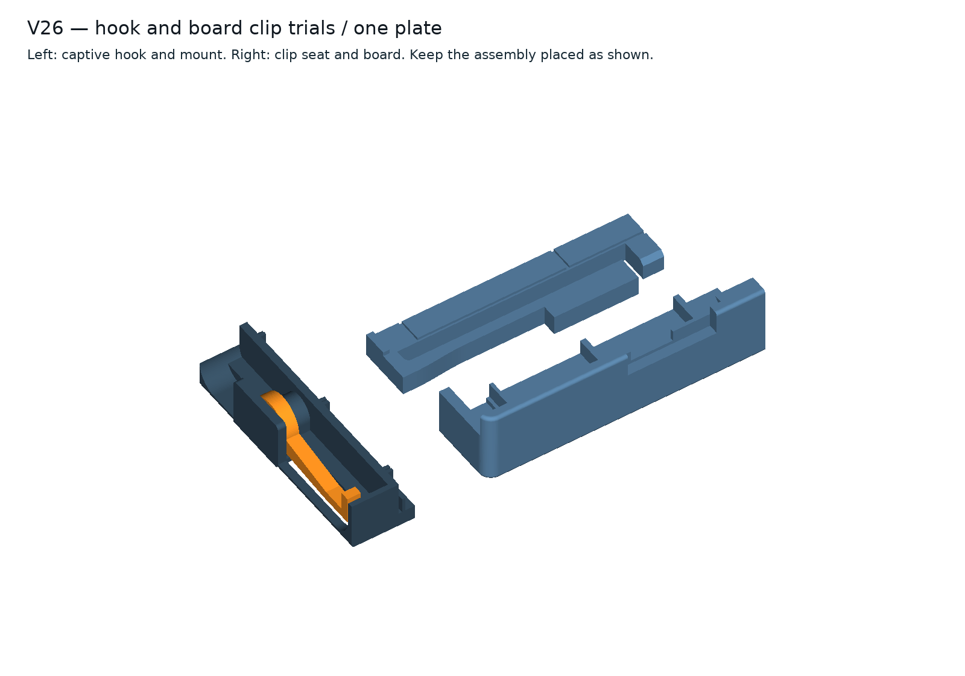
v26/previews/08-combined-trials.png
