Arcadesys/tak-box/v26/previews/10-full-PIP-sliced-gaps.png

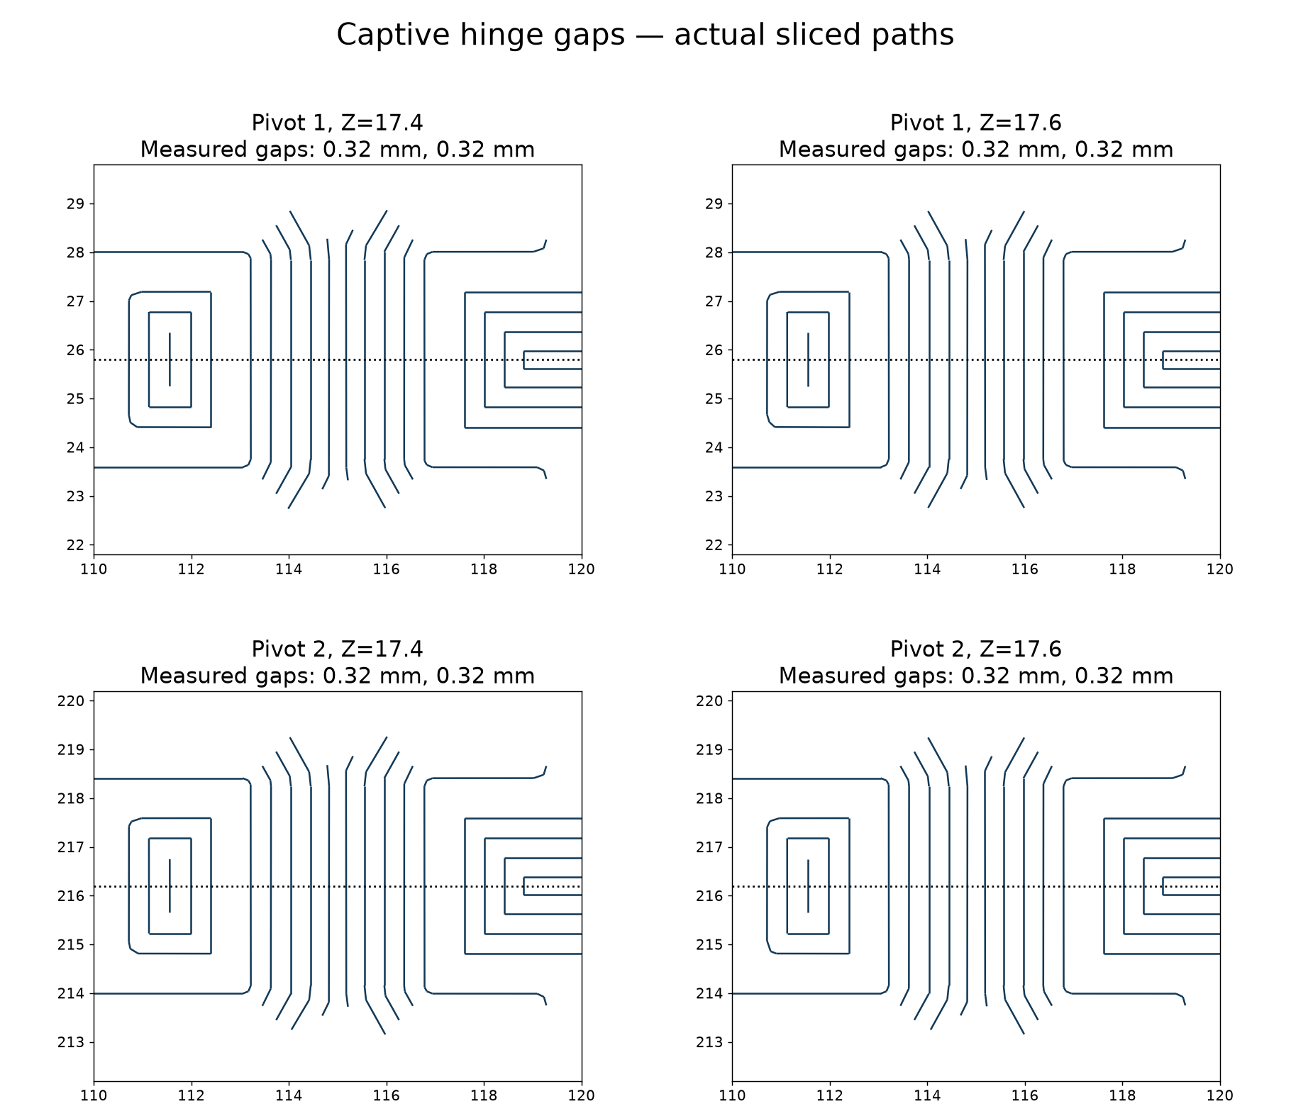
v26/previews/10-full-PIP-sliced-gaps.png
