Arcadesys/tak-box/v26/previews/12-case-plate.png

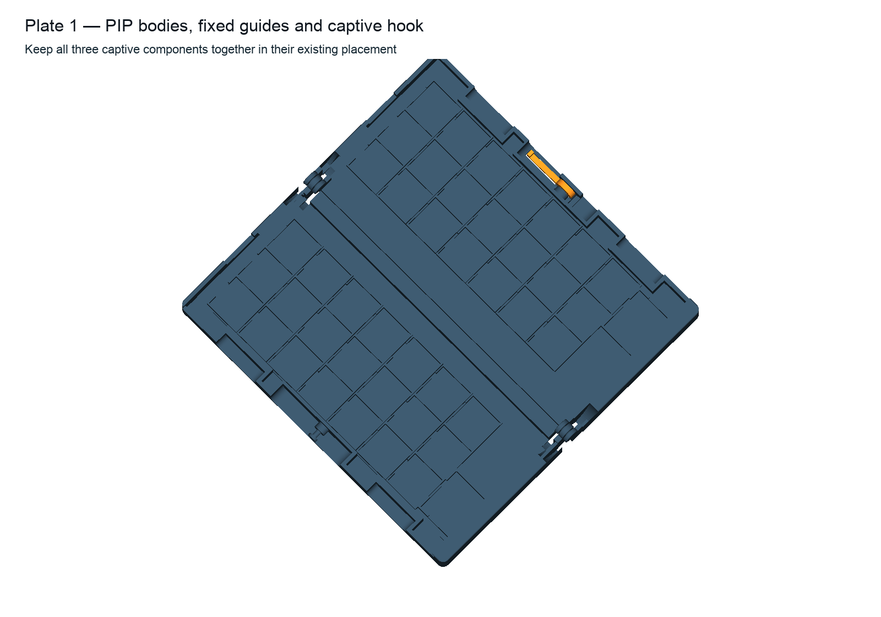
v26/previews/12-case-plate.png
