Arcadesys/tak-box/v26/previews/13-board-plate.png

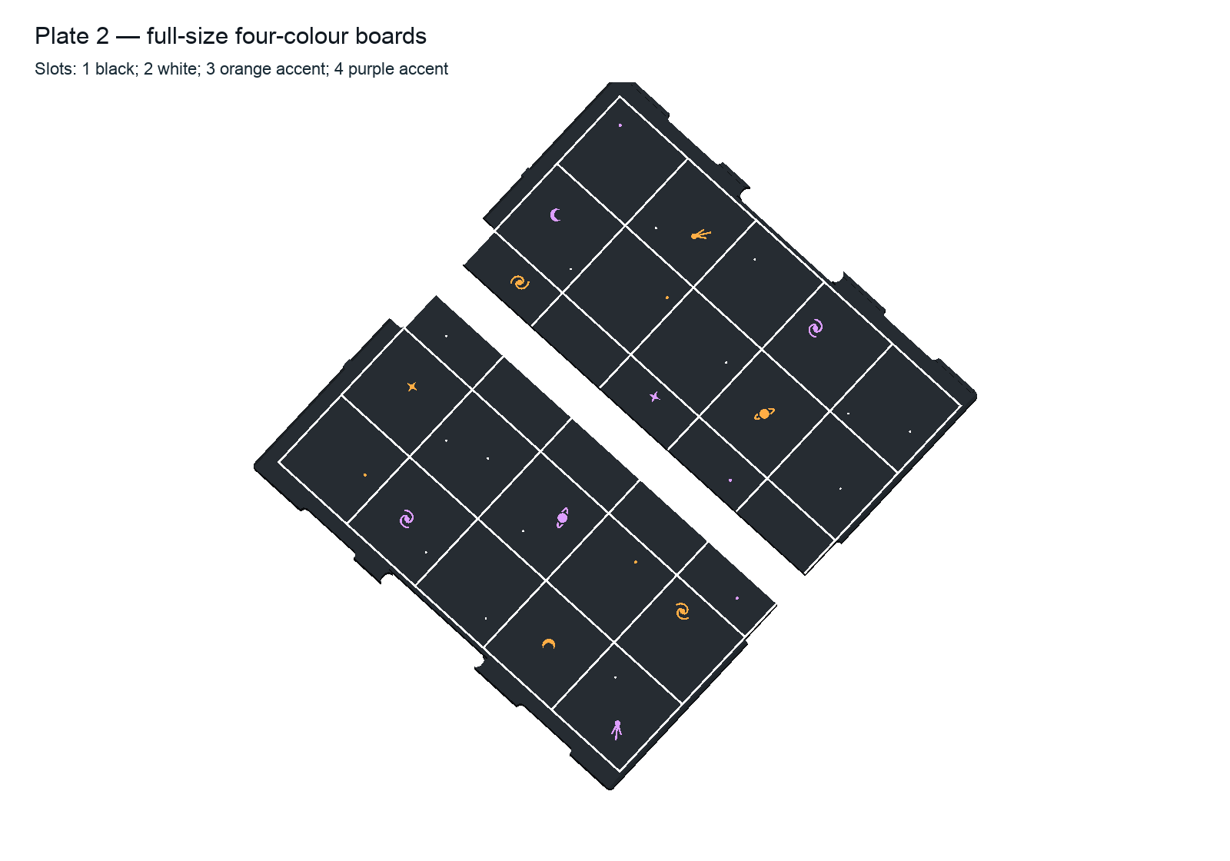
v26/previews/13-board-plate.png
