Arcadesys/tak-box/v26/previews/14-capstone-plate.png

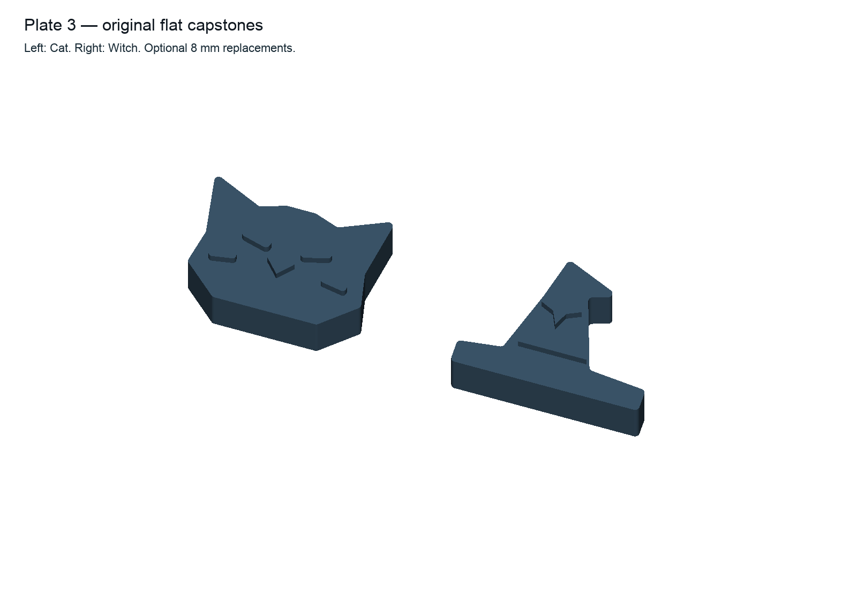
v26/previews/14-capstone-plate.png
