Arcadesys/tak-box/v26/previews/15-full-sliced-colour-layer.png

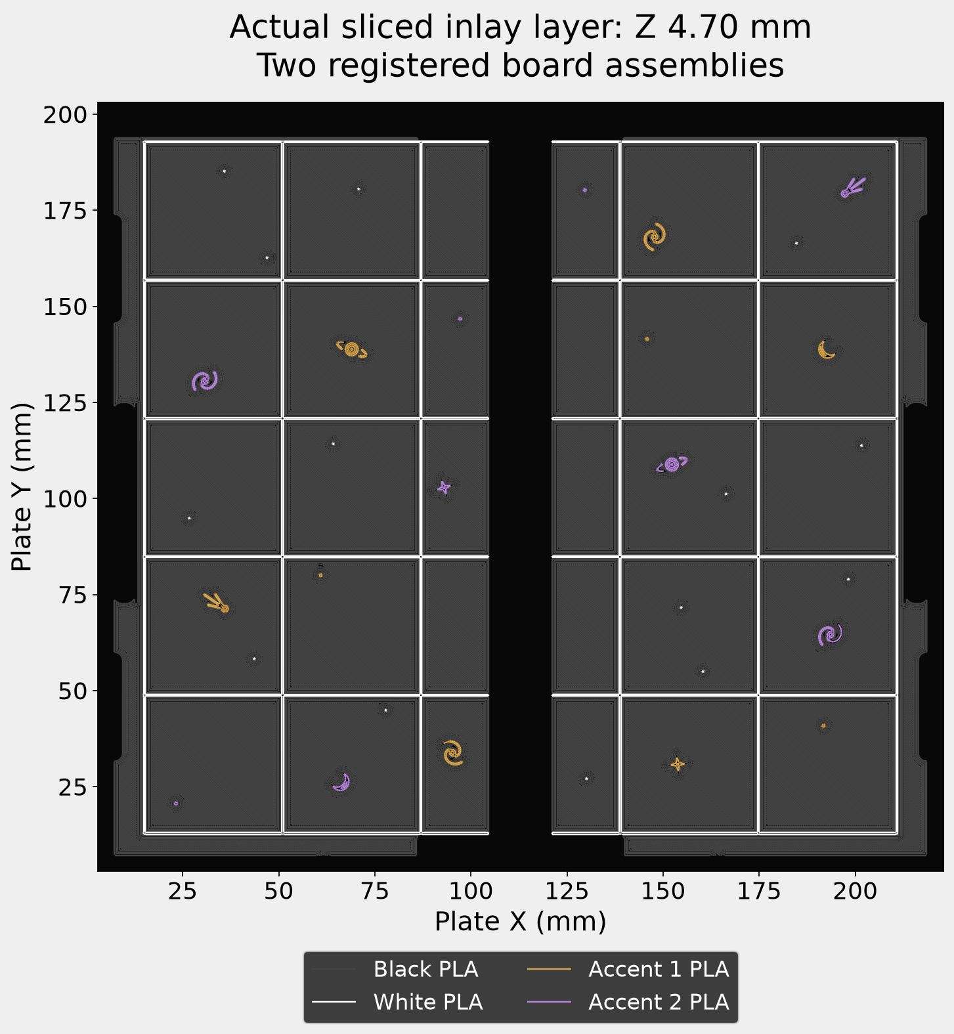
v26/previews/15-full-sliced-colour-layer.png
