Arcadesys/tak-box/v26/previews/16-main-hinge.png

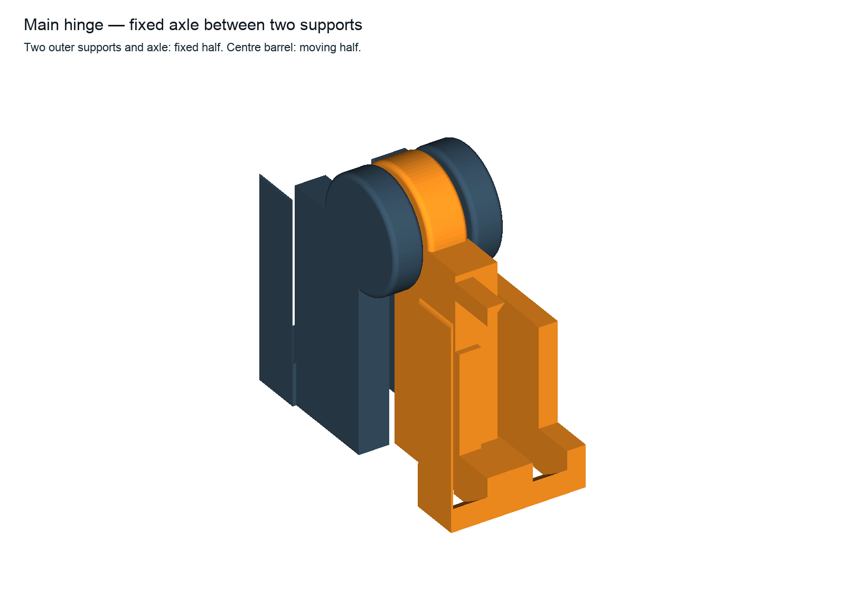
v26/previews/16-main-hinge.png
