Arcadesys/tak-box/v26/previews/18-rounded-corner.png

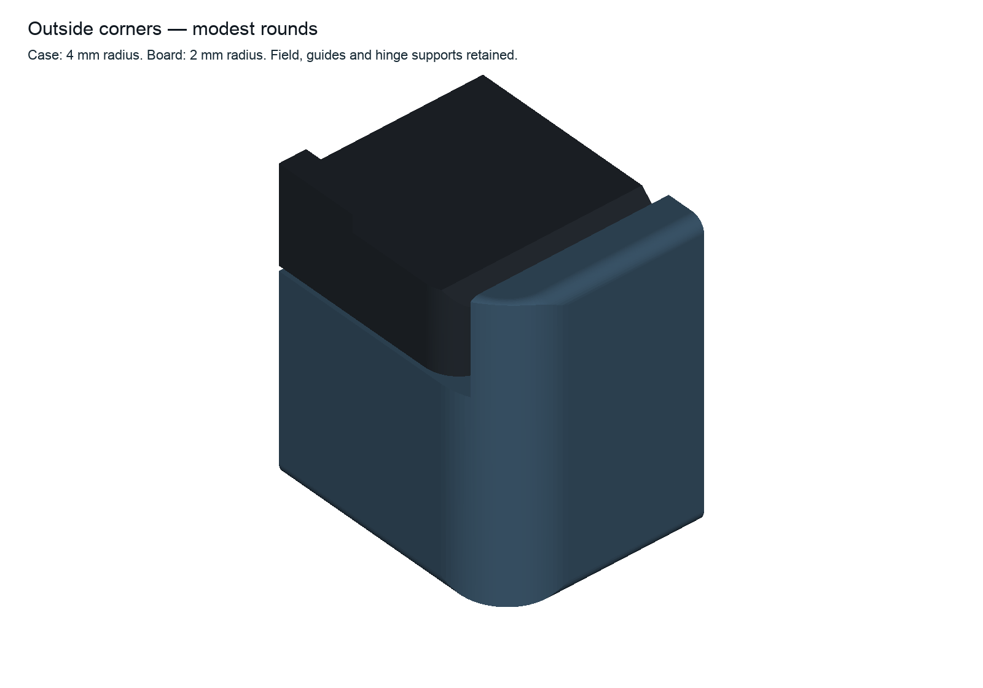
v26/previews/18-rounded-corner.png
