Arcadesys/tak-box/v18-recessed-clasp/parts/V18-slider-assembled.step

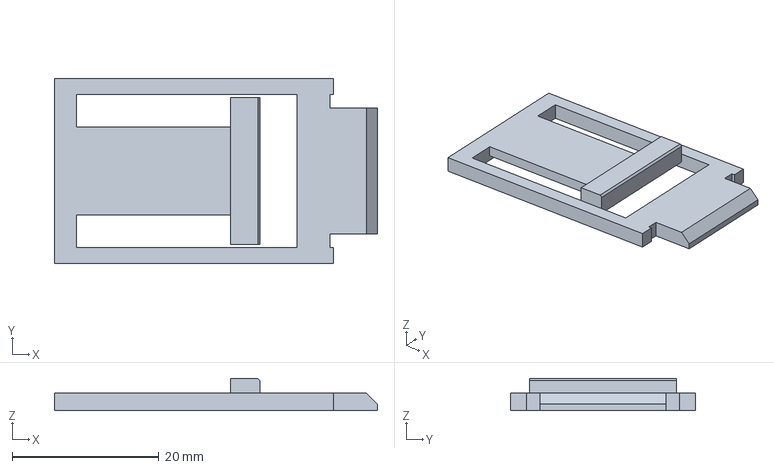
[picture p134: CAD file, 2026-10-09]
v18-recessed-clasp/parts/V18-slider-assembled.step
44.0 x 25.2 x 4.40 mm
