Arcadesys/tak-box/full-size-pagoda-v1/models/fox-assembled-reference.step

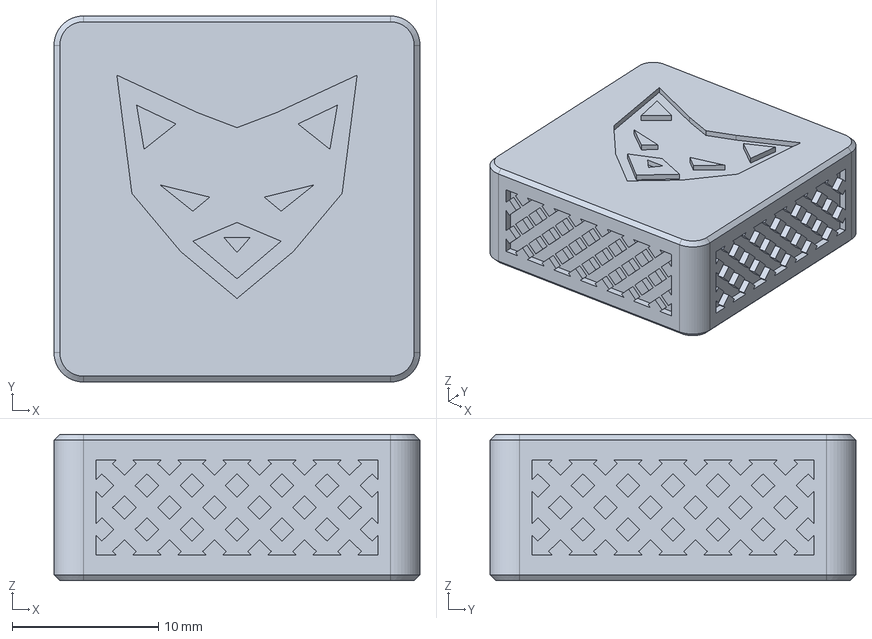
[picture p135: CAD file, 2026-10-03]
full-size-pagoda-v1/models/fox-assembled-reference.step
25.0 x 25.0 x 10.0 mm
