Arcadesys/tak-box/v16-field-book/models/assembly-closed.step

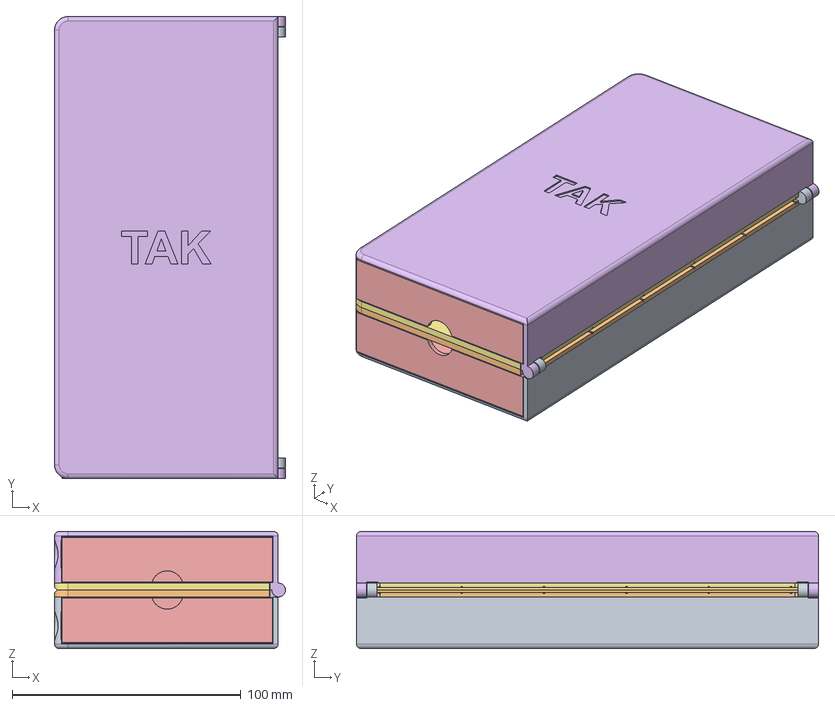
[picture p136: CAD file, 2026-09-30]
v16-field-book/models/assembly-closed.step
101.0 x 202.0 x 51.2 mm
