Arcadesys/tak-box/v23-r2/models/assembly-closed-with-hardware.step

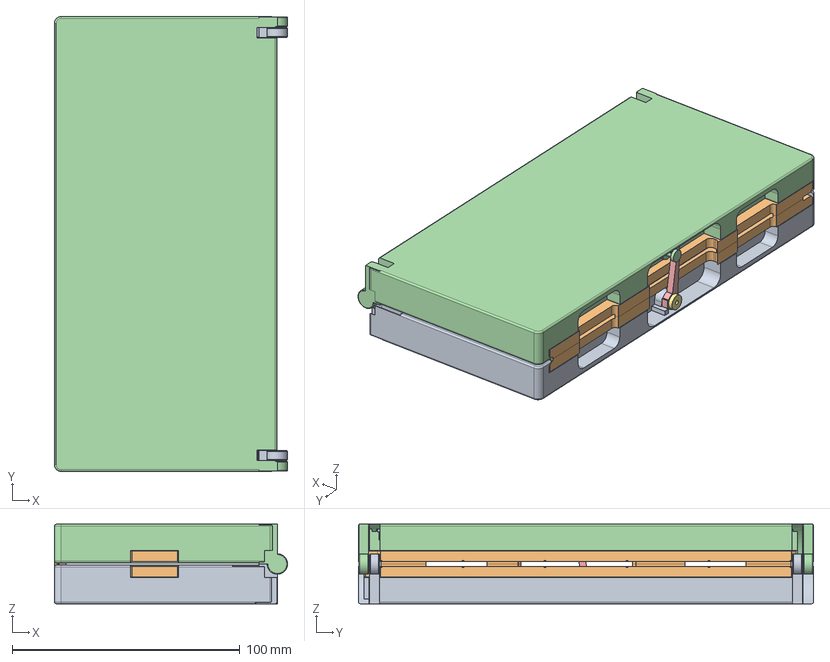
[picture p137: CAD file, 2026-10-09]
v23-r2/models/assembly-closed-with-hardware.step
102.5 x 200.0 x 35.0 mm
