Arcadesys/tak-box/pieces/weighted-flat-capstones-v2/models/cat-regular-assembled.step

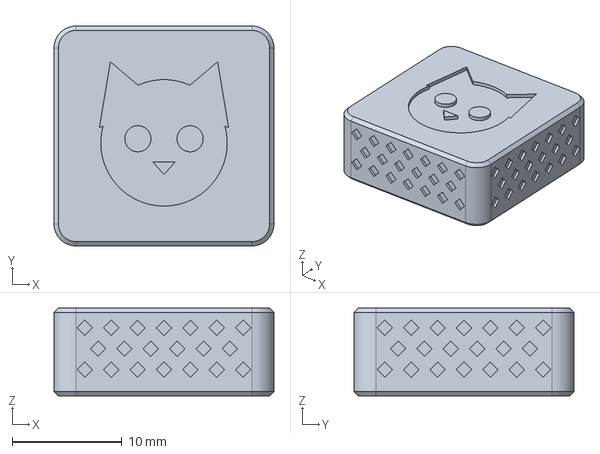
[picture p138: CAD file, 2026-10-09]
pieces/weighted-flat-capstones-v2/models/cat-regular-assembled.step
20.0 x 20.0 x 8.00 mm
