Arcadesys/tak-box/v18-case/models/assembly-open.step

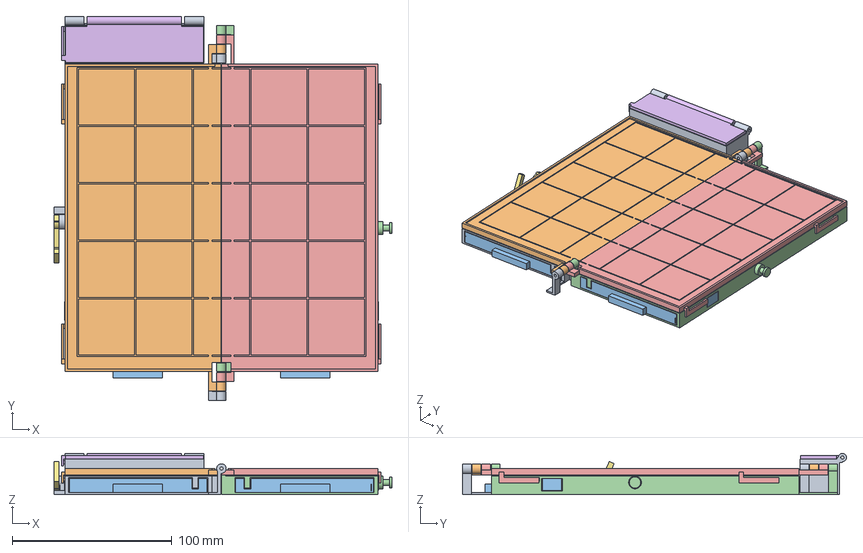
[picture p139: CAD file, 2026-10-09]
v18-case/models/assembly-open.step
211.6 x 240.4 x 25.8 mm
