Arcadesys/tak-box/v23-r2/models/assembly-loaded.step

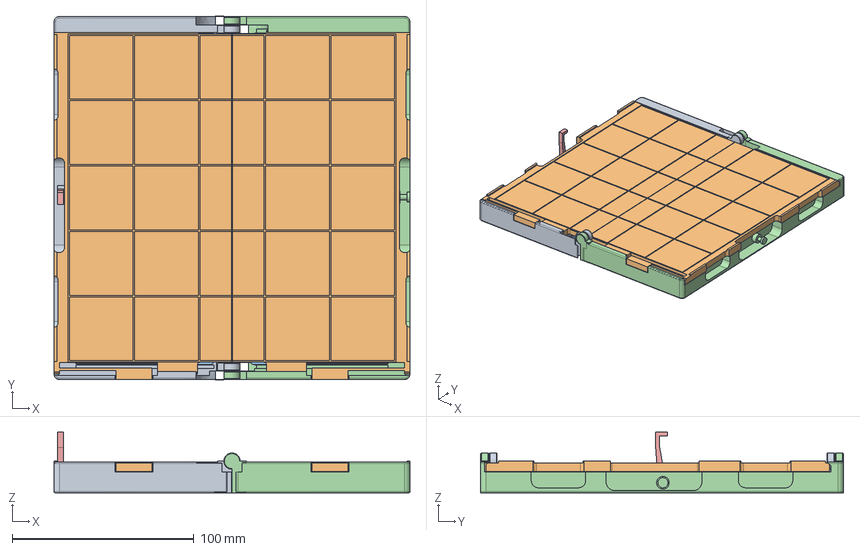
[picture p140: CAD file, 2026-10-09]
v23-r2/models/assembly-loaded.step
196.0 x 200.0 x 33.5 mm
