Arcadesys/tak-box/pieces/weighted-flat-capstones-v2/models/cat-capstone-assembled.step

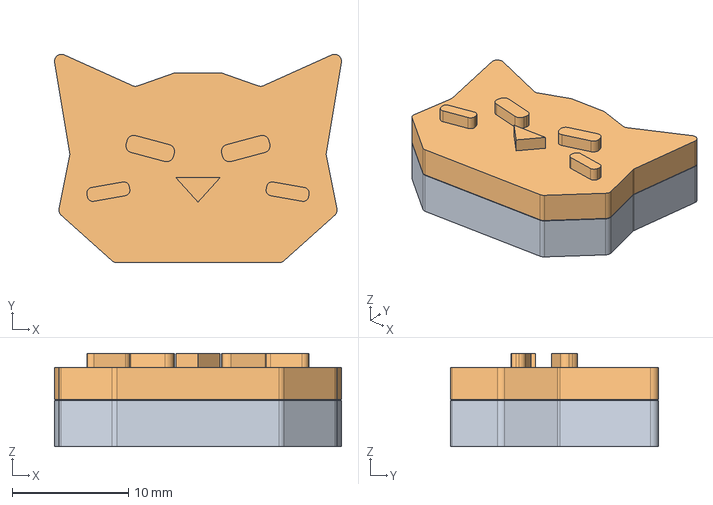
[picture p141: CAD file, 2026-10-09]
pieces/weighted-flat-capstones-v2/models/cat-capstone-assembled.step
24.6 x 17.9 x 8.00 mm
