Arcadesys/tak-box/v18-case/models/assembly-open-with-hardware.step

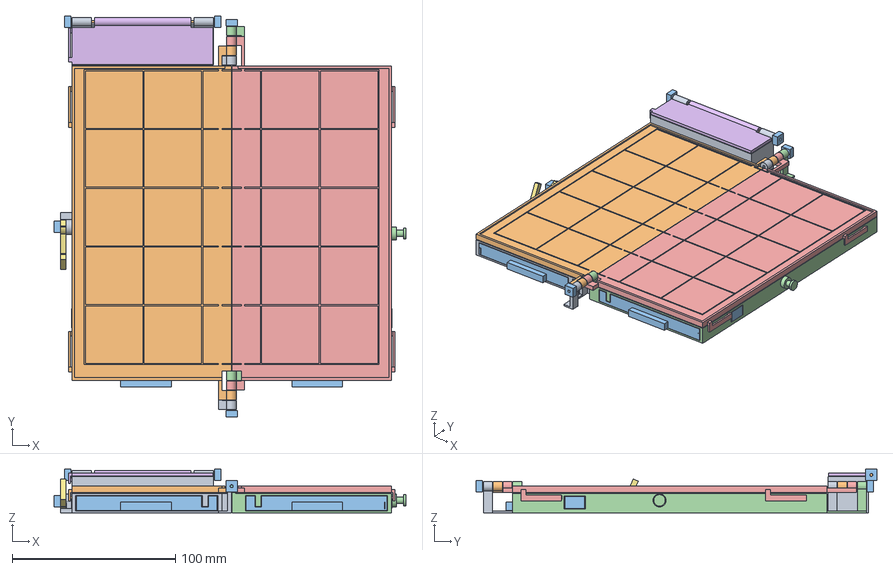
[picture p142: CAD file, 2026-10-09]
v18-case/models/assembly-open-with-hardware.step
215.6 x 245.8 x 26.7 mm
