Arcadesys/tak-box/full-size-pagoda-v1/models/cat-body-assembly.stl

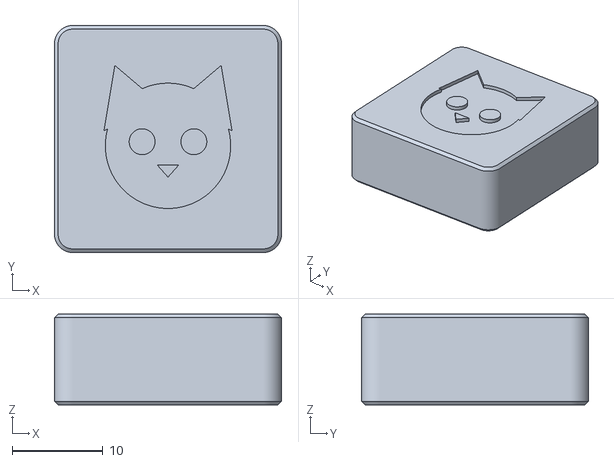
[picture p143: CAD file, 2026-10-03]
full-size-pagoda-v1/models/cat-body-assembly.stl
25.0 x 25.0 x 10.0
