Arcadesys/tak-box/main-hinge-pin.stl

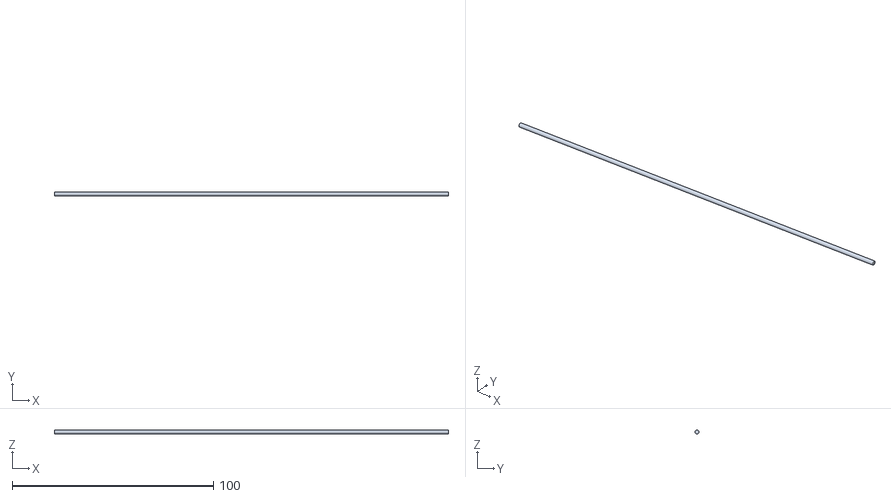
[picture p144: CAD file, 2026-09-25]
main-hinge-pin.stl
195.8 x 2.00 x 2.00
