Arcadesys/tak-box/v18-case/models/assembly-closed.step

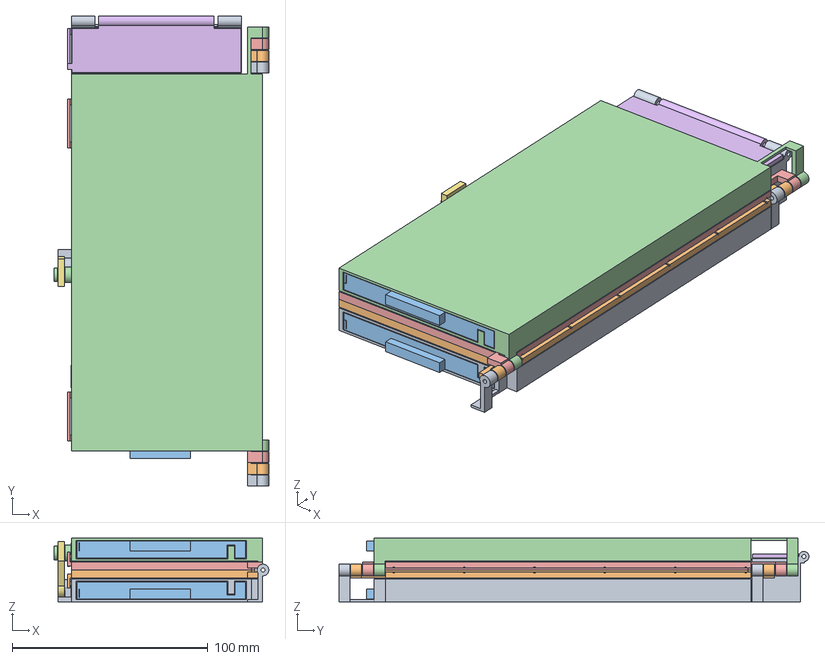
[picture p145: CAD file, 2026-10-09]
v18-case/models/assembly-closed.step
109.8 x 240.4 x 32.6 mm
