Arcadesys/tak-box/pieces/weighted-flat-capstones-v2/models/witch-capstone-assembled.step

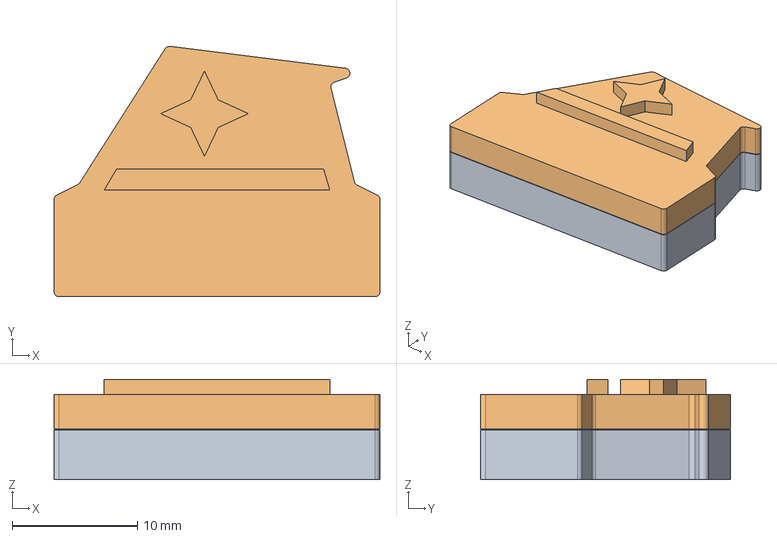
[picture p146: CAD file, 2026-10-09]
pieces/weighted-flat-capstones-v2/models/witch-capstone-assembled.step
26.0 x 20.0 x 8.00 mm
