Arcadesys/tak-box/full-size-pagoda-v1/models/fox-body-assembly.stl

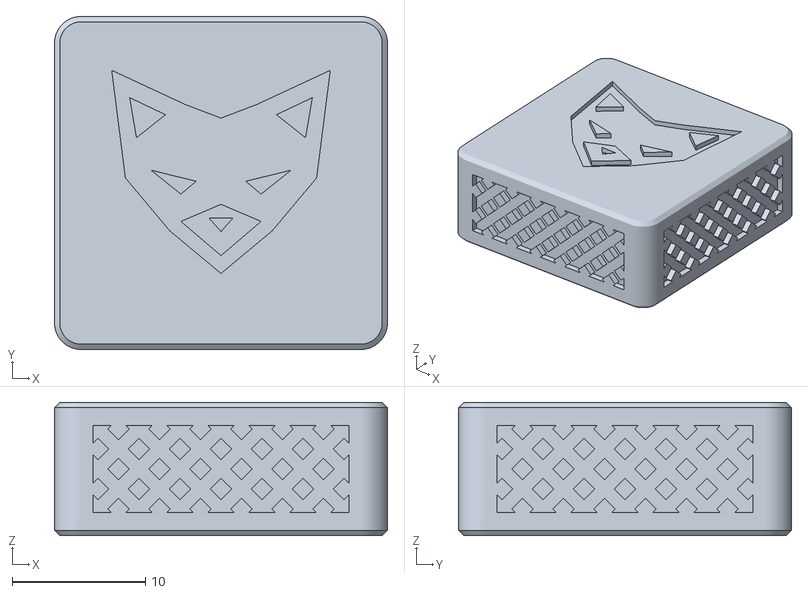
[picture p147: CAD file, 2026-10-03]
full-size-pagoda-v1/models/fox-body-assembly.stl
25.0 x 25.0 x 10.0
