Arcadesys/tak-box/v16-field-book/models/assembly-trays-out.step

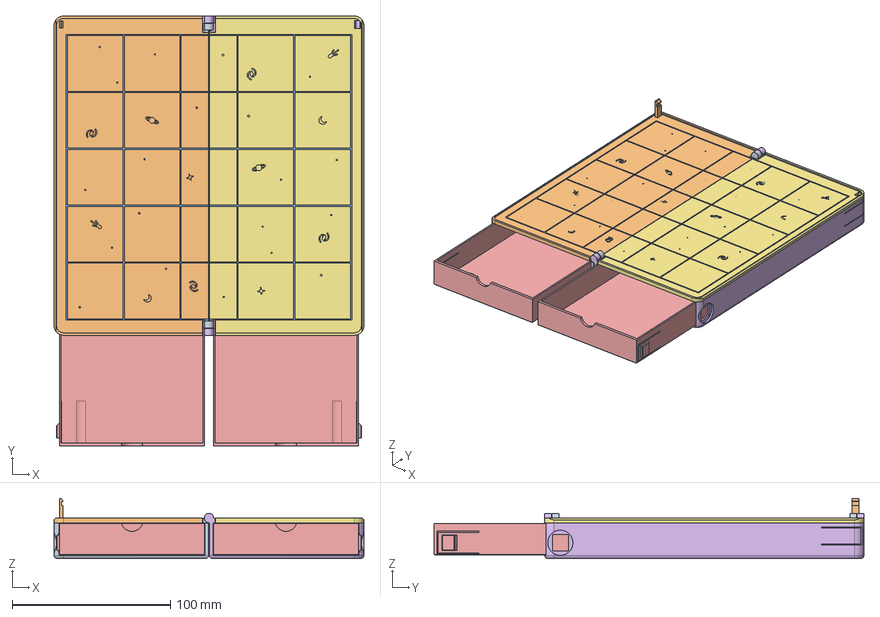
[picture p148: CAD file, 2026-09-30]
v16-field-book/models/assembly-trays-out.step
196.0 x 272.0 x 38.0 mm
