Arcadesys/tak-box/v16-field-book/models/assembly-open.step

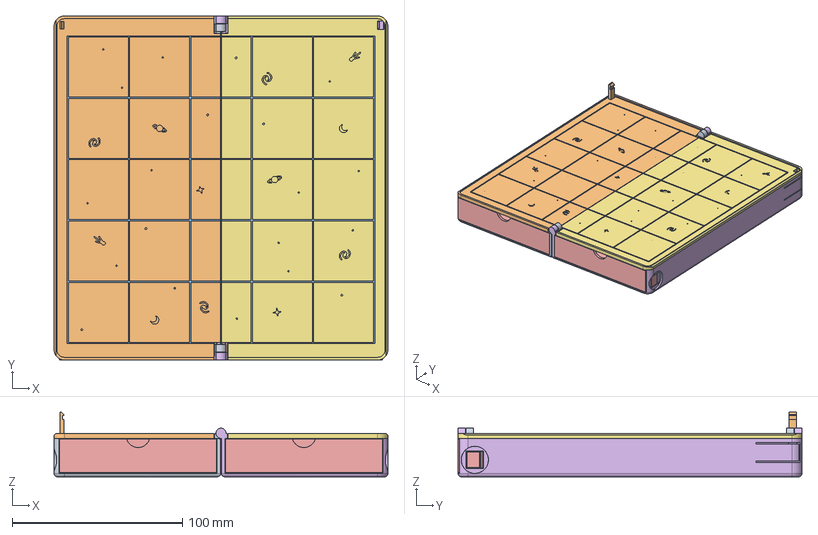
[picture p149: CAD file, 2026-09-30]
v16-field-book/models/assembly-open.step
196.0 x 202.0 x 38.0 mm
