Arcadesys/tak-box/centauri-carbon-2-3mf/tak-pin-board-cc2-81-white-wing-a-lid-a.3mf

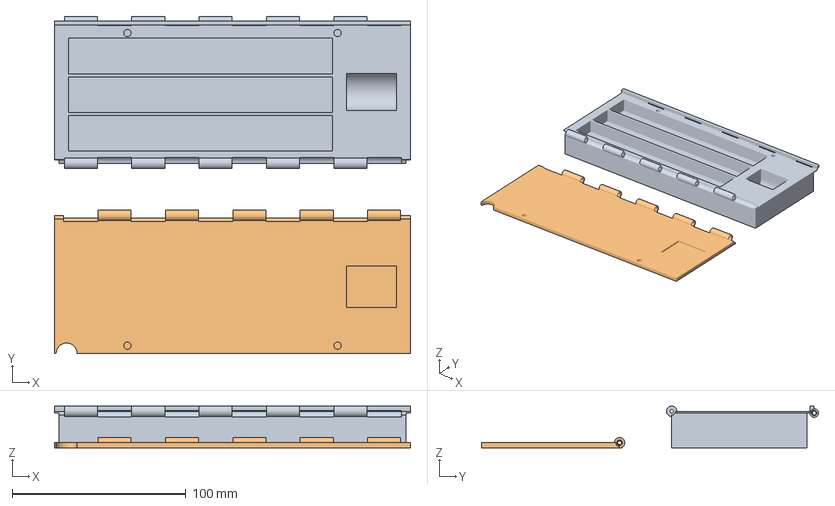
[picture p150: CAD file, 2026-09-26]
centauri-carbon-2-3mf/tak-pin-board-cc2-81-white-wing-a-lid-a.3mf
205.0 x 194.0 x 24.1 mm
wing-a.stl
lid-a.stl
