Arcadesys/tak-box/center-closure-coupon/coupon-wing-0.stl

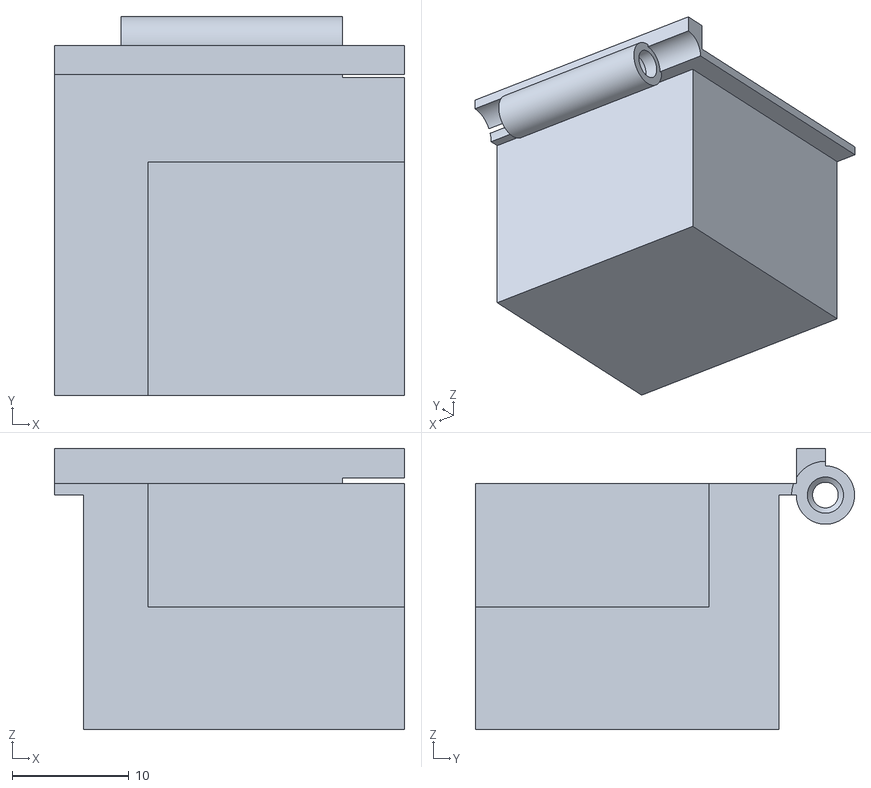
[picture p151: CAD file, 2026-09-27]
center-closure-coupon/coupon-wing-0.stl
30.0 x 32.5 x 24.1
