Arcadesys/tak-box/center-closure-v7/center-row-revised.step

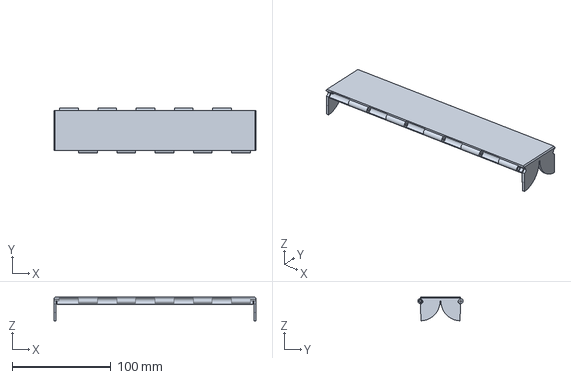
[picture p152: CAD file, 2026-09-27]
center-closure-v7/center-row-revised.step
205.0 x 46.0 x 24.1 mm
