Arcadesys/tak-box/fit-coupon/lift-up-lid.stl

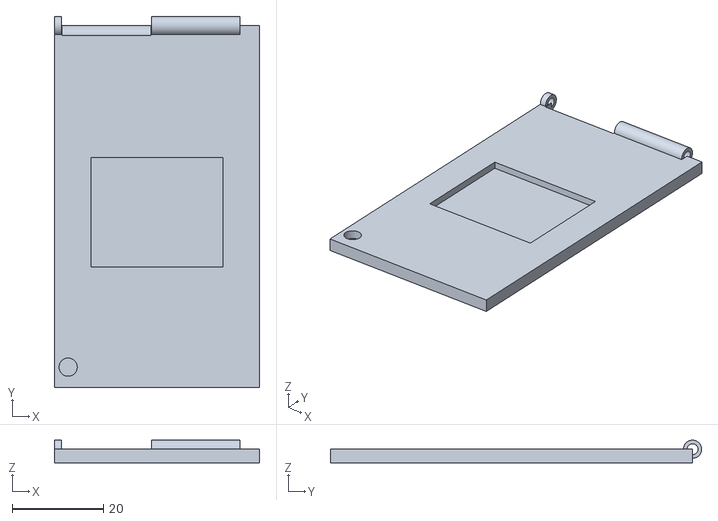
[picture p153: CAD file, 2026-09-25]
fit-coupon/lift-up-lid.stl
45.0 x 81.5 x 5.00
