Arcadesys/tak-box/full-size-pagoda-v1/models/tray.step

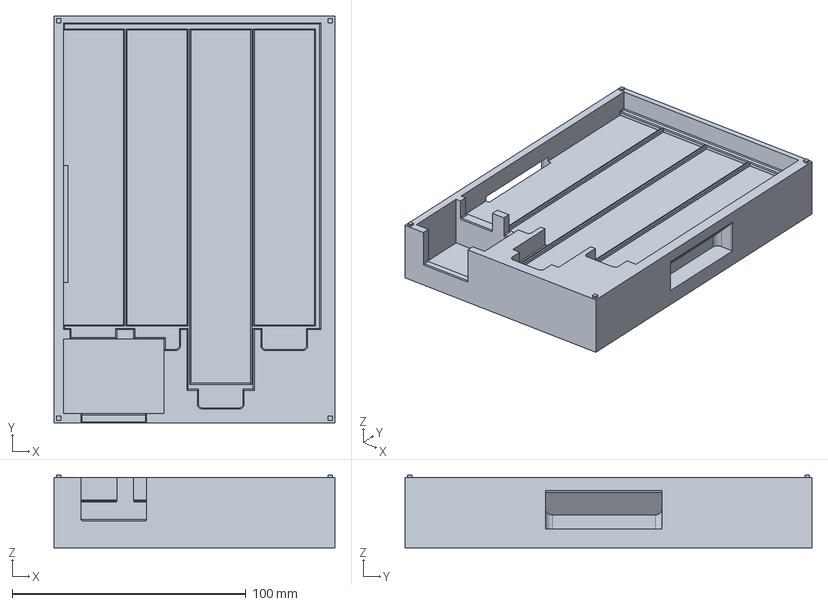
[picture p154: CAD file, 2026-10-09]
full-size-pagoda-v1/models/tray.step
120.0 x 174.0 x 31.0 mm
