Arcadesys/tak-box/full-size-pagoda-v1/references/cassette-before-comfort.step

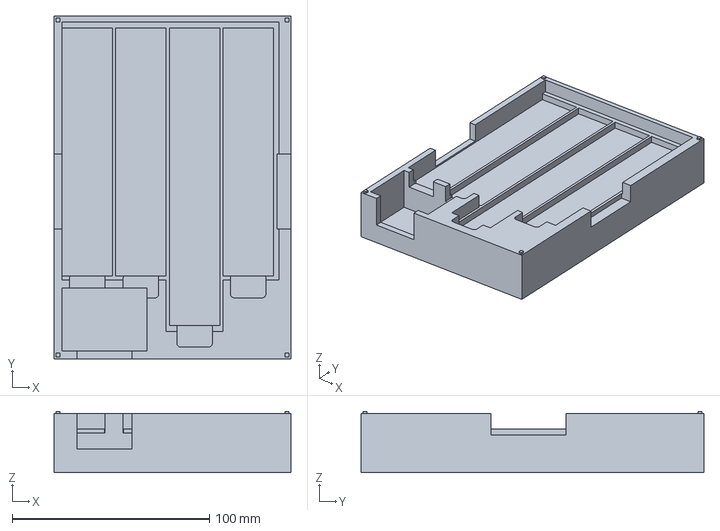
[picture p155: CAD file, 2026-10-03]
full-size-pagoda-v1/references/cassette-before-comfort.step
120.0 x 174.0 x 31.0 mm
