Arcadesys/tak-box/halves/half-A.stl

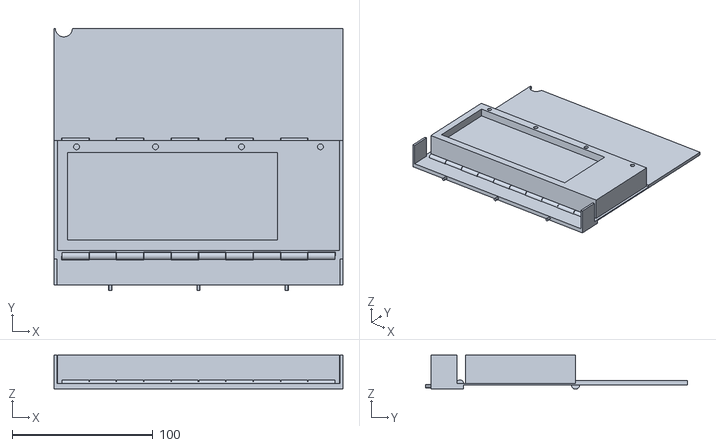
[picture p156: CAD file, 2026-09-26]
halves/half-A.stl
205.0 x 186.0 x 24.1
