Arcadesys/tak-box/hinge-coupons/case/lid-base-slice.stl

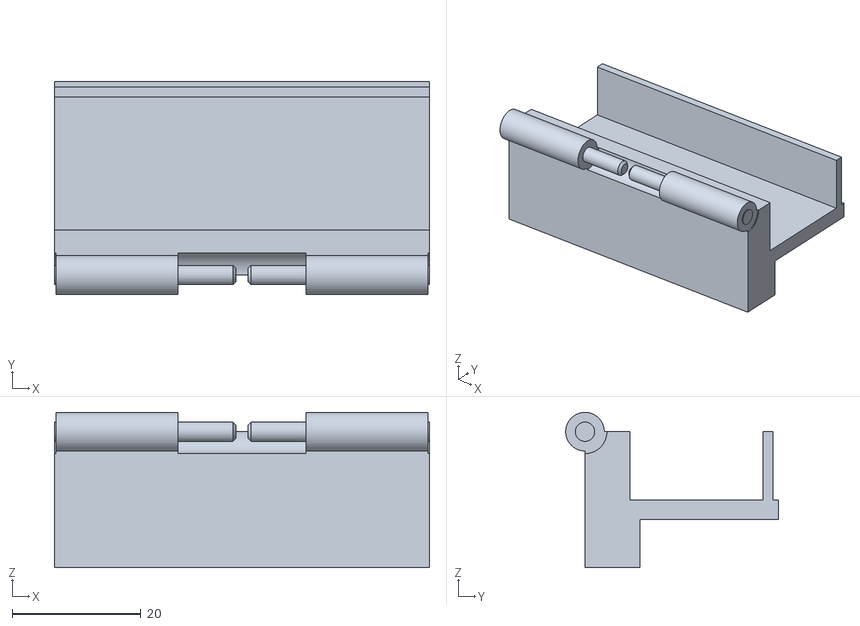
[picture p157: CAD file, 2026-09-26]
hinge-coupons/case/lid-base-slice.stl
58.2 x 33.0 x 24.1
