Arcadesys/tak-box/hinge-coupons/joint/joint-coupon-plate.stl

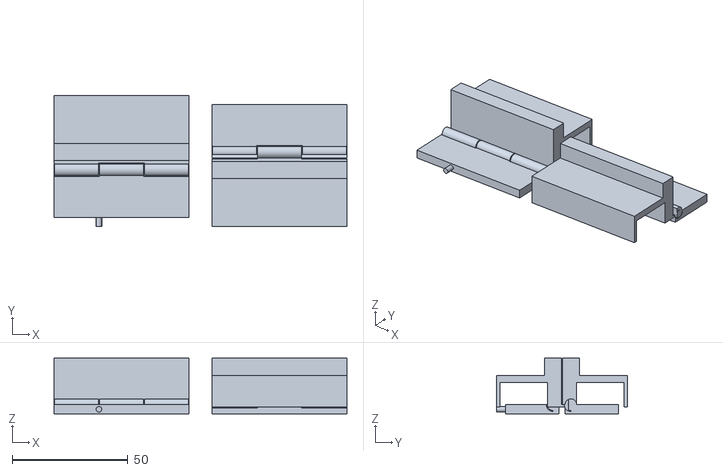
[picture p158: CAD file, 2026-09-26]
hinge-coupons/joint/joint-coupon-plate.stl
126.4 x 56.7 x 24.1
