Arcadesys/tak-box/hinge-coupons/magnet/magnet-fit-tab.stl

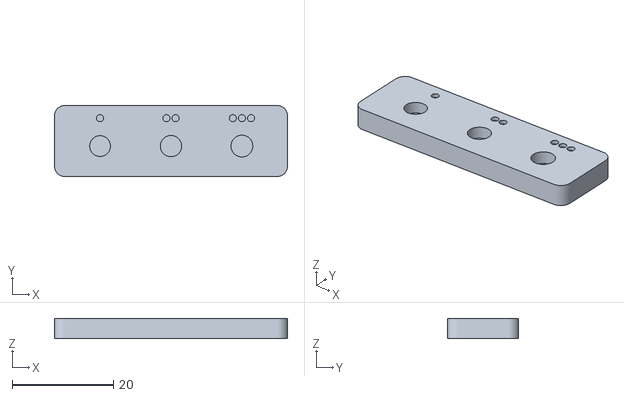
[picture p159: CAD file, 2026-09-26]
hinge-coupons/magnet/magnet-fit-tab.stl
46.0 x 14.0 x 4.00
