Arcadesys/tak-box/hinge-coupons/pinfit/pinfit-plate.stl

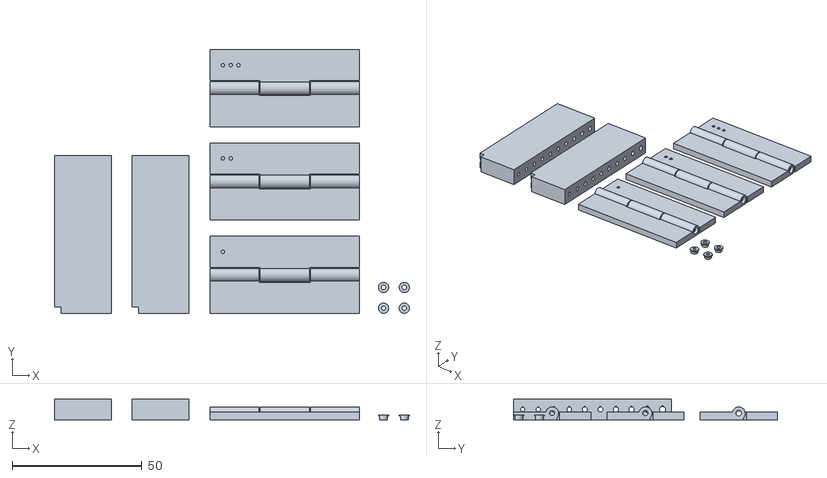
[picture p160: CAD file, 2026-09-26]
hinge-coupons/pinfit/pinfit-plate.stl
137.0 x 101.8 x 8.00
