Arcadesys/tak-box/hinge-coupons/pip-hinge-strip.step

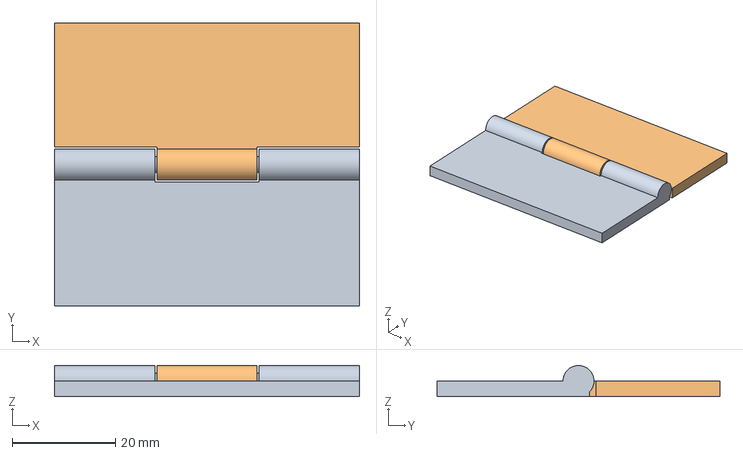
[picture p161: CAD file, 2026-09-26]
hinge-coupons/pip-hinge-strip.step
59.0 x 54.8 x 6.00 mm
