Arcadesys/tak-box/hinge-coupons/tuning/tuning-plate.stl

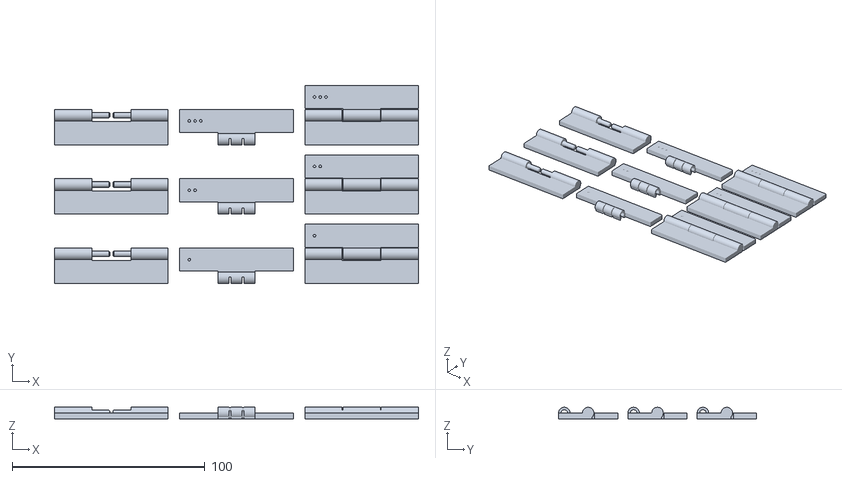
[picture p162: CAD file, 2026-09-26]
hinge-coupons/tuning/tuning-plate.stl
189.0 x 102.8 x 6.00
