Arcadesys/tak-box/home-board-compact-v1/models/grip-coupon-rear.step

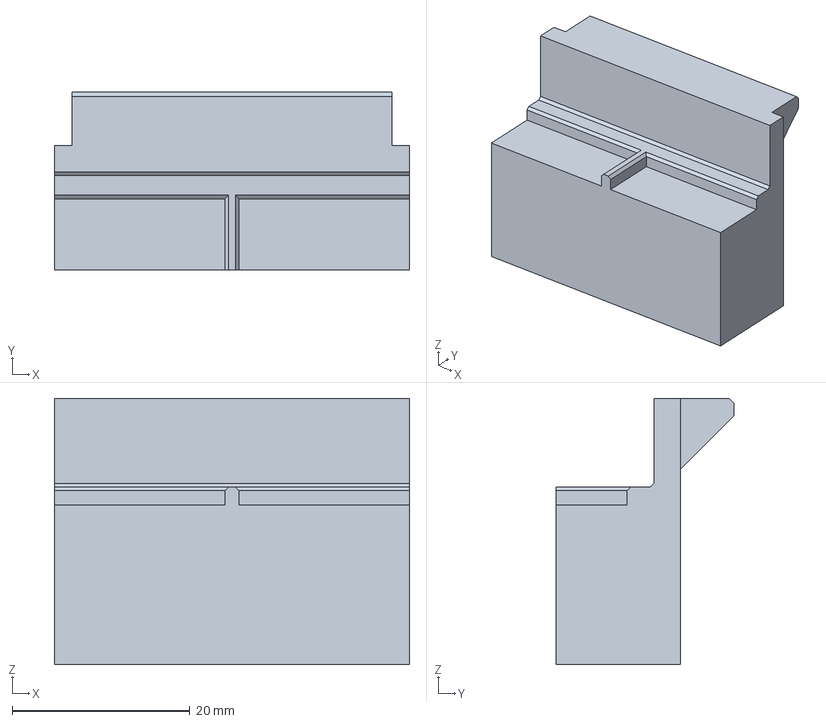
[picture p163: CAD file, 2026-10-09]
home-board-compact-v1/models/grip-coupon-rear.step
40.0 x 20.0 x 30.0 mm
