Arcadesys/tak-box/home-board-compact-v1/plates/platform.3mf

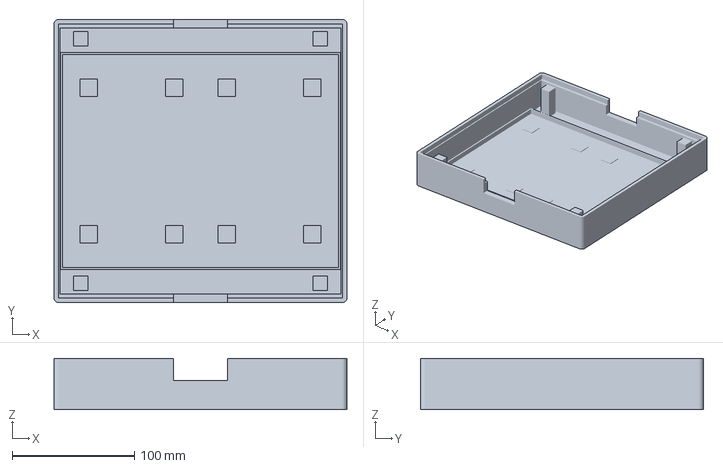
[picture p164: CAD file, 2026-10-09]
home-board-compact-v1/plates/platform.3mf
240.0 x 232.0 x 42.0 mm
