Arcadesys/tak-box/pieces/fox-cat-capstones-v4/models/cat-cc2-proof.3mf

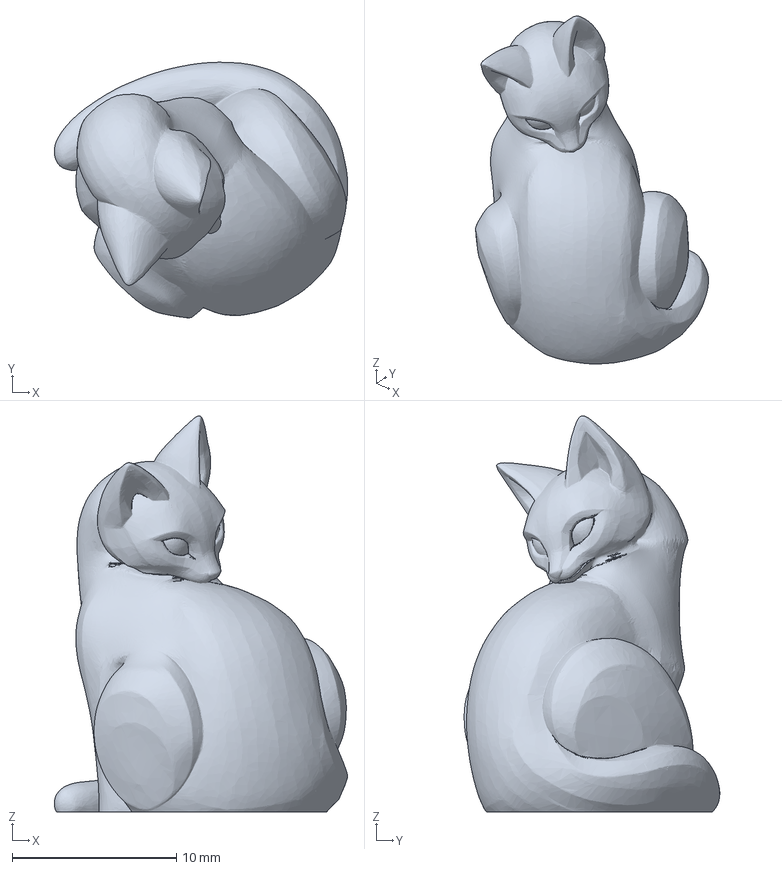
[picture p165: CAD file, 2026-09-30]
pieces/fox-cat-capstones-v4/models/cat-cc2-proof.3mf
17.8 x 15.5 x 24.1 mm
