Arcadesys/tak-box/pieces/fox-knurled-v1/models/fox-flat.step

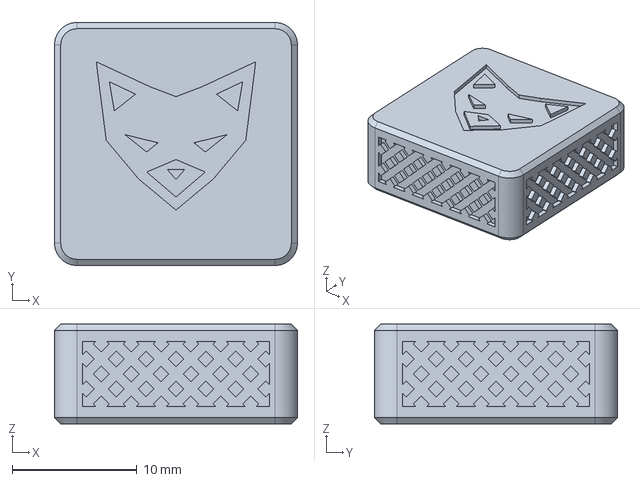
[picture p167: CAD file, 2026-09-30]
pieces/fox-knurled-v1/models/fox-flat.step
19.5 x 19.5 x 8.00 mm
