Arcadesys/tak-box/pieces/plates/tak-pieces-cc2-10-cat-orange.3mf

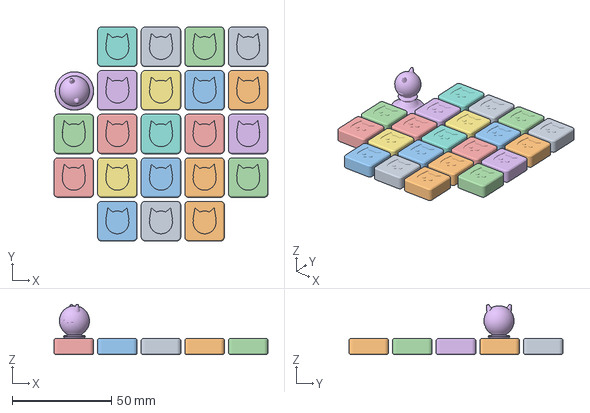
[picture p168: CAD file, 2026-09-26]
pieces/plates/tak-pieces-cc2-10-cat-orange.3mf
108.0 x 108.0 x 25.3 mm
cat-flat.stl x 21
cat-capstone.stl
