Arcadesys/tak-box/pieces/weighted-flat-capstones-v2/BLACK/PRINT/Tak-FOUR-PIECE-MIDPOINT-geometry.3mf

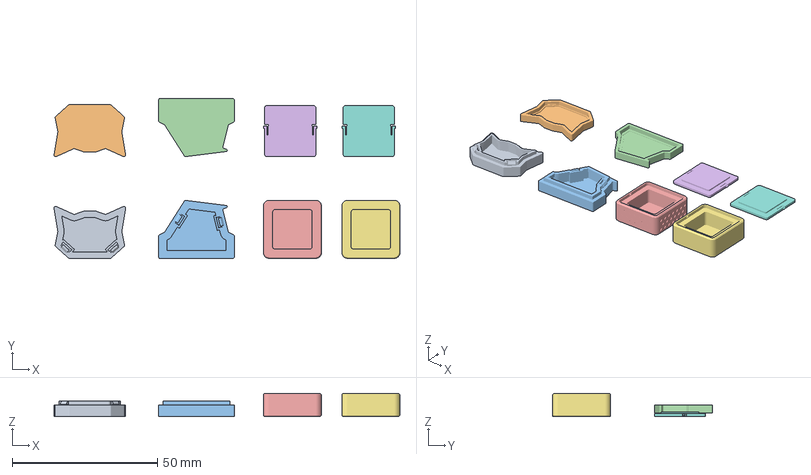
[picture p169: CAD file, 2026-10-09]
pieces/weighted-flat-capstones-v2/BLACK/PRINT/Tak-FOUR-PIECE-MIDPOINT-geometry.3mf
119.0 x 55.0 x 8.00 mm
SLOT 1 Cat capstone lower
SLOT 1 Cat capstone upper
SLOT 1 Witch capstone lower
SLOT 1 Witch capstone upper
SLOT 1 Cat regular body
SLOT 1 Cat regular floor
SLOT 1 Witch regular body
SLOT 1 Witch regular floor
