Arcadesys/tak-box/pieces/weighted-flat-capstones-v2/models/cat-capstone-upper.step

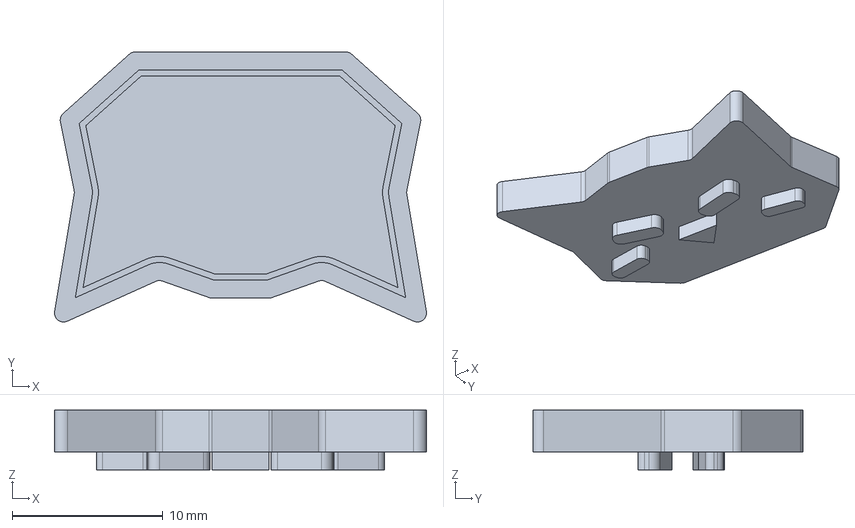
[picture p170: CAD file, 2026-10-09]
pieces/weighted-flat-capstones-v2/models/cat-capstone-upper.step
24.6 x 17.9 x 3.98 mm
