Arcadesys/tak-box/pieces/weighted-v1/models/coupon-floor-3.step

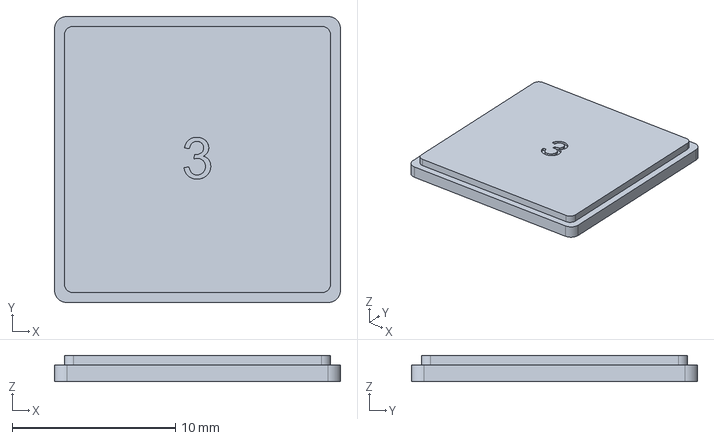
[picture p171: CAD file, 2026-09-30]
pieces/weighted-v1/models/coupon-floor-3.step
17.5 x 17.5 x 1.60 mm
