Arcadesys/tak-box/pieces/witch-print-plate.stl

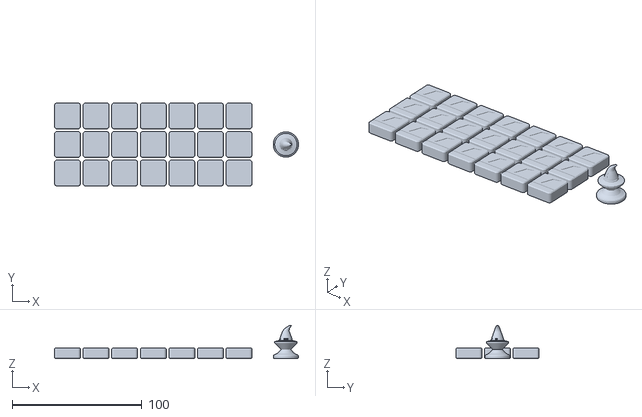
[picture p172: CAD file, 2026-09-26]
pieces/witch-print-plate.stl
187.7 x 64.0 x 25.4
