Arcadesys/tak-box/pin-board/black-grid-a.stl

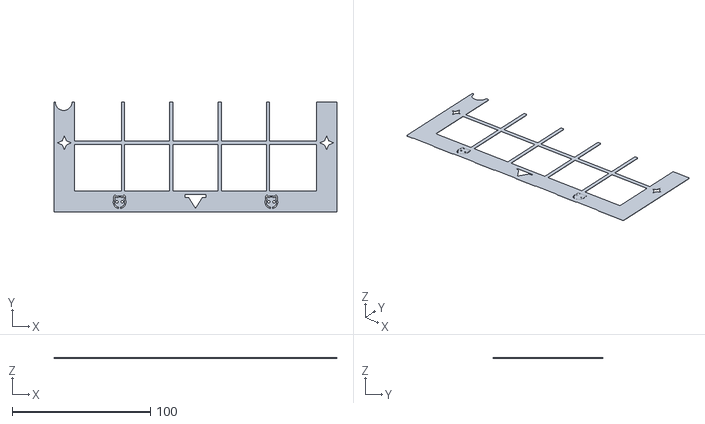
[picture p173: CAD file, 2026-09-26]
pin-board/black-grid-a.stl
205.0 x 79.5 x 0.8
