Arcadesys/tak-box/tak-v6-sketch-access.step

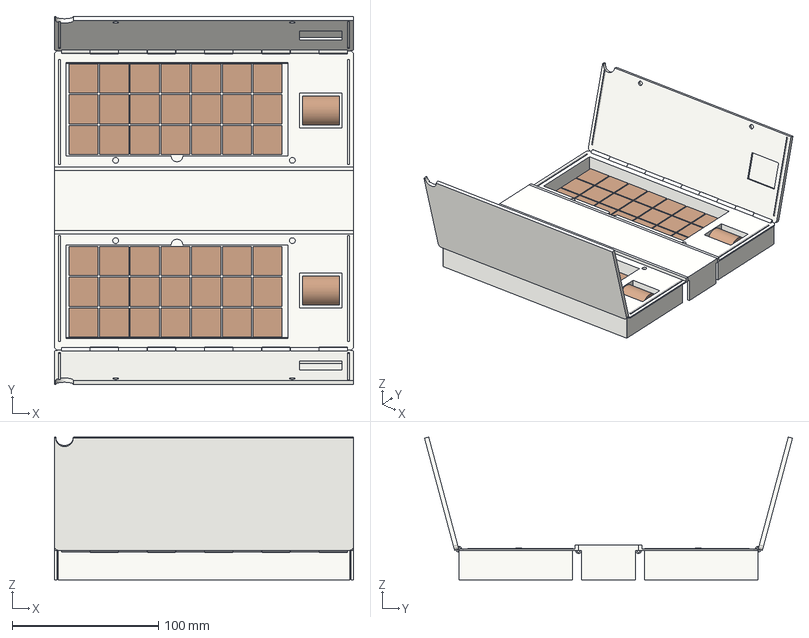
[picture p174: CAD file, 2026-09-26]
tak-v6-sketch-access.step
205.0 x 251.9 x 97.9 mm
wing shell 0
center row
wing shell 2
lid 0 open
lid 2 open
flat or keystone 0-0
flat or keystone 0-1
flat or keystone 0-2
flat or keystone 0-3
flat or keystone 0-4
flat or keystone 0-5
flat or keystone 0-6
flat or keystone 0-7
flat or keystone 0-8
flat or keystone 0-9
flat or keystone 0-10
flat or keystone 0-11
flat or keystone 0-12
flat or keystone 0-13
flat or keystone 0-14
flat or keystone 0-15
flat or keystone 0-16
flat or keystone 0-17
flat or keystone 0-18
flat or keystone 0-19
flat or keystone 0-20
flat or keystone 0-21
flat or keystone 1-0
flat or keystone 1-1
flat or keystone 1-2
flat or keystone 1-3
flat or keystone 1-4
flat or keystone 1-5
flat or keystone 1-6
flat or keystone 1-7
flat or keystone 1-8
flat or keystone 1-9
flat or keystone 1-10
flat or keystone 1-11
flat or keystone 1-12
flat or keystone 1-13
flat or keystone 1-14
flat or keystone 1-15
flat or keystone 1-16
flat or keystone 1-17
flat or keystone 1-18
flat or keystone 1-19
flat or keystone 1-20
flat or keystone 1-21
