Arcadesys/tak-box/v16-field-book/models/board-plate-b.purple.step

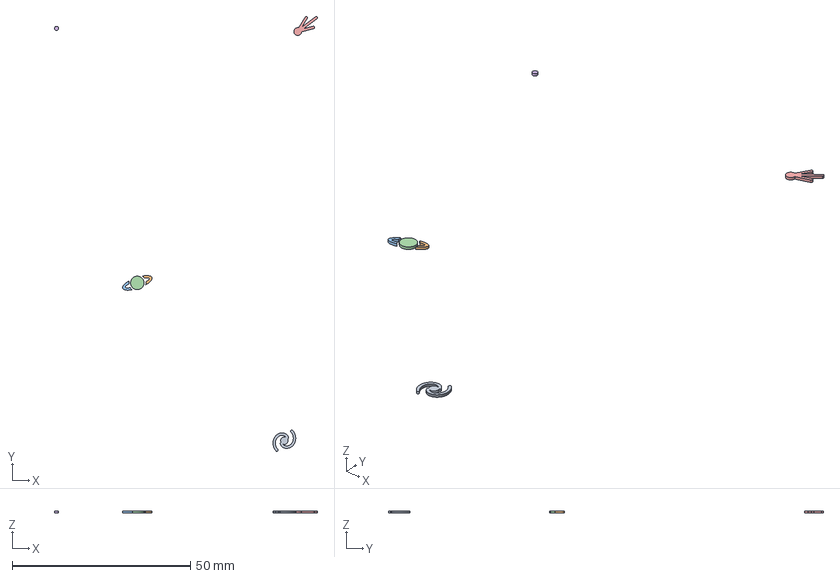
[picture p175: CAD file, 2026-09-30]
v16-field-book/models/board-plate-b.purple.step
73.8 x 122.0 x 0.6 mm
