Arcadesys/tak-box/v16-field-book/plates/plate04-tray-inserts-black.3mf

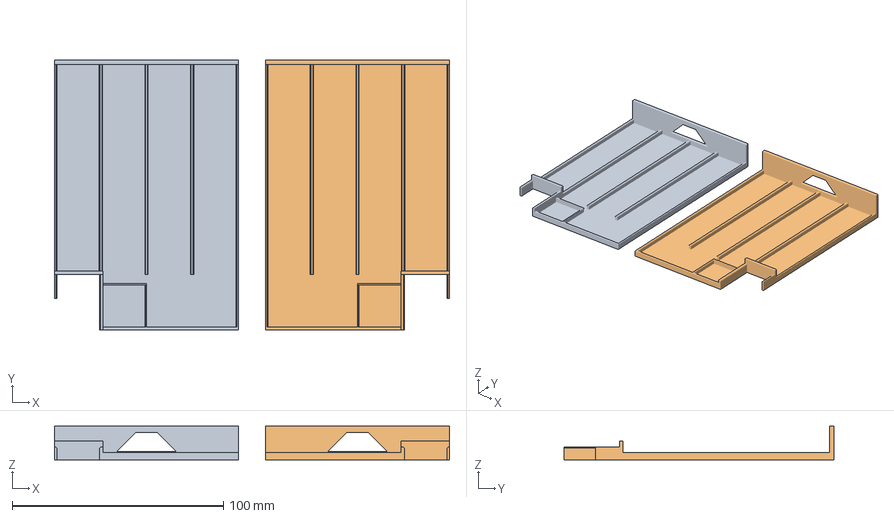
[picture p176: CAD file, 2026-09-30]
v16-field-book/plates/plate04-tray-inserts-black.3mf
187.2 x 127.8 x 16.0 mm
assemble_1
assemble_2
