Arcadesys/tak-box/v16-field-book/source/references/cat-flat.stl

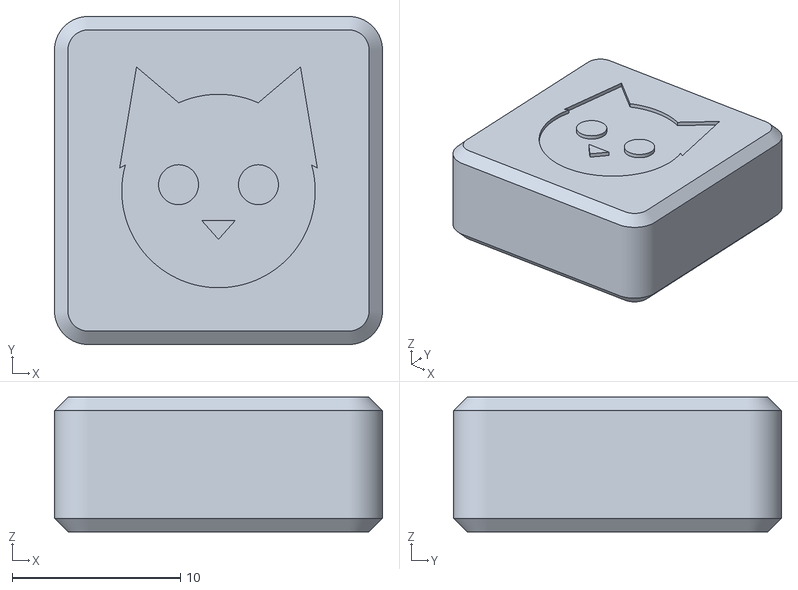
[picture p177: CAD file, 2026-09-29]
v16-field-book/source/references/cat-flat.stl
19.5 x 19.5 x 8.00
