Arcadesys/tak-box/v16-field-book/stl/full/tray-insert-b.stl

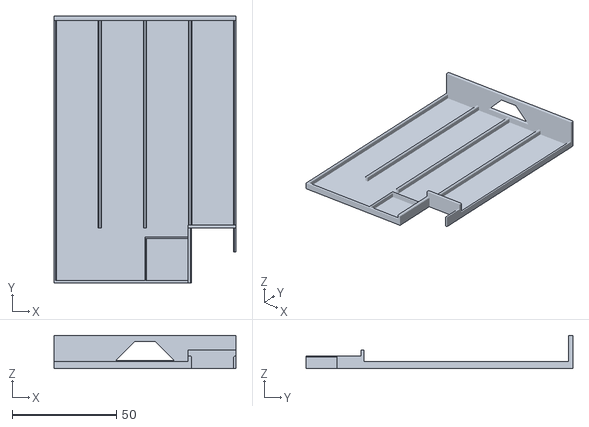
[picture p178: CAD file, 2026-09-30]
v16-field-book/stl/full/tray-insert-b.stl
87.2 x 127.8 x 16.0
