Arcadesys/tak-box/v16-field-book/stl/trials/trial-buckle-socket-base.stl

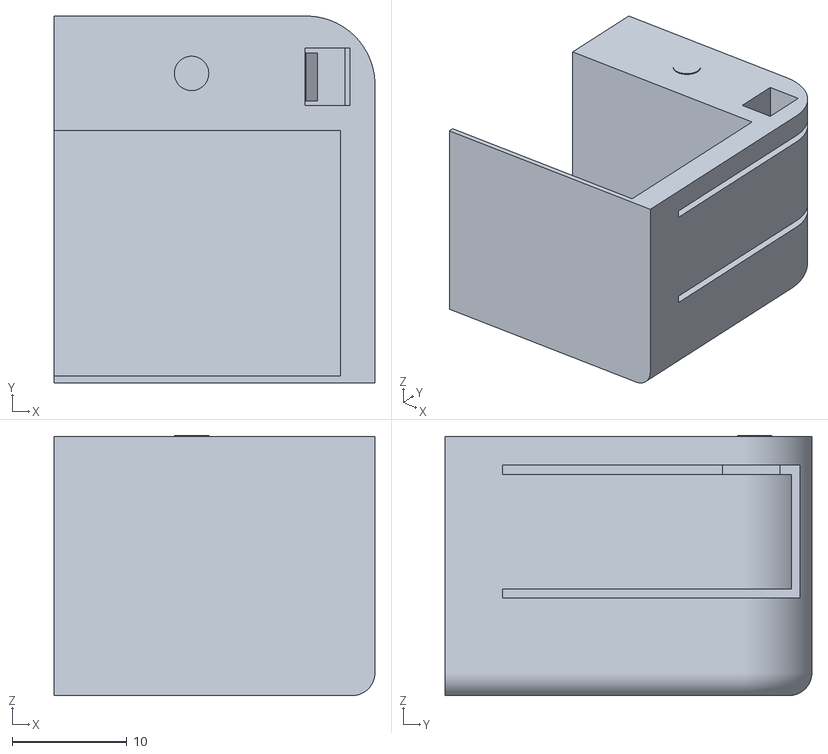
[picture p179: CAD file, 2026-09-30]
v16-field-book/stl/trials/trial-buckle-socket-base.stl
28.0 x 32.0 x 22.7
