Arcadesys/tak-box/v17-compact-folio/models/trial-lane-roof.step

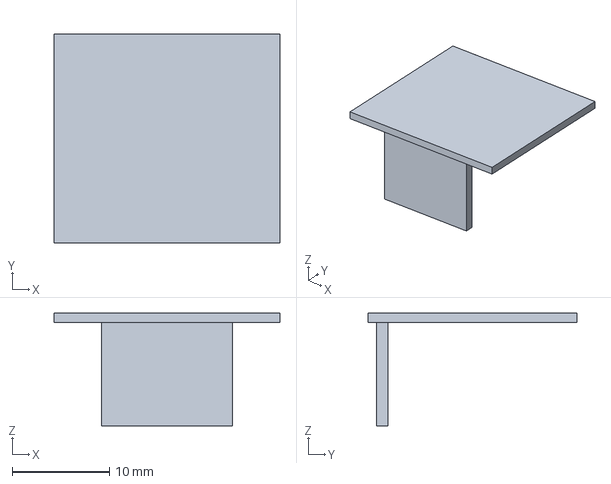
[picture p180: CAD file, 2026-10-05]
v17-compact-folio/models/trial-lane-roof.step
23.2 x 21.5 x 11.6 mm
