Arcadesys/tak-box/v17-compact-folio/plates/00-fit-trials.3mf

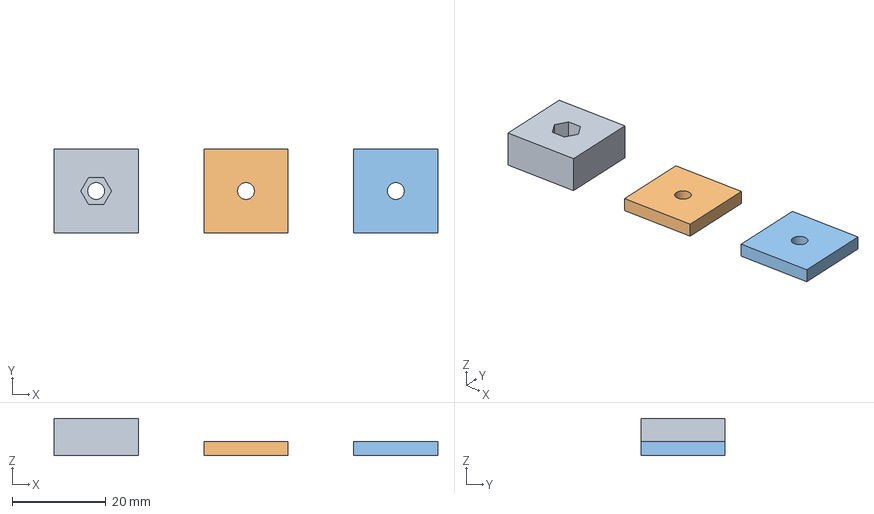
[picture p181: CAD file, 2026-10-05]
v17-compact-folio/plates/00-fit-trials.3mf
82.0 x 18.0 x 8.00 mm
trial-fastener-0
trial-fastener-1
trial-fastener-2
