Arcadesys/tak-box/v17-compact-folio/stl/trial-fastener-2.stl

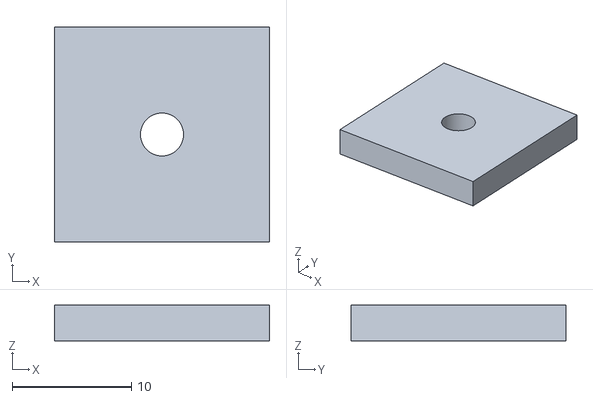
[picture p182: CAD file, 2026-10-05]
v17-compact-folio/stl/trial-fastener-2.stl
18.0 x 18.0 x 3.00
