Arcadesys/tak-box/v17-four-leaf/models/latch-keeper.step

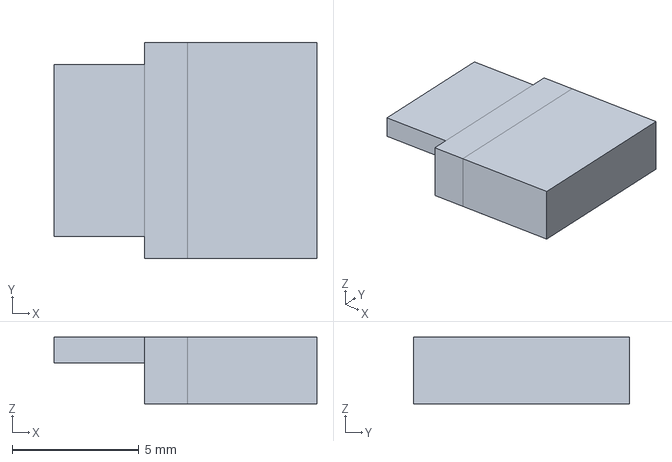
[picture p183: CAD file, 2026-10-05]
v17-four-leaf/models/latch-keeper.step
10.4 x 8.50 x 2.63 mm
