Arcadesys/tak-box/v17-four-leaf/plates/latch-lever.3mf

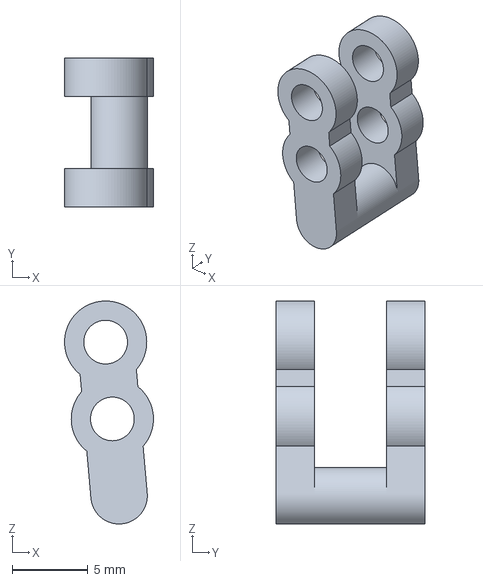
[picture p184: CAD file, 2026-10-05]
v17-four-leaf/plates/latch-lever.3mf
5.88 x 9.86 x 14.8 mm
