Arcadesys/tak-box/v17-squeeze-latch/models/A-squeeze-clip.step

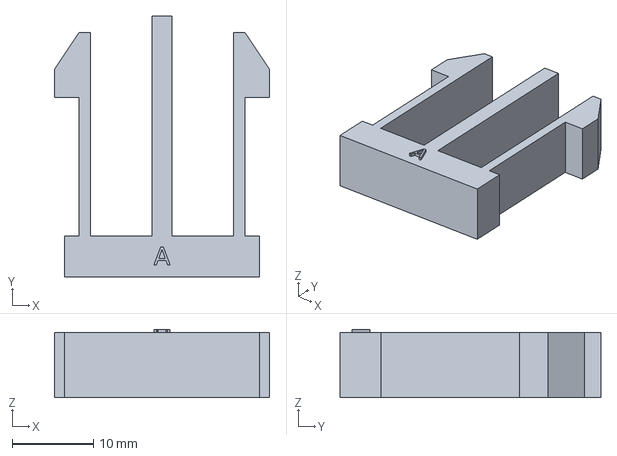
[picture p185: CAD file, 2026-10-05]
v17-squeeze-latch/models/A-squeeze-clip.step
26.4 x 32.0 x 8.40 mm
