Arcadesys/tak-box/v17-squeeze-latch/plates/v17-simple-squeeze-latch.3mf

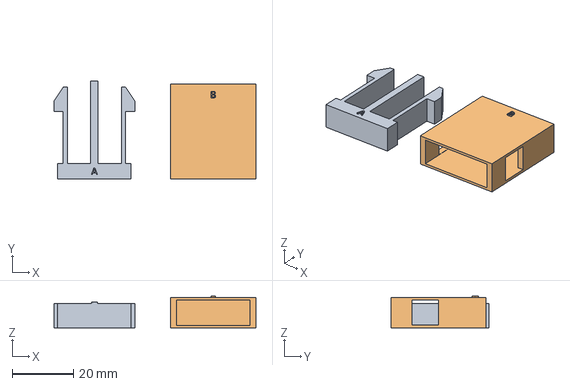
[picture p186: CAD file, 2026-10-05]
v17-squeeze-latch/plates/v17-simple-squeeze-latch.3mf
66.0 x 32.0 x 10.4 mm
A-squeeze-clip
B-socket
