Arcadesys/tak-box/v18-case/models/capstone-hatch.step

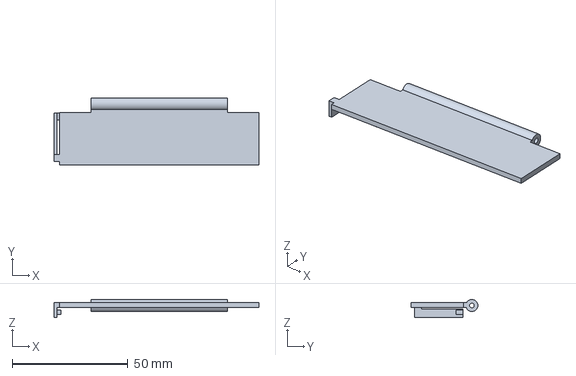
[picture p187: CAD file, 2026-10-09]
v18-case/models/capstone-hatch.step
88.7 x 28.9 x 7.80 mm
