Arcadesys/tak-box/v18-case/plates/03-board-leaves.3mf

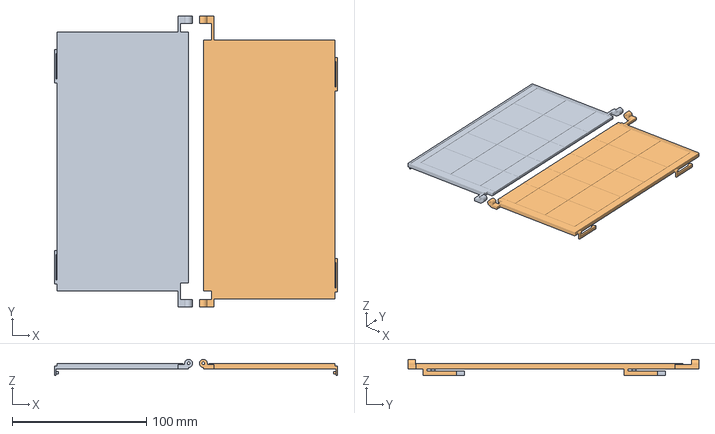
[picture p188: CAD file, 2026-10-09]
v18-case/plates/03-board-leaves.3mf
211.0 x 216.8 x 12.1 mm
board-left
board-right
