Arcadesys/tak-box/v18-recessed-clasp/plate/tak-v18-recessed-clasp.3mf

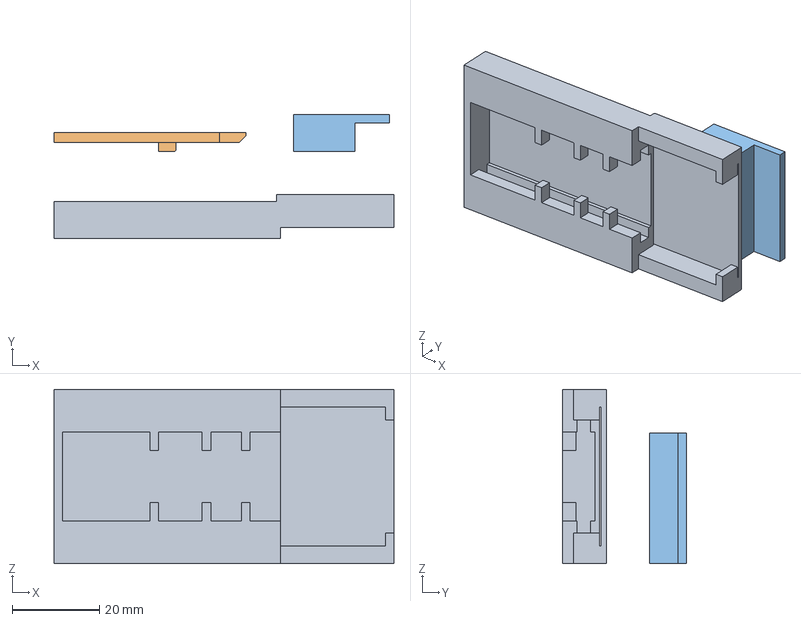
[picture p189: CAD file, 2026-10-09]
v18-recessed-clasp/plate/tak-v18-recessed-clasp.3mf
78.0 x 28.5 x 40.0 mm
V18-receiver
V18-slider
V18-keeper
