Arcadesys/tak-box/v18-recessed-clasp/states/02-pressed/slider.stl

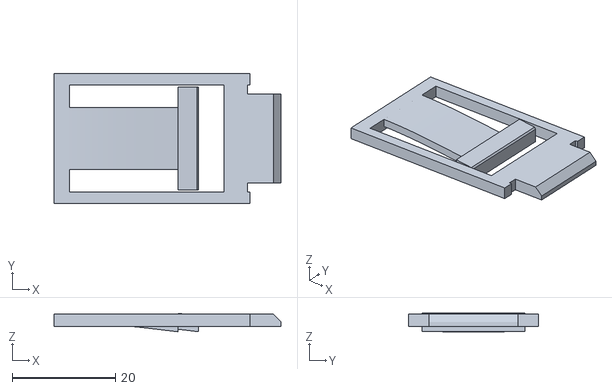
[picture p190: CAD file, 2026-10-09]
v18-recessed-clasp/states/02-pressed/slider.stl
44.0 x 25.2 x 3.60
