Arcadesys/tak-box/v23-r2/FIT-CHECK/hinge-left.step

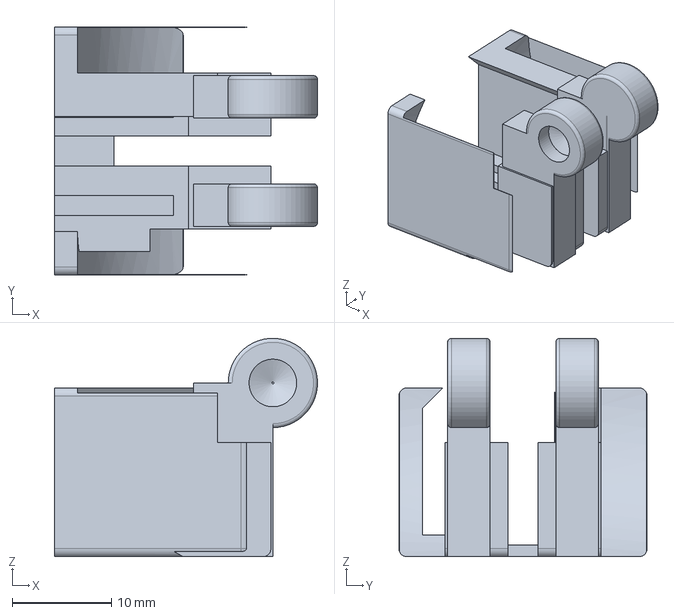
[picture p191: CAD file, 2026-10-09]
v23-r2/FIT-CHECK/hinge-left.step
26.5 x 25.0 x 22.0 mm
