Arcadesys/tak-box/v23-r2/plates/03-removable-player-trays.3mf

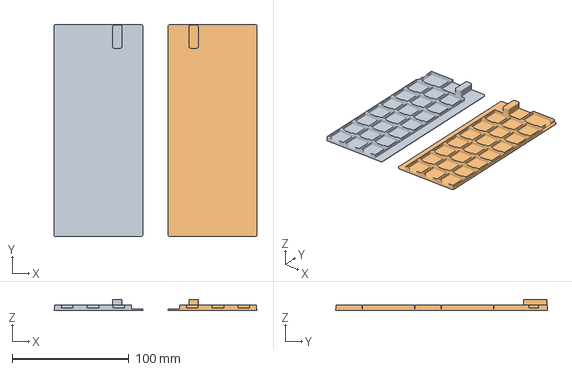
[picture p192: CAD file, 2026-10-09]
v23-r2/plates/03-removable-player-trays.3mf
174.2 x 182.1 x 9.20 mm
tray-left
tray-right
