Arcadesys/tak-box/v23-r2/PRINT/04-flat-capstones-hook-and-collar-CC2-PLA.3mf

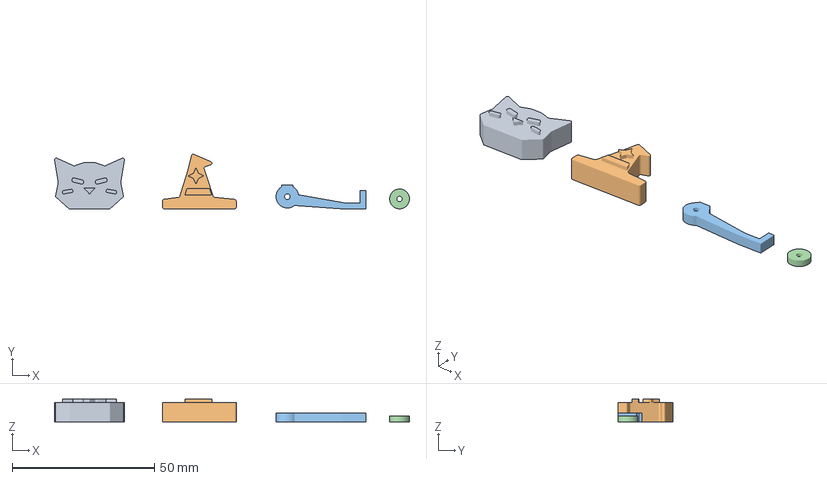
[picture p193: CAD file, 2026-10-09]
v23-r2/PRINT/04-flat-capstones-hook-and-collar-CC2-PLA.3mf
125.0 x 19.3 x 8.00 mm
capstone-cat
capstone-witch
side-hook
axle-end-cap
