Arcadesys/tak-box/v23-r2/TRAY-FIT/removable-tray-access-trial-CC2-PLA.3mf

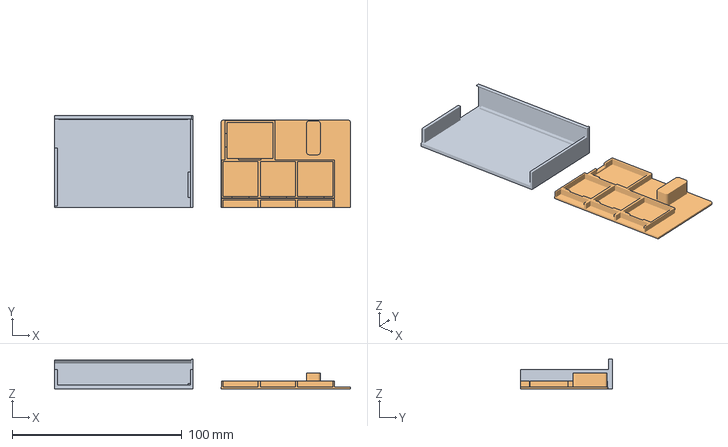
[picture p194: CAD file, 2026-10-09]
v23-r2/TRAY-FIT/removable-tray-access-trial-CC2-PLA.3mf
174.2 x 54.1 x 17.5 mm
seat-section
tray-section
