Arcadesys/tak-box/v26/models/board-reference-left.step

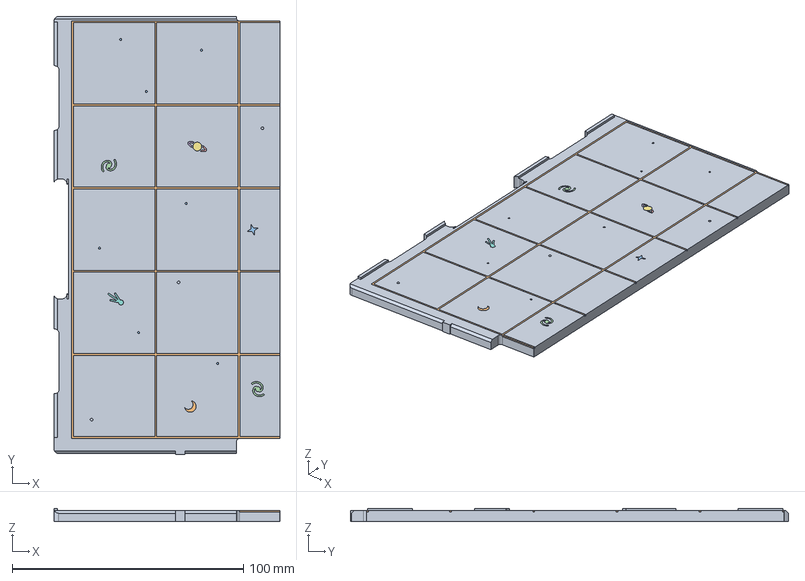
[picture p195: CAD file, 2026-10-09]
v26/models/board-reference-left.step
97.8 x 189.6 x 5.70 mm
