Arcadesys/tak-box/v26/plates/01-V26-captive-hook-trial.3mf

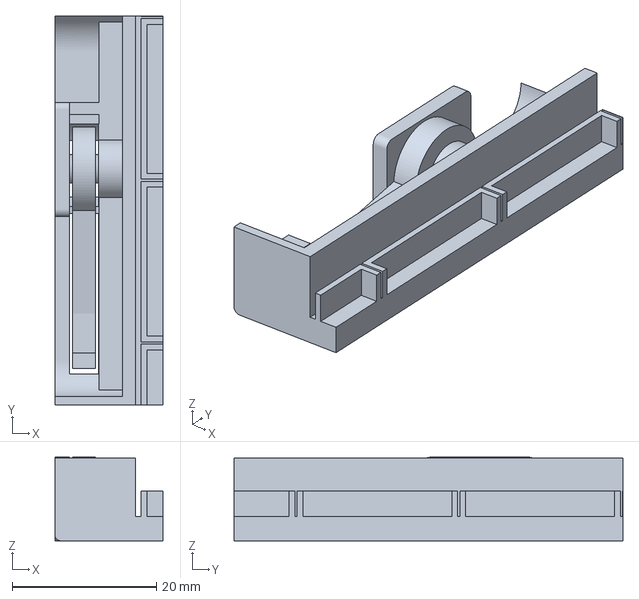
[picture p196: CAD file, 2026-10-09]
v26/plates/01-V26-captive-hook-trial.3mf
15.0 x 54.0 x 11.6 mm
