Arcadesys/tak-box/v26/reference/board-inlays/board-left-purple.step

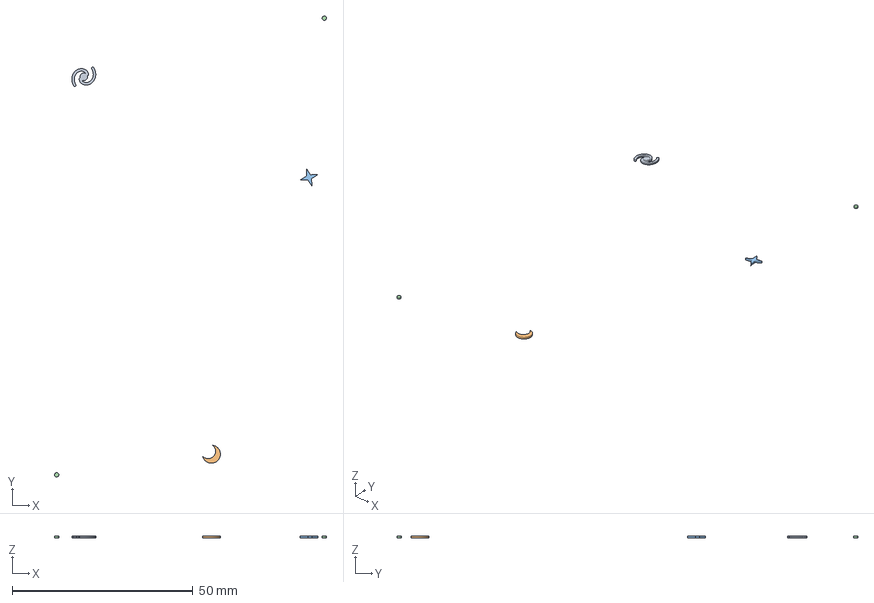
[picture p197: CAD file, 2026-10-09]
v26/reference/board-inlays/board-left-purple.step
75.1 x 127.3 x 0.6 mm
