Arcadesys/tak-box/v26/reference/plain-bodies/housing-design-left.step

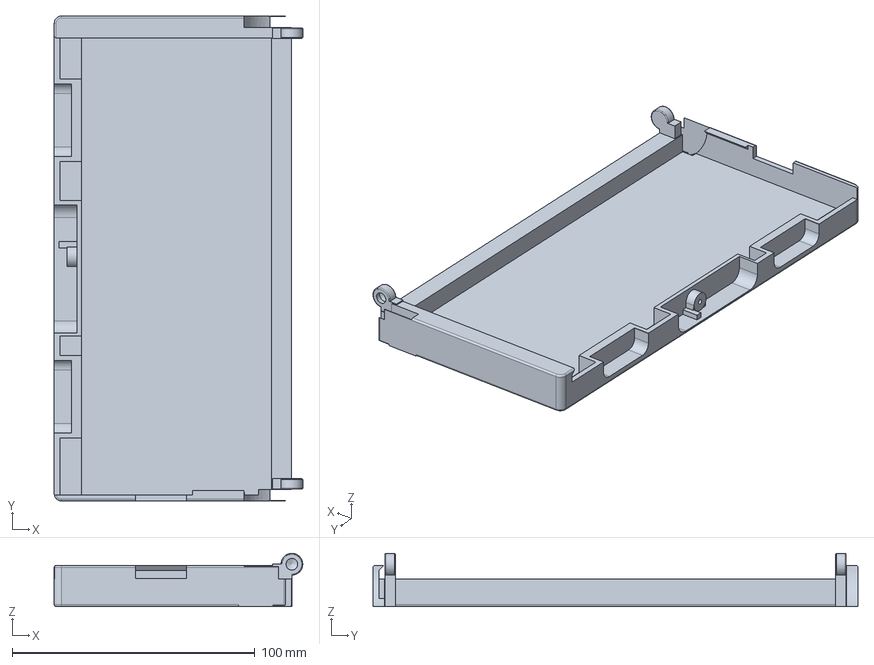
[picture p198: CAD file, 2026-10-09]
v26/reference/plain-bodies/housing-design-left.step
102.5 x 200.0 x 22.0 mm
