Arcadesys/tak-box/v26/SMALL-TRIALS/03-V26-combined-mechanism-trials-CC2-PLA.3mf

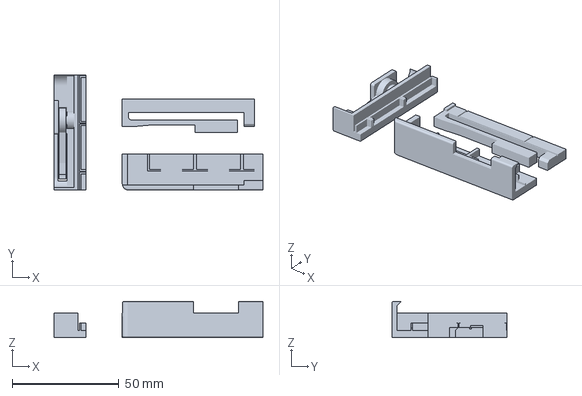
[picture p199: CAD file, 2026-10-09]
v26/SMALL-TRIALS/03-V26-combined-mechanism-trials-CC2-PLA.3mf
98.0 x 54.0 x 17.0 mm
