Arcadesys/tak-box/centauri-carbon-2-3mf/tak-pin-board-cc2-82-white-wing-b-lid-b.3mf

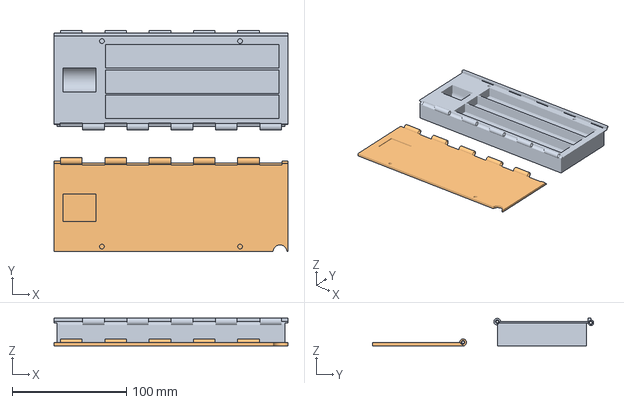
[picture p200: CAD file, 2026-09-26]
centauri-carbon-2-3mf/tak-pin-board-cc2-82-white-wing-b-lid-b.3mf
205.0 x 194.0 x 24.1 mm
wing-b.stl
lid-b.stl
