Arcadesys/tak-box/center-closure-coupon/coupon-lid-0.stl

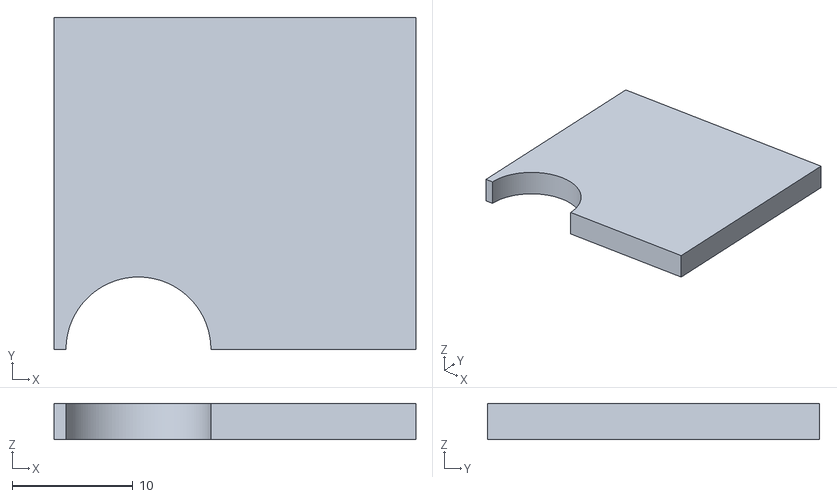
[picture p201: CAD file, 2026-09-27]
center-closure-coupon/coupon-lid-0.stl
30.0 x 27.5 x 3.00
