Arcadesys/tak-box/center-closure-v7/coupon-wing-0.stl

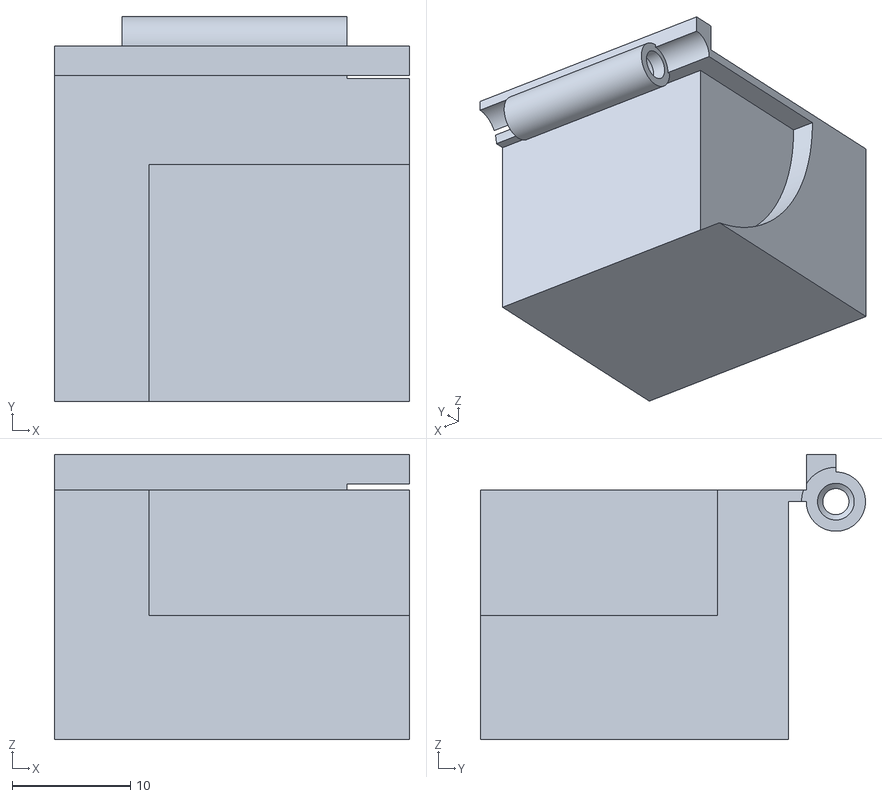
[picture p202: CAD file, 2026-09-27]
center-closure-v7/coupon-wing-0.stl
30.0 x 32.5 x 24.1
