Arcadesys/tak-box/fit-coupon/well-end-shell.stl

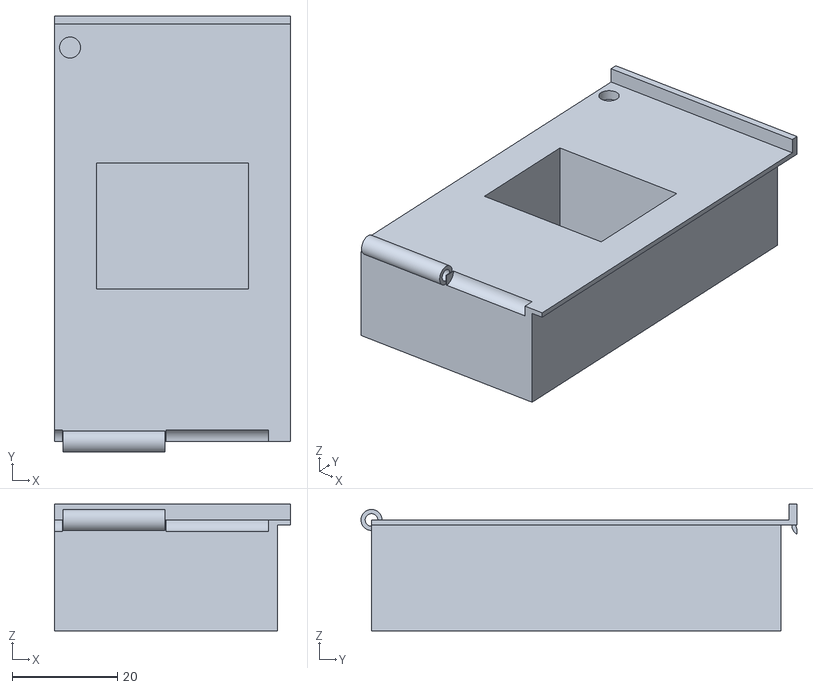
[picture p203: CAD file, 2026-09-25]
fit-coupon/well-end-shell.stl
45.0 x 83.0 x 24.1
