Arcadesys/tak-box/full-size-pagoda-v1/models/fox-capstone.stl

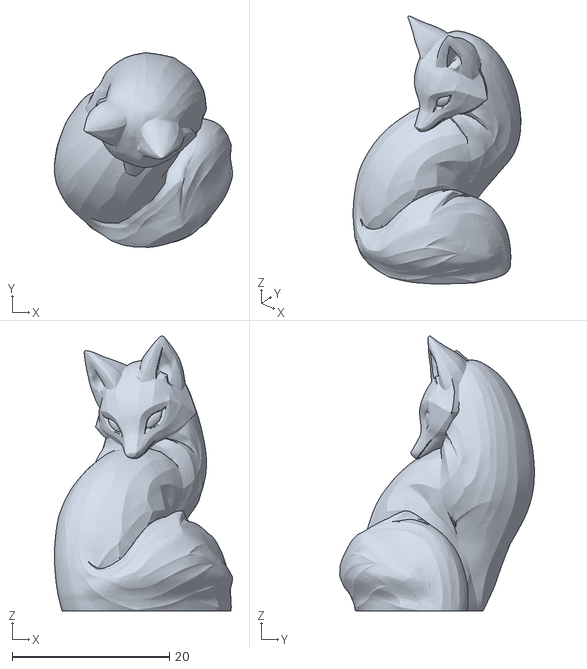
[picture p204: CAD file, 2026-10-03]
full-size-pagoda-v1/models/fox-capstone.stl
22.7 x 24.8 x 35.0
