Arcadesys/tak-box/full-size-pagoda-v1/plates/closure-coupon.3mf

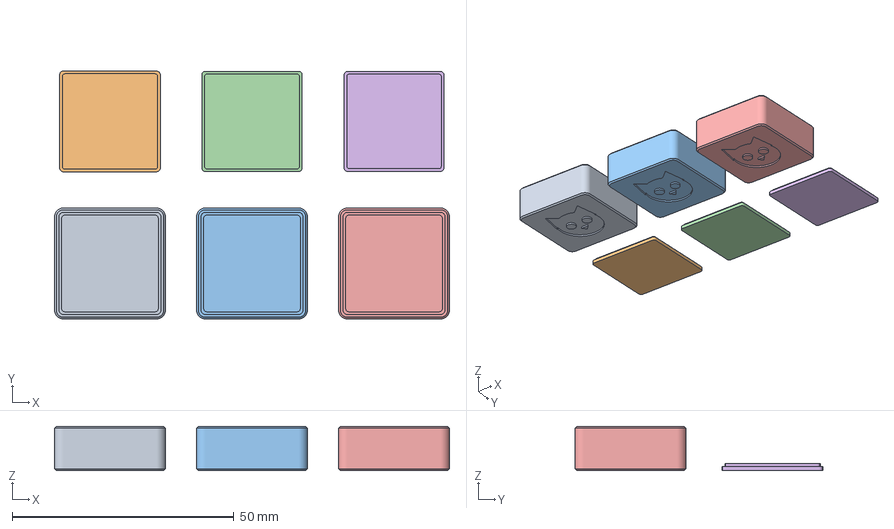
[picture p205: CAD file, 2026-10-03]
full-size-pagoda-v1/plates/closure-coupon.3mf
89.0 x 55.9 x 10.0 mm
01-cat-body-15
02-floor-clearance-15
03-cat-body-20
04-floor-clearance-20
05-cat-body-25
06-floor-clearance-25
