Arcadesys/tak-box/halves/half-B.stl

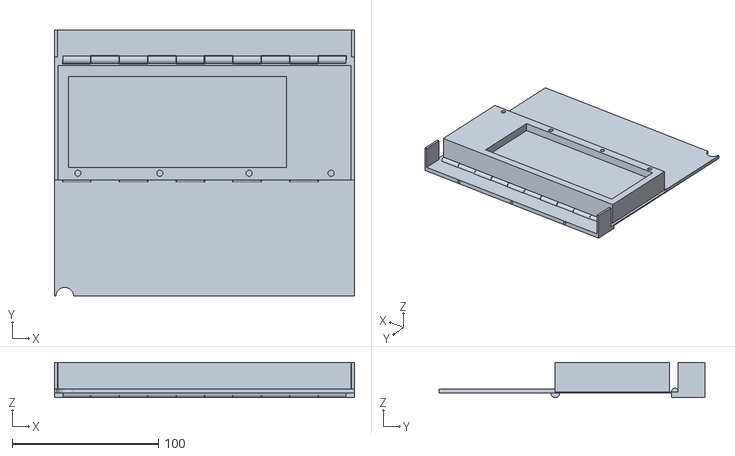
[picture p206: CAD file, 2026-09-26]
halves/half-B.stl
205.0 x 182.0 x 24.1
