Arcadesys/tak-box/hinge-coupons/case/frame-slice.stl

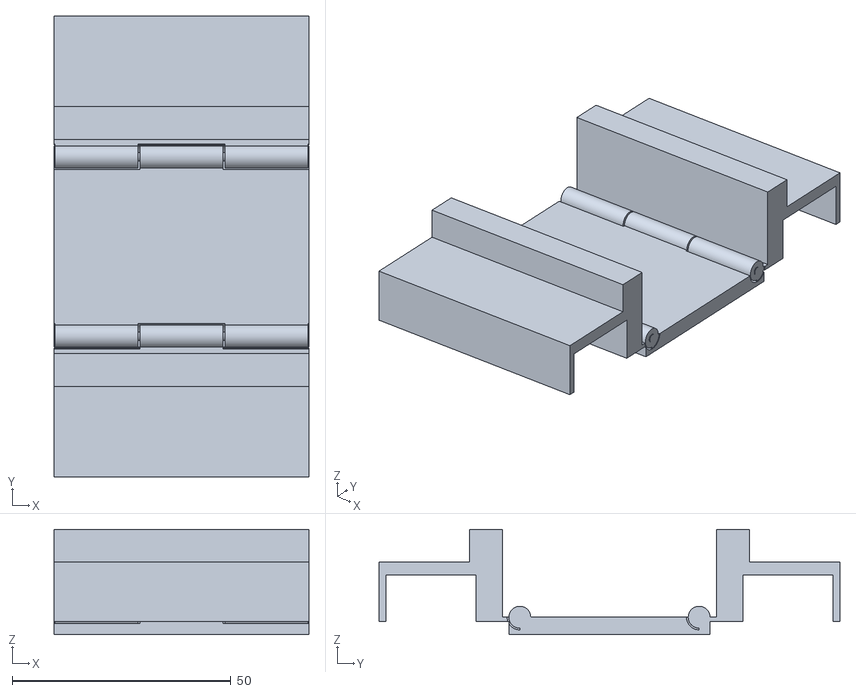
[picture p207: CAD file, 2026-09-26]
hinge-coupons/case/frame-slice.stl
58.2 x 105.4 x 24.1
