Arcadesys/tak-box/hinge-coupons/joint/piece-A.stl

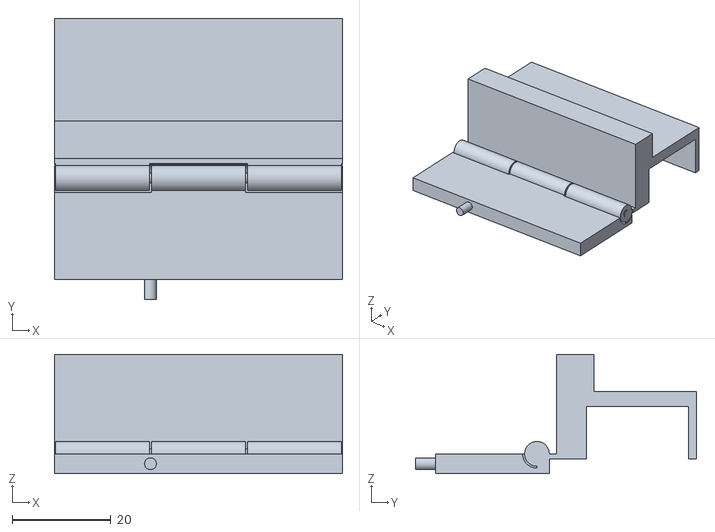
[picture p208: CAD file, 2026-09-26]
hinge-coupons/joint/piece-A.stl
58.2 x 56.7 x 24.1
