Arcadesys/tak-box/home-board-compact-v1/models/grip-coupon-front.step

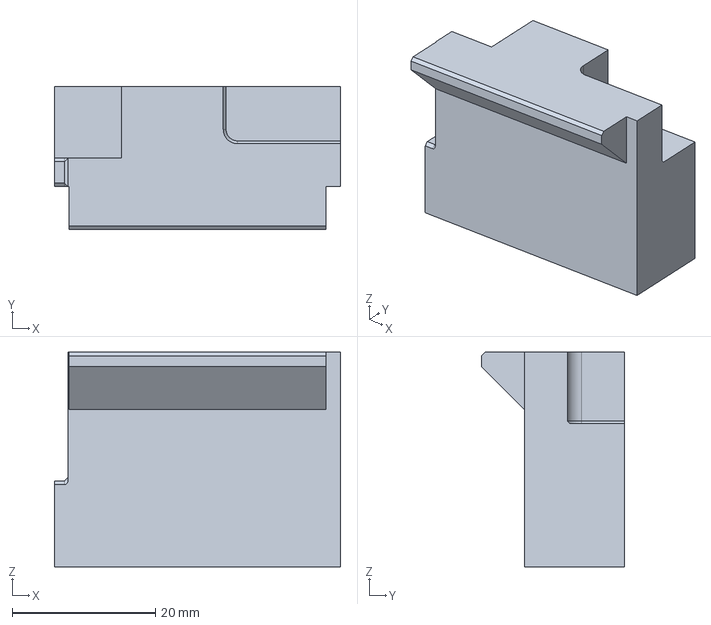
[picture p209: CAD file, 2026-10-09]
home-board-compact-v1/models/grip-coupon-front.step
40.0 x 20.0 x 30.0 mm
