Arcadesys/tak-box/home-board-compact-v1/plates/tray.3mf

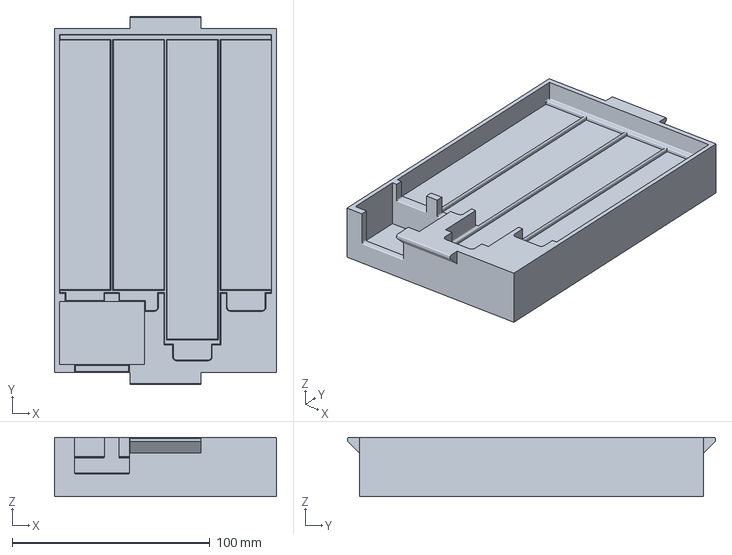
[picture p210: CAD file, 2026-10-09]
home-board-compact-v1/plates/tray.3mf
112.2 x 186.0 x 30.0 mm
