Arcadesys/tak-box/pieces/fox-cat-capstones-v4/models/fox-capstone.stl

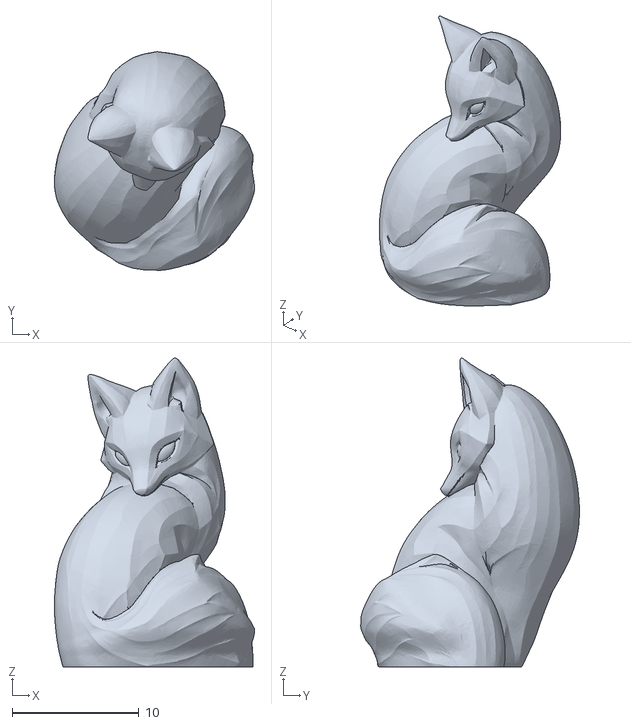
[picture p211: CAD file, 2026-09-30]
pieces/fox-cat-capstones-v4/models/fox-capstone.stl
15.8 x 17.3 x 24.4
