Arcadesys/tak-box/pieces/fox-cat-capstones-v4/raw/cat.obj

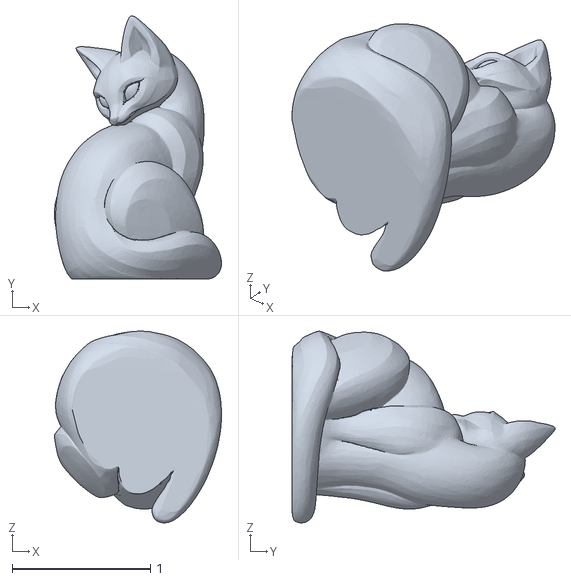
[picture p212: CAD file, 2026-09-30]
pieces/fox-cat-capstones-v4/raw/cat.obj
1.21 x 1.90 x 1.39
