Arcadesys/tak-box/pieces/fox-knurled-v1/plates/fox-21-flats.3mf

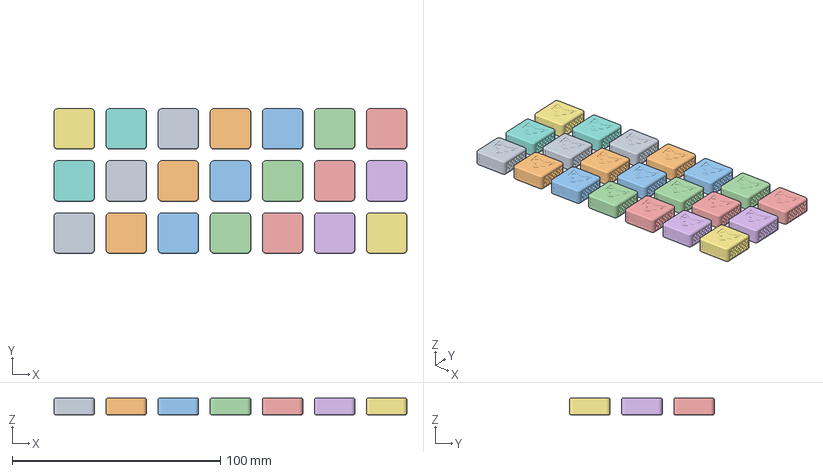
[picture p213: CAD file, 2026-09-30]
pieces/fox-knurled-v1/plates/fox-21-flats.3mf
169.5 x 69.5 x 8.00 mm
fox-flat-01
fox-flat-02
fox-flat-03
fox-flat-04
fox-flat-05
fox-flat-06
fox-flat-07
fox-flat-08
fox-flat-09
fox-flat-10
fox-flat-11
fox-flat-12
fox-flat-13
fox-flat-14
fox-flat-15
fox-flat-16
fox-flat-17
fox-flat-18
fox-flat-19
fox-flat-20
fox-flat-21
