Arcadesys/tak-box/pieces/weighted-flat-capstones-v2/models/cat-regular-floor.step

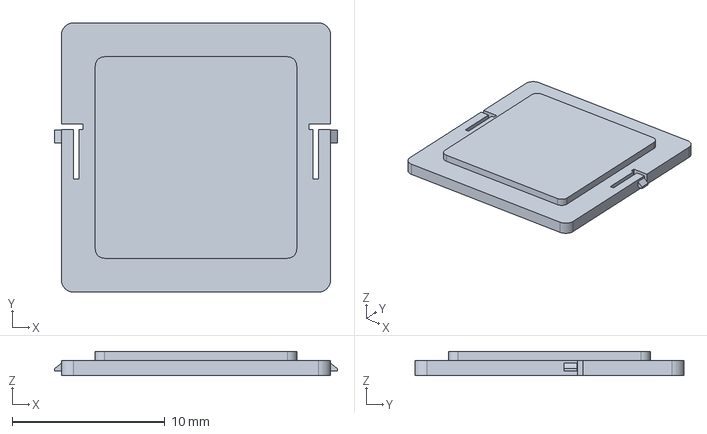
[picture p214: CAD file, 2026-10-09]
pieces/weighted-flat-capstones-v2/models/cat-regular-floor.step
18.5 x 17.6 x 1.60 mm
