Arcadesys/tak-box/pieces/weighted-v1/models/cat-capstone.step

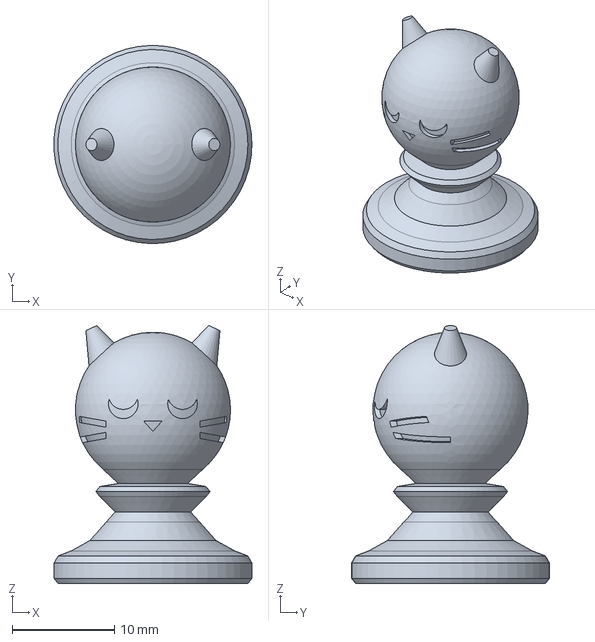
[picture p215: CAD file, 2026-09-30]
pieces/weighted-v1/models/cat-capstone.step
19.4 x 19.4 x 25.3 mm
