Arcadesys/tak-box/pieces/weighted-v1/plates/fit-coupon-first.3mf

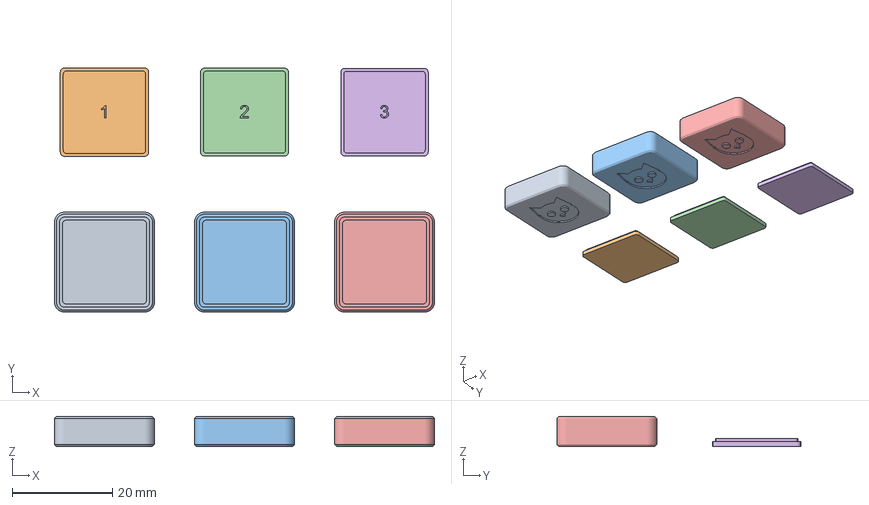
[picture p216: CAD file, 2026-09-30]
pieces/weighted-v1/plates/fit-coupon-first.3mf
76.0 x 48.9 x 6.00 mm
01-body-for-floor-1
02-floor-1-0.15mm
03-body-for-floor-2
04-floor-2-0.20mm
05-body-for-floor-3
06-floor-3-0.25mm
