Arcadesys/tak-box/pin-board/center-row.stl

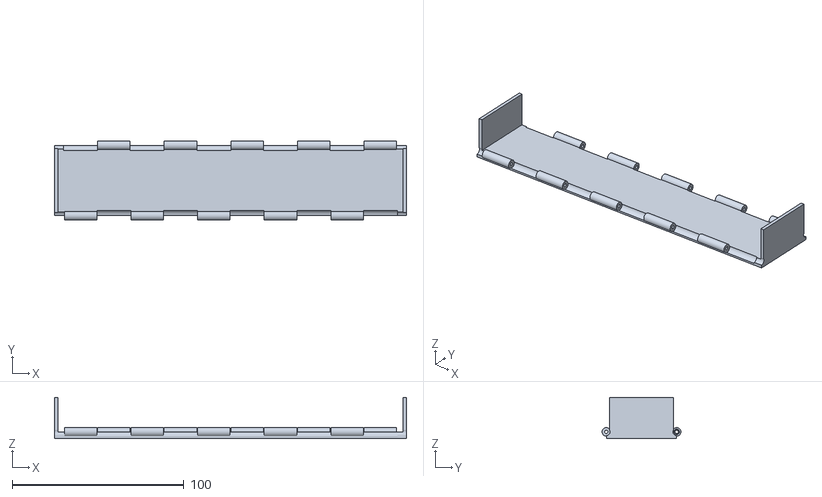
[picture p217: CAD file, 2026-09-26]
pin-board/center-row.stl
205.0 x 46.0 x 24.1
