Arcadesys/tak-box/tak-open-wells-v5-play.step

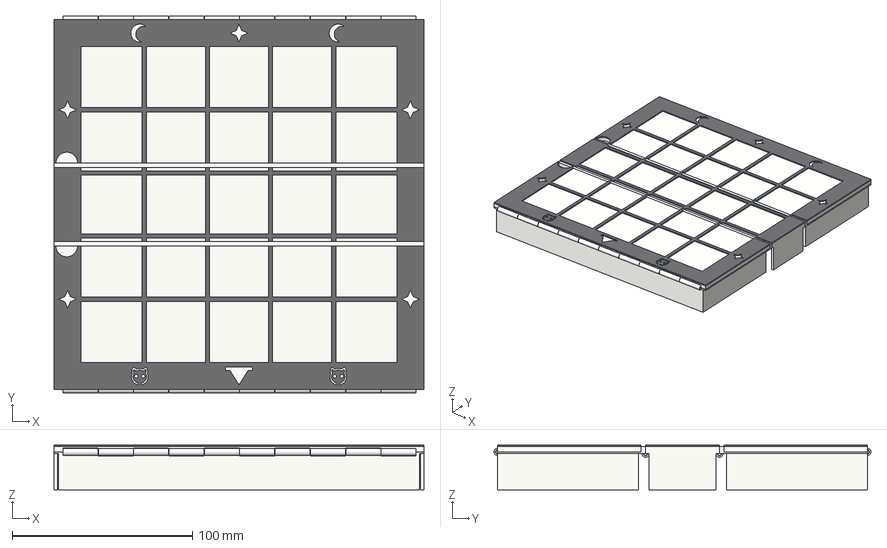
[picture p218: CAD file, 2026-09-25]
tak-open-wells-v5-play.step
205.0 x 209.0 x 24.9 mm
wing shell 0
wing shell 1
wing shell 2
playing lid 0
playing lid 2
black grid 0
black grid 1
black grid 2
main pin 0
main pin 1
lid pin 0
lid pin 1
