Arcadesys/tak-box/v16-field-book/plates/plate01-hinged-bases-black.3mf

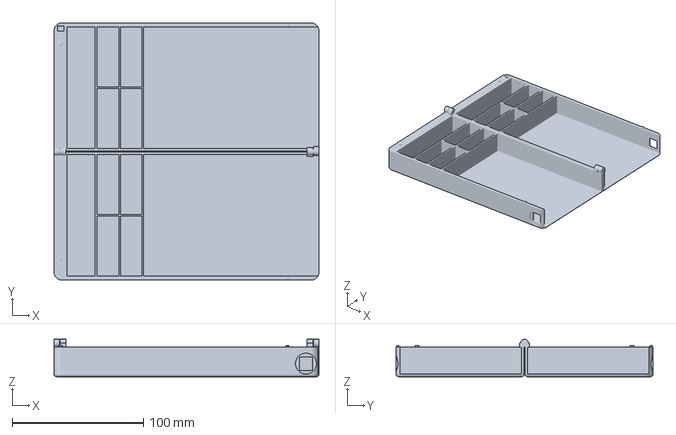
[picture p219: CAD file, 2026-09-30]
v16-field-book/plates/plate01-hinged-bases-black.3mf
202.0 x 196.0 x 28.6 mm
