Arcadesys/tak-box/v16-field-book/source/references/witch-capstone.stl

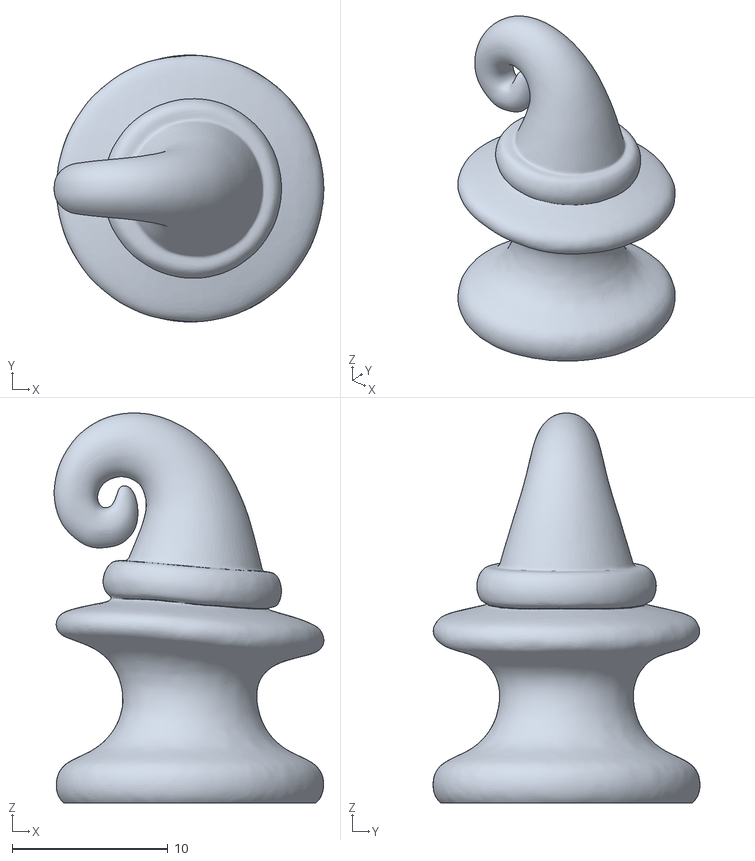
[picture p220: CAD file, 2026-09-29]
v16-field-book/source/references/witch-capstone.stl
17.3 x 17.1 x 25.0
