Arcadesys/tak-box/v16-field-book/stl/trials/trial-hinge-pair.stl

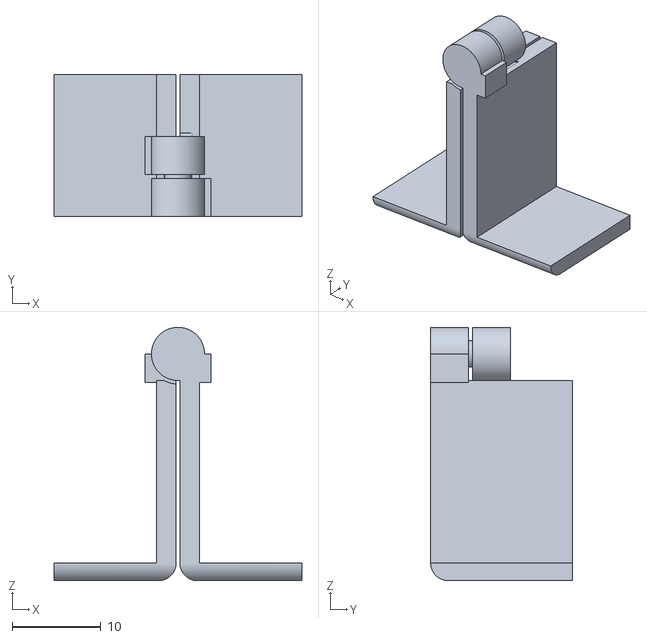
[picture p221: CAD file, 2026-09-29]
v16-field-book/stl/trials/trial-hinge-pair.stl
28.0 x 16.0 x 28.6
