Arcadesys/tak-box/v17-compact-folio/models/trial-lane.step

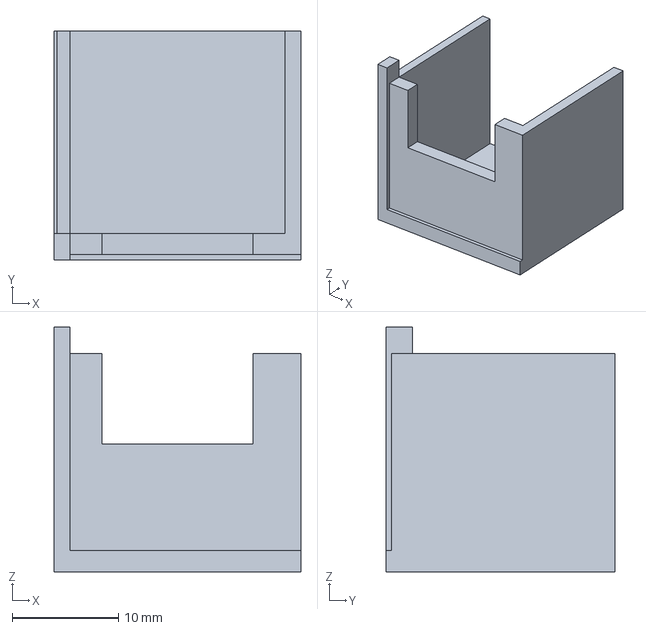
[picture p222: CAD file, 2026-10-05]
v17-compact-folio/models/trial-lane.step
23.2 x 21.5 x 23.0 mm
