Arcadesys/tak-box/v17-compact-folio/plates/01-shell-and-roof.3mf

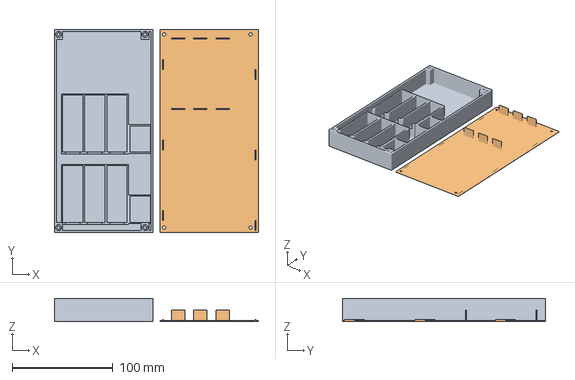
[picture p223: CAD file, 2026-10-05]
v17-compact-folio/plates/01-shell-and-roof.3mf
202.8 x 202.0 x 23.0 mm
roof
