Arcadesys/tak-box/v17-four-leaf/models/latch-mount.step

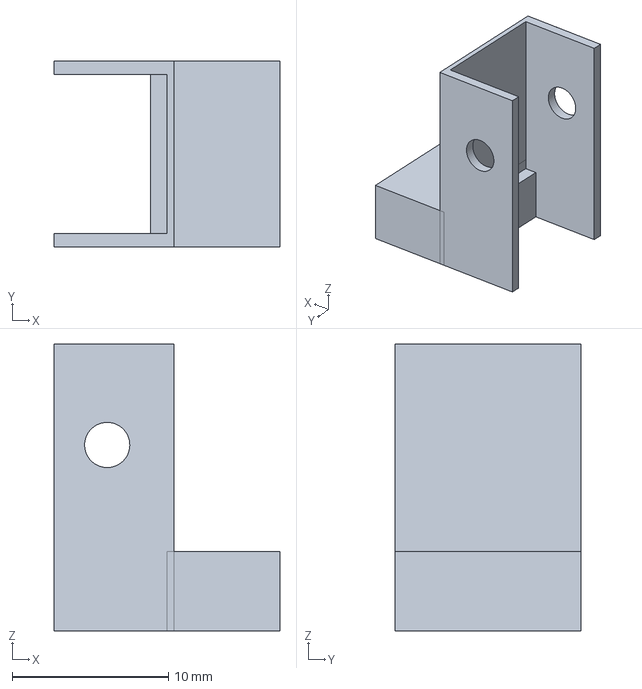
[picture p224: CAD file, 2026-10-05]
v17-four-leaf/models/latch-mount.step
14.4 x 11.9 x 18.4 mm
