Arcadesys/tak-box/v17-four-leaf/plates/latch-hook.3mf

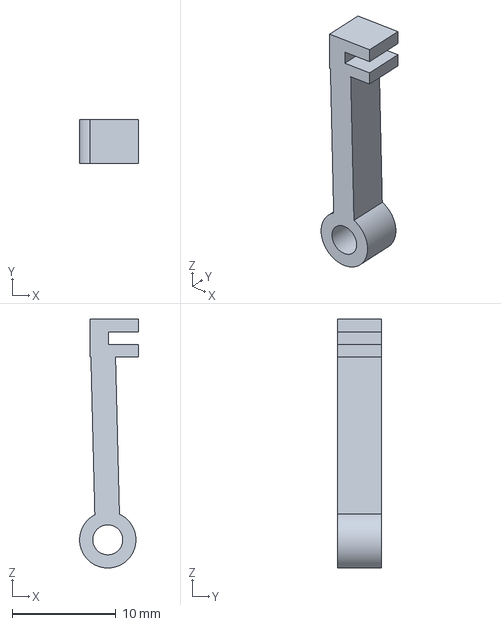
[picture p225: CAD file, 2026-10-05]
v17-four-leaf/plates/latch-hook.3mf
5.67 x 4.25 x 24.0 mm
