Arcadesys/tak-box/v17-squeeze-latch/models/B-socket.step

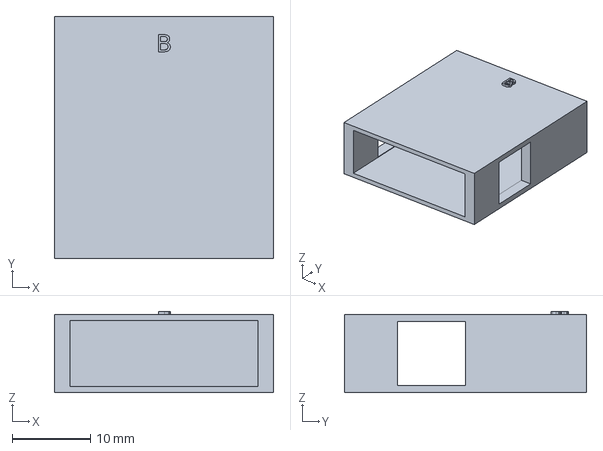
[picture p226: CAD file, 2026-10-05]
v17-squeeze-latch/models/B-socket.step
28.0 x 31.0 x 10.4 mm
