Arcadesys/tak-box/v18-case/plates/04-piece-drawers-CC2-PLA.3mf

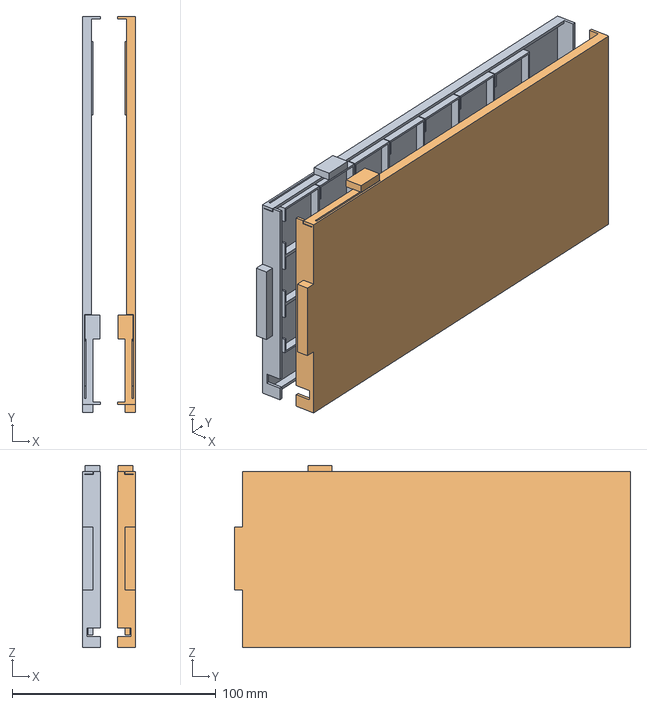
[picture p227: CAD file, 2026-10-09]
v18-case/plates/04-piece-drawers-CC2-PLA.3mf
25.8 x 194.4 x 89.3 mm
drawer-left
drawer-right
