Arcadesys/tak-box/v23-r2/FIT-CHECK/captive-hinge-fit-check-geometry.3mf

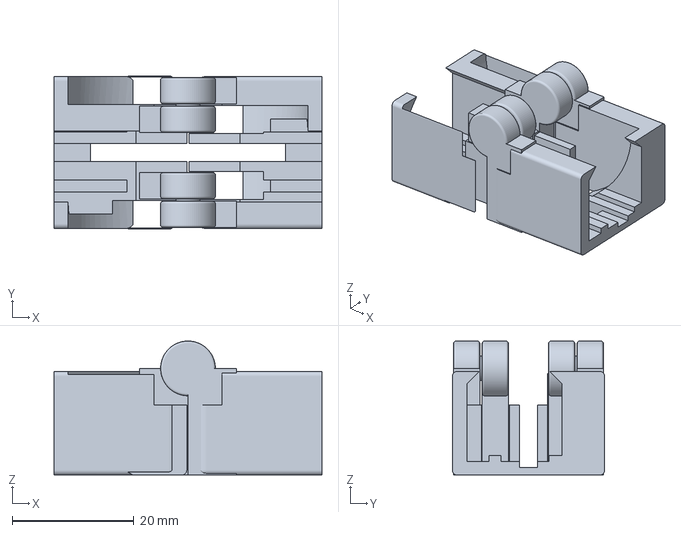
[picture p228: CAD file, 2026-10-09]
v23-r2/FIT-CHECK/captive-hinge-fit-check-geometry.3mf
44.0 x 25.0 x 22.0 mm
