Arcadesys/tak-box/v23-r2/models/tray-right.step

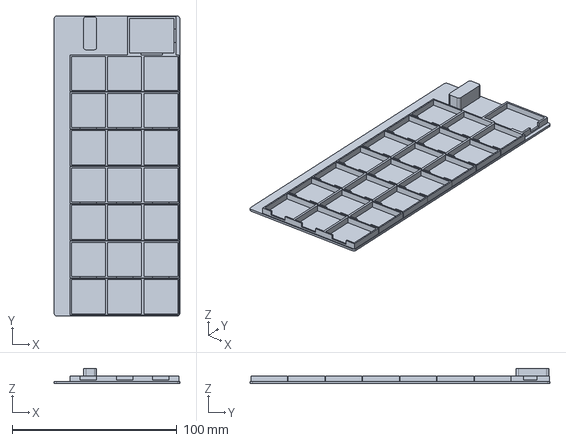
[picture p229: CAD file, 2026-10-09]
v23-r2/models/tray-right.step
76.2 x 182.1 x 9.20 mm
