Arcadesys/tak-box/v23-r2/plates/01-print-in-place-bases.3mf

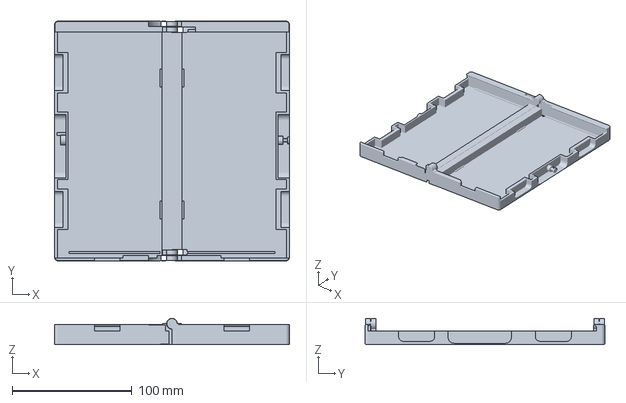
[picture p230: CAD file, 2026-10-09]
v23-r2/plates/01-print-in-place-bases.3mf
196.0 x 200.0 x 22.0 mm
