Arcadesys/tak-box/v23-r2/TRAY-FIT/tray-section.step

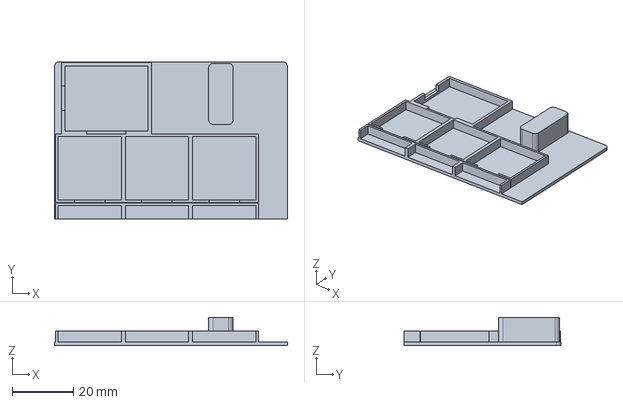
[picture p231: CAD file, 2026-10-09]
v23-r2/TRAY-FIT/tray-section.step
76.2 x 51.5 x 9.20 mm
