Arcadesys/tak-box/v26/FULL-PRINT/01-V26-PIP-guides-and-hook-CC2-PLA.3mf

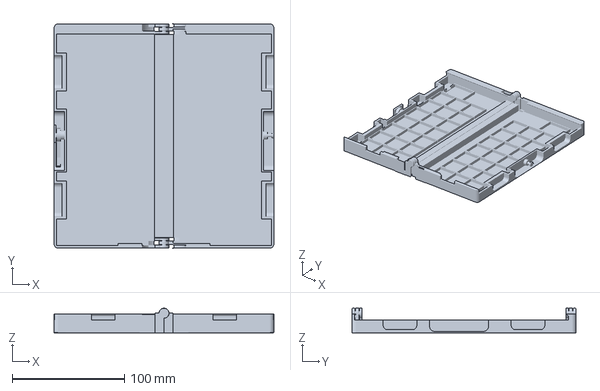
[picture p232: CAD file, 2026-10-09]
v26/FULL-PRINT/01-V26-PIP-guides-and-hook-CC2-PLA.3mf
196.0 x 200.0 x 22.0 mm
