Arcadesys/tak-box/v26/models/board-right-body.step

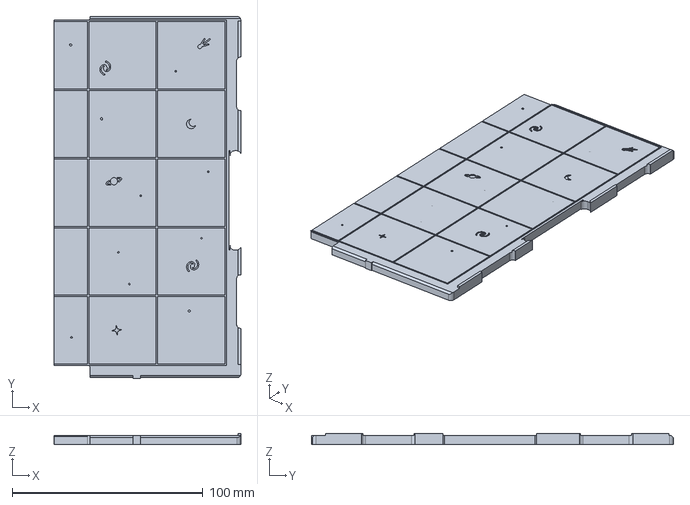
[picture p233: CAD file, 2026-10-09]
v26/models/board-right-body.step
97.8 x 189.6 x 5.70 mm
