Arcadesys/tak-box/v26/plates/02-V26-board-clip-trial.3mf

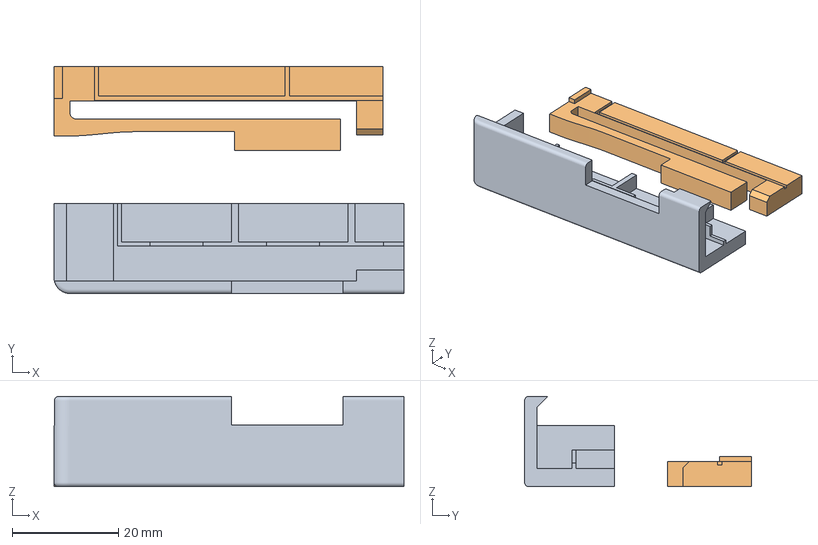
[picture p234: CAD file, 2026-10-09]
v26/plates/02-V26-board-clip-trial.3mf
66.0 x 42.8 x 17.0 mm
clip-trial-seat
clip-trial-board
