Arcadesys/tak-box/v26/reference/board-inlays/board-right-grid.step

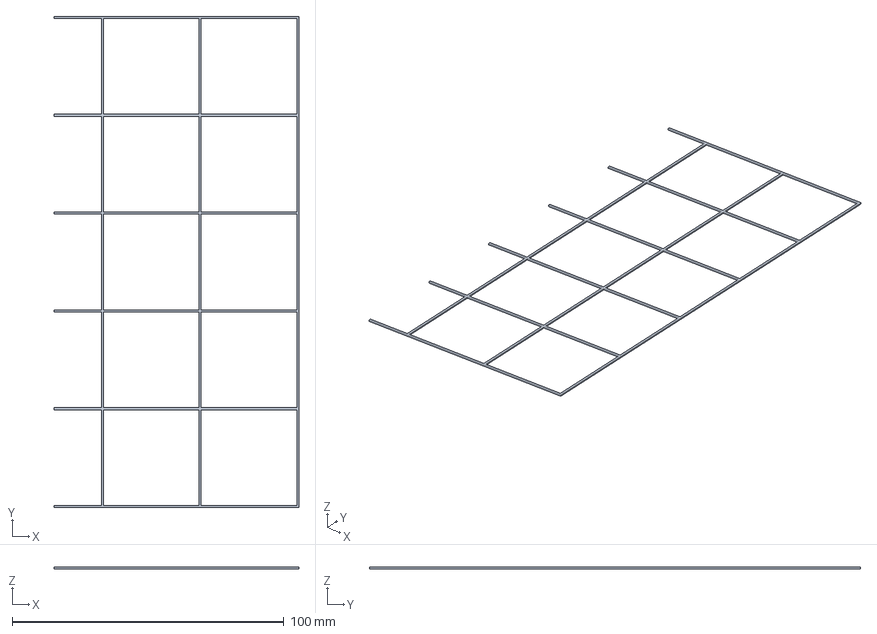
[picture p235: CAD file, 2026-10-09]
v26/reference/board-inlays/board-right-grid.step
90.2 x 180.8 x 0.6 mm
