Arcadesys/tak-box/v26/reference/plain-bodies/housing-design-right.step

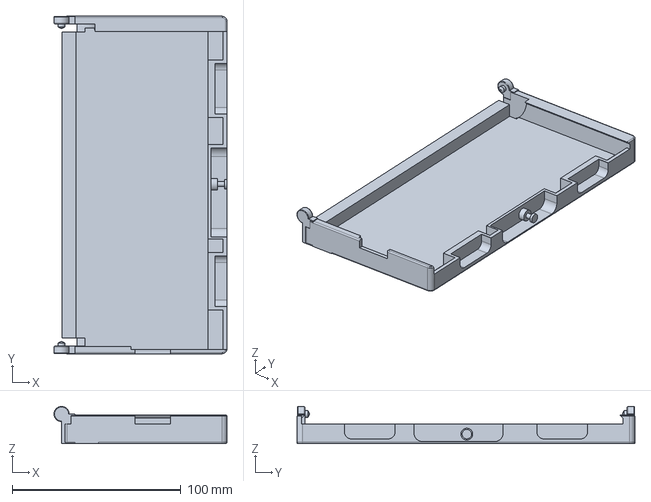
[picture p236: CAD file, 2026-10-09]
v26/reference/plain-bodies/housing-design-right.step
102.5 x 200.0 x 22.0 mm
