Arcadesys/tak-box/centauri-carbon-2-3mf/tak-pin-board-cc2-80-white-center-row-plugs.3mf

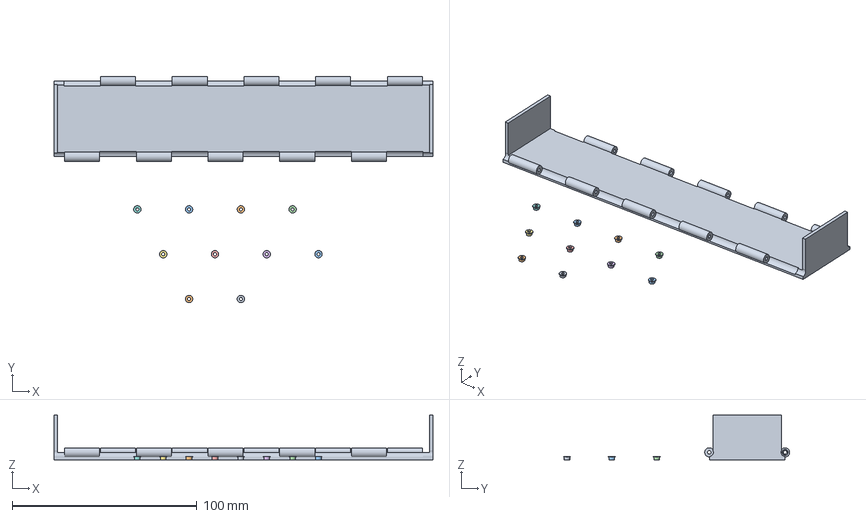
[picture p237: CAD file, 2026-09-26]
centauri-carbon-2-3mf/tak-pin-board-cc2-80-white-center-row-plugs.3mf
205.0 x 122.5 x 24.1 mm
center-row.stl
plug.stl x 10
