Arcadesys/tak-box/center-closure-coupon/coupon-wing-2.stl

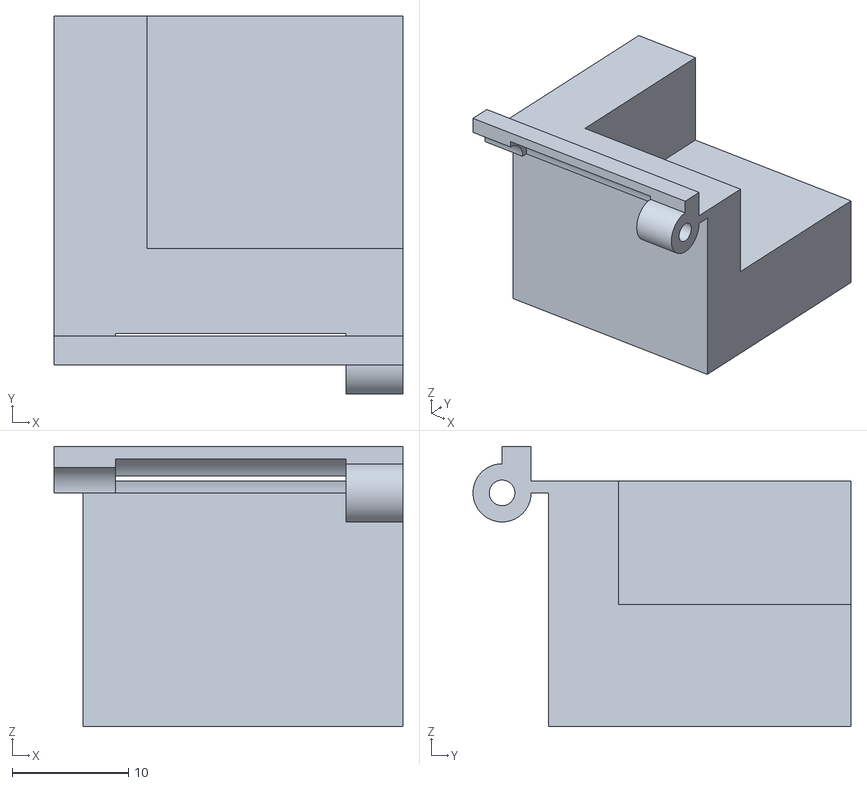
[picture p238: CAD file, 2026-09-27]
center-closure-coupon/coupon-wing-2.stl
30.0 x 32.5 x 24.1
