Arcadesys/tak-box/fit-coupon/lid-hinge-pin.stl

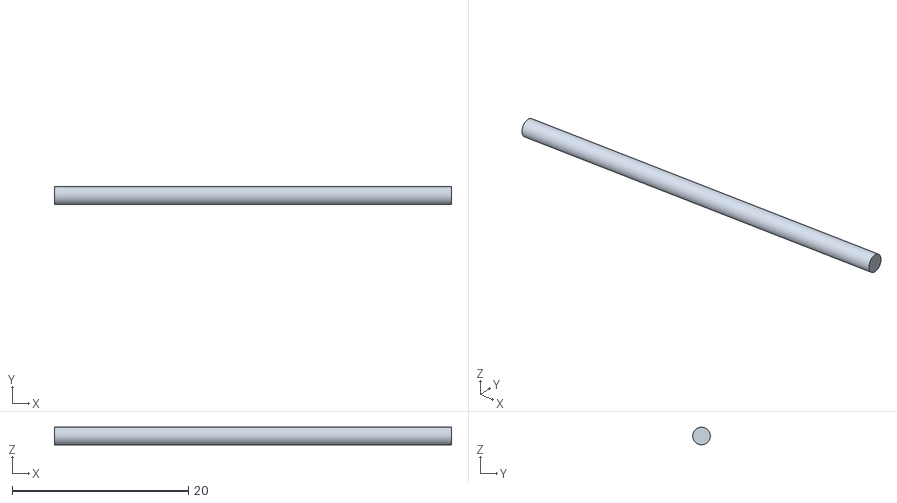
[picture p240: CAD file, 2026-09-25]
fit-coupon/lid-hinge-pin.stl
45.0 x 2.00 x 2.00
