Arcadesys/tak-box/full-size-pagoda-v1/models/floor-clearance-15.step

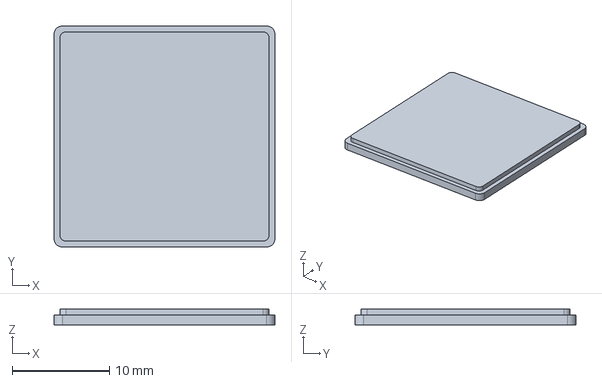
[picture p241: CAD file, 2026-10-03]
full-size-pagoda-v1/models/floor-clearance-15.step
22.7 x 22.7 x 1.60 mm
