Arcadesys/tak-box/v25/PIP-FIXED-GUIDES/README.md

# V25 PIP with fixed piece guides

Start with [the print and test guide](START-HERE.md). Each case half has permanent guides for 21 flats and one capstone, joined to its integral floor. No removable tray. Digital checks do not qualify physical fit or hinge strength.
