Arcadesys/tak-box/v17-squeeze-latch/previews/assembled.png

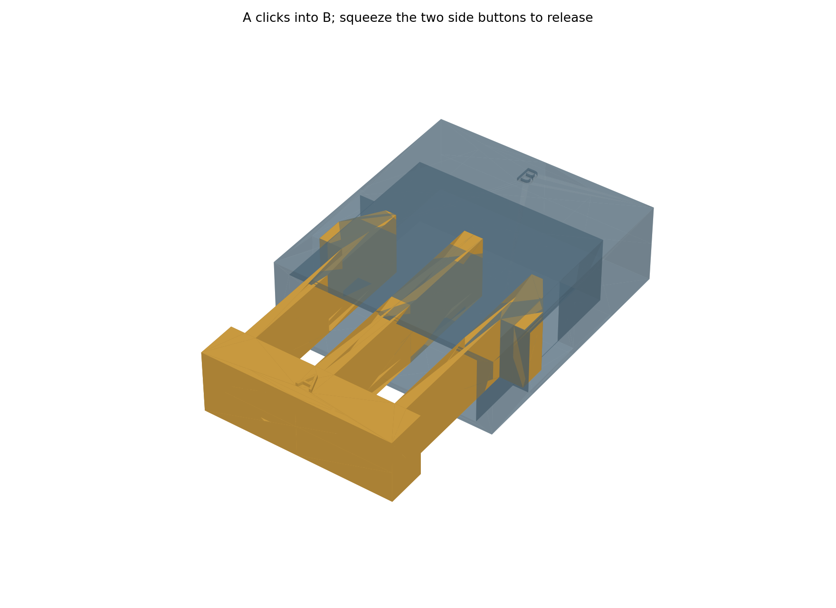
v17-squeeze-latch/previews/assembled.png
