Arcadesys/tak-box/v17-squeeze-latch/previews/print-plate.png

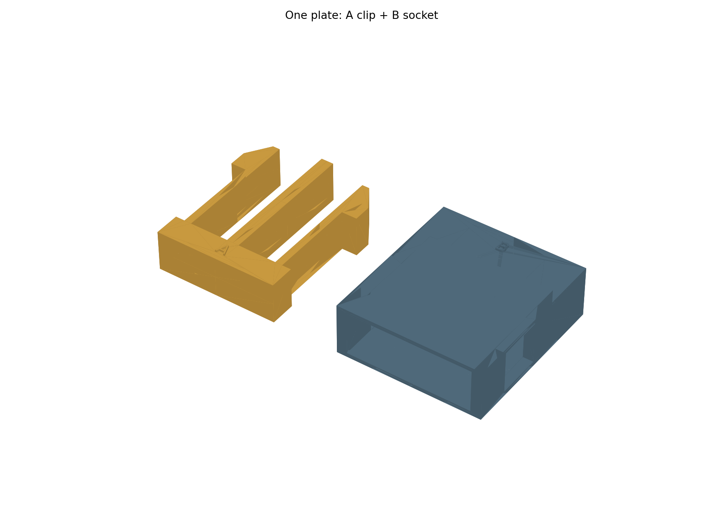
v17-squeeze-latch/previews/print-plate.png
