Arcadesys/tak-box/v23-r2/previews/01-print-in-place-bases-layers.png

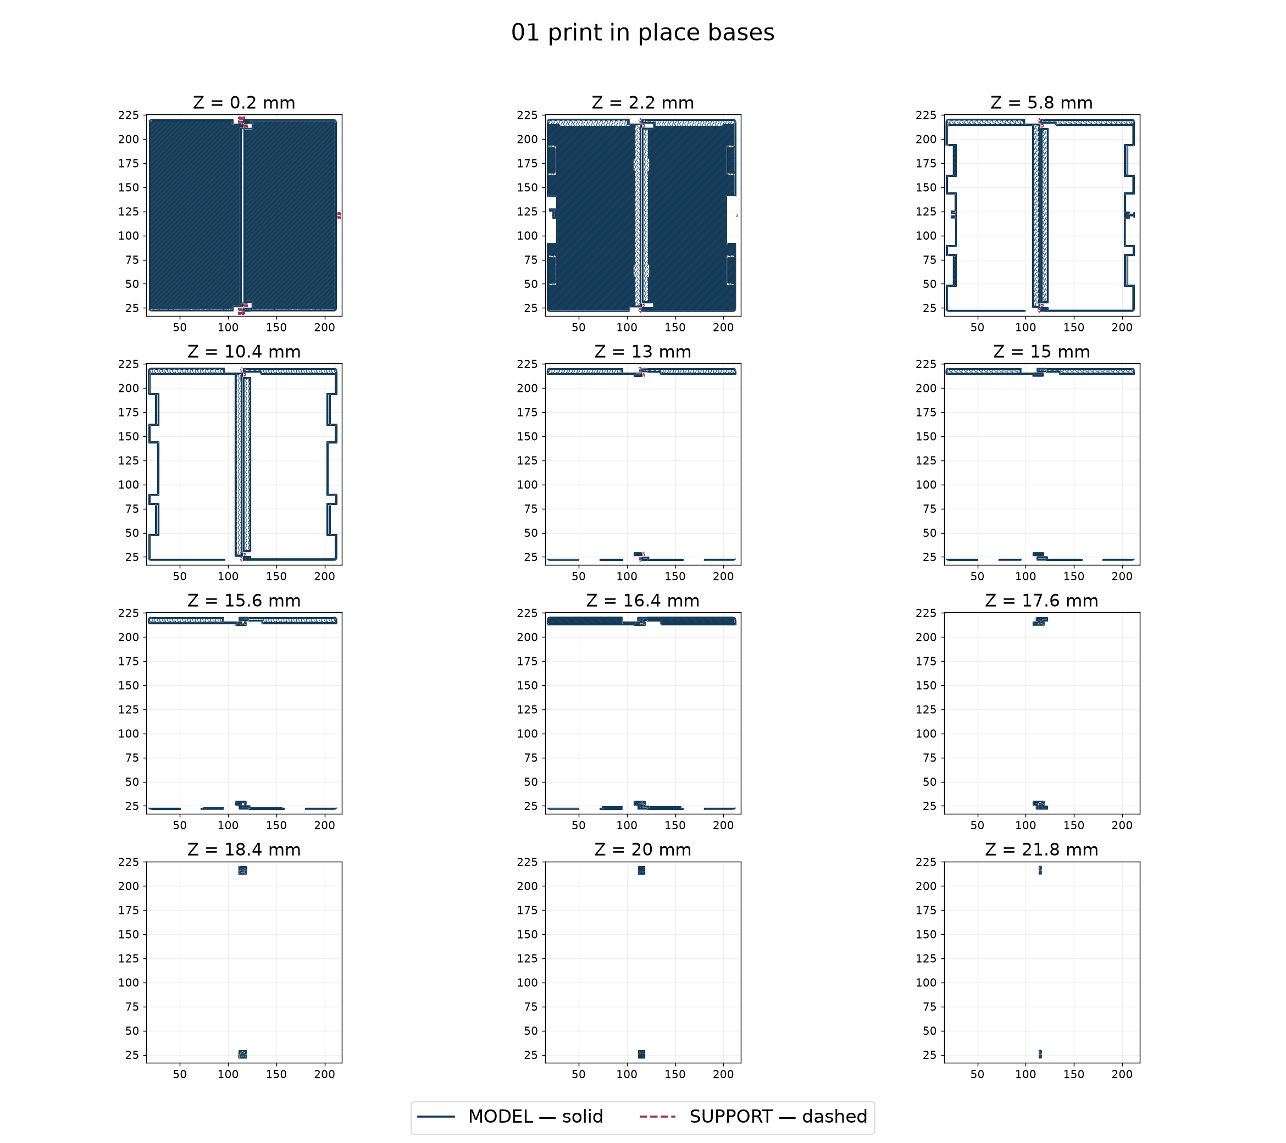
v23-r2/previews/01-print-in-place-bases-layers.png
