Arcadesys/tak-box/v23-r2/previews/03-table-setup.png

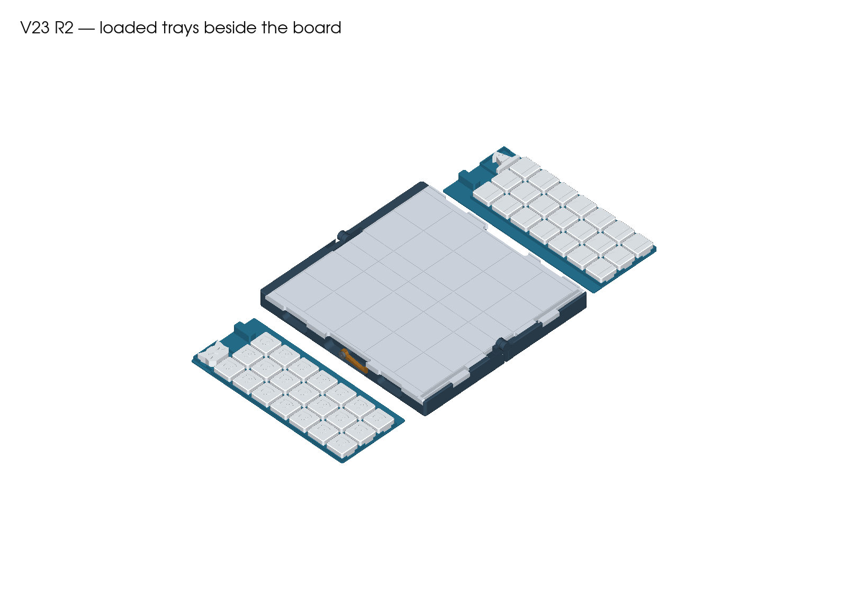
v23-r2/previews/03-table-setup.png
