Arcadesys/tak-box/v24/REFERENCE/HISTORY/README.md

# Historical kits — use FULL-PRINT for the current build

The current printing guide is [START-HERE](../../START-HERE.md). The current download is `v24/V24-PRINT-KIT.zip`, two levels above this folder.

Preserved here:

- `tak-v24-print-kit.zip`: accepted four-colour kit before this folder cleanup.
- `archive/tak-v24-before-board-inlays.zip`: previous monochrome V24 kit.
- `v24/`: the user's older monochrome extraction, unchanged.
- `v24 2/`: the user's four-colour extraction, unchanged.

Old names and instructions inside these historical copies describe their original delivery. They are kept for recovery and are excluded from the current ZIP.
