Arcadesys/tak-box/v24/REFERENCE/HISTORY/archive/README.md

# Preserved V24 before playing-surface inlays

`tak-v24-before-board-inlays.zip` is the complete previously delivered monochrome V24 kit at b766181. SHA-256: `5d48e11d789e2d2e1de48067df9993958c19a91a95c3c81998b7d06d61d66a9d`.

The active kit in the parent release directory replaces board plate 02 with the accepted four-colour surface. This archive preserves the prior models, projects, profiles, source and validation without changing earlier V23 or V23 R2 archives.
